OpeningDesign/Lake_Kegonsa_Home/Transfer/20150805 - driveway/20150805 - Kegonsa - Driveway.pdf

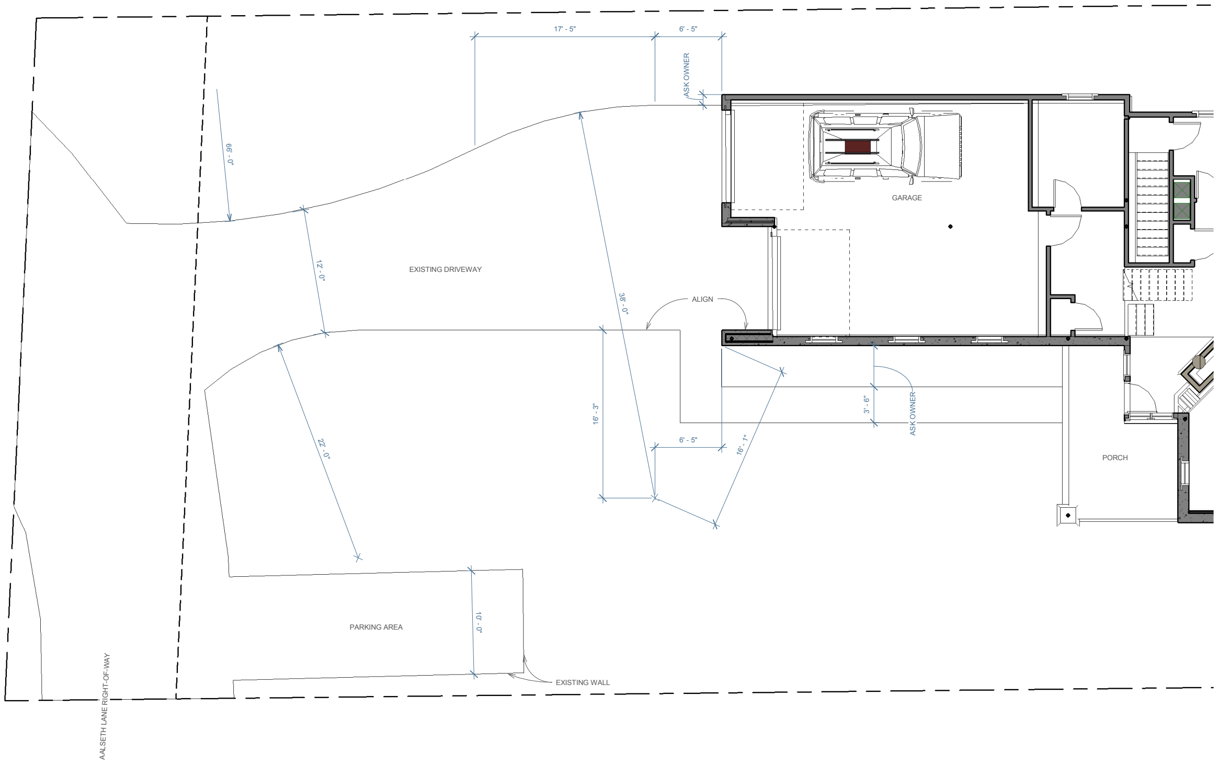
[picture p17: page 1]

EXISTING DRIVEWAY

# AALSETH LANE RIGHT-OF-WAY

GARAGE

PORCH

PARKING AREA

ALIGN

ASK OWNER

66' - 0"

22' - 0"

12' - 0"

10' - 0"

EXISTING WALL

16' - 3"

6' - 5"

3' - 6"

ASK OWNER

6' - 5"

38' - 0"

16' - 1"

17' - 5"
