OpeningDesign/Lake_Kegonsa_Home/Transfer/20150128 - lateral stability/20150128 - lateral stability.pdf

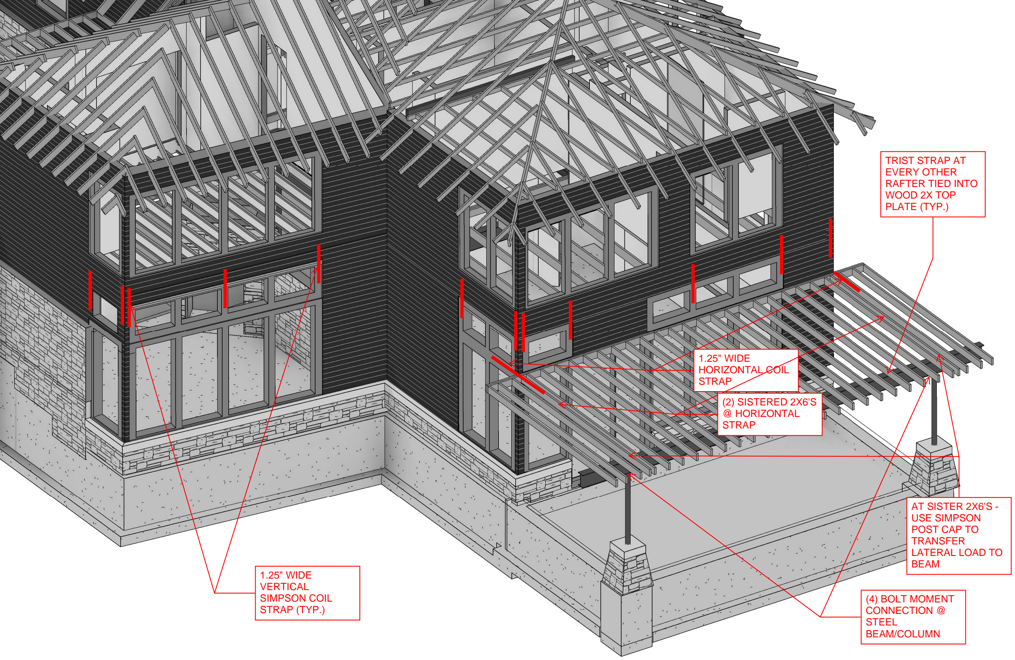
[picture p18: page 1]
