OpeningDesign/Lake_Kegonsa_Home/Transfer/20150119 - Framing - 1st Floor/20150119 - Framing - 1st Floor.pdf

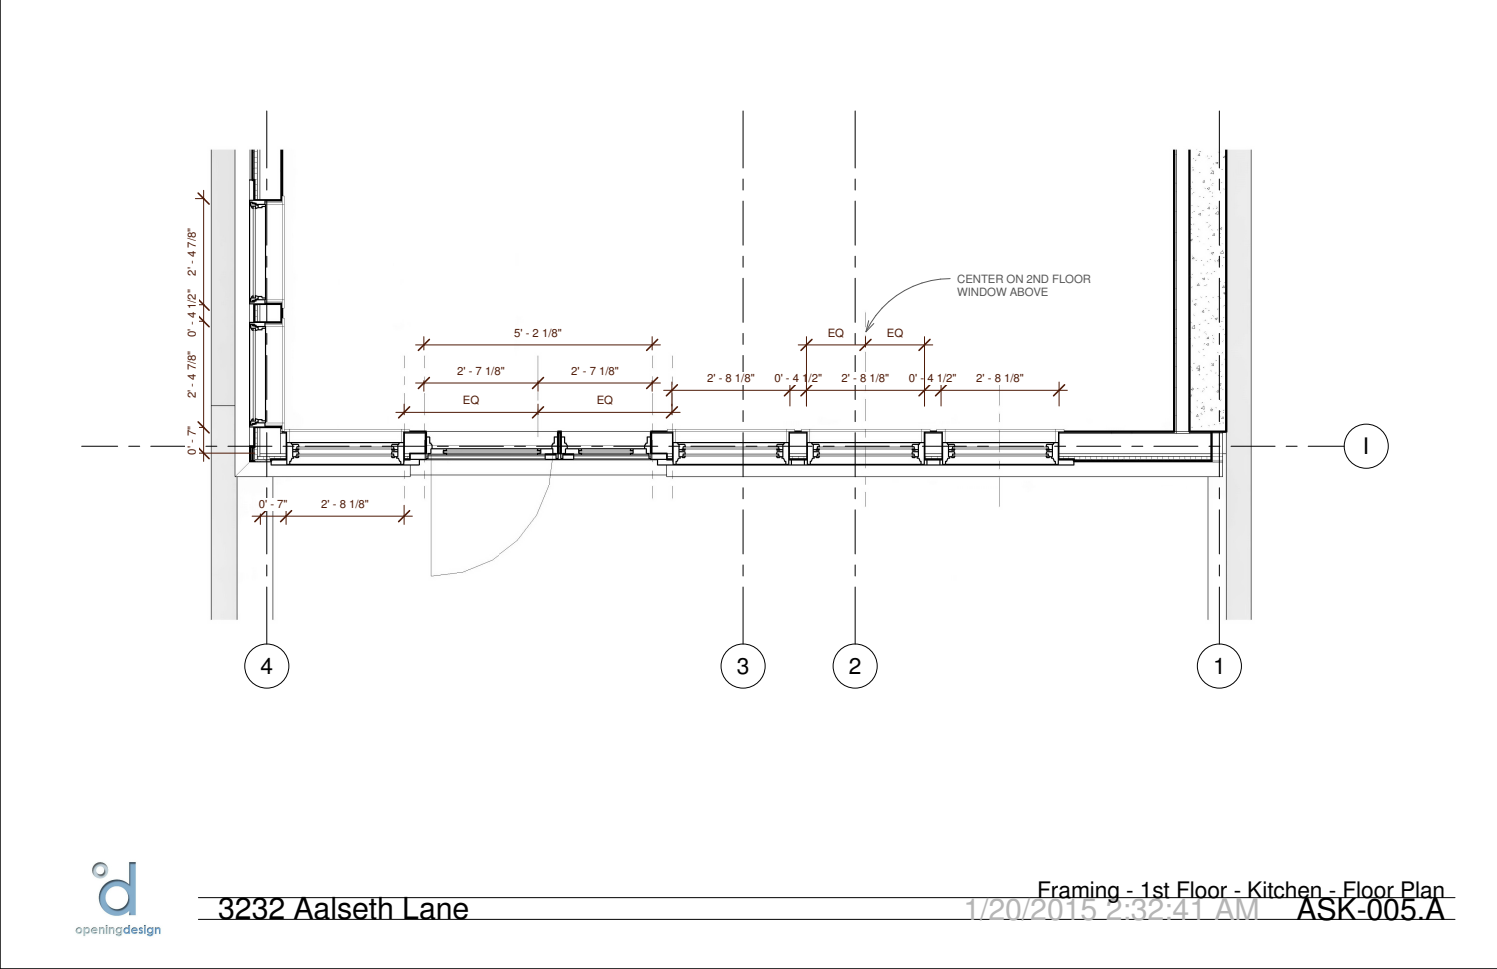
[picture p19: page 1]
ASK-005.A Framing - 1st Floor - Kitchen - Floor Plan 3232 Aalseth Lane

2' - 4 7/8" 0' - 4 1/2" 2' - 4 7/8" 0' - 7" 2' - 8 1/8" 0' - 4 1/2" 2' - 8 1/8" 0' - 4 1/2" 2' - 8 1/8" EQ EQ CENTER ON 2ND FLOOR WINDOW ABOVE EQ EQ

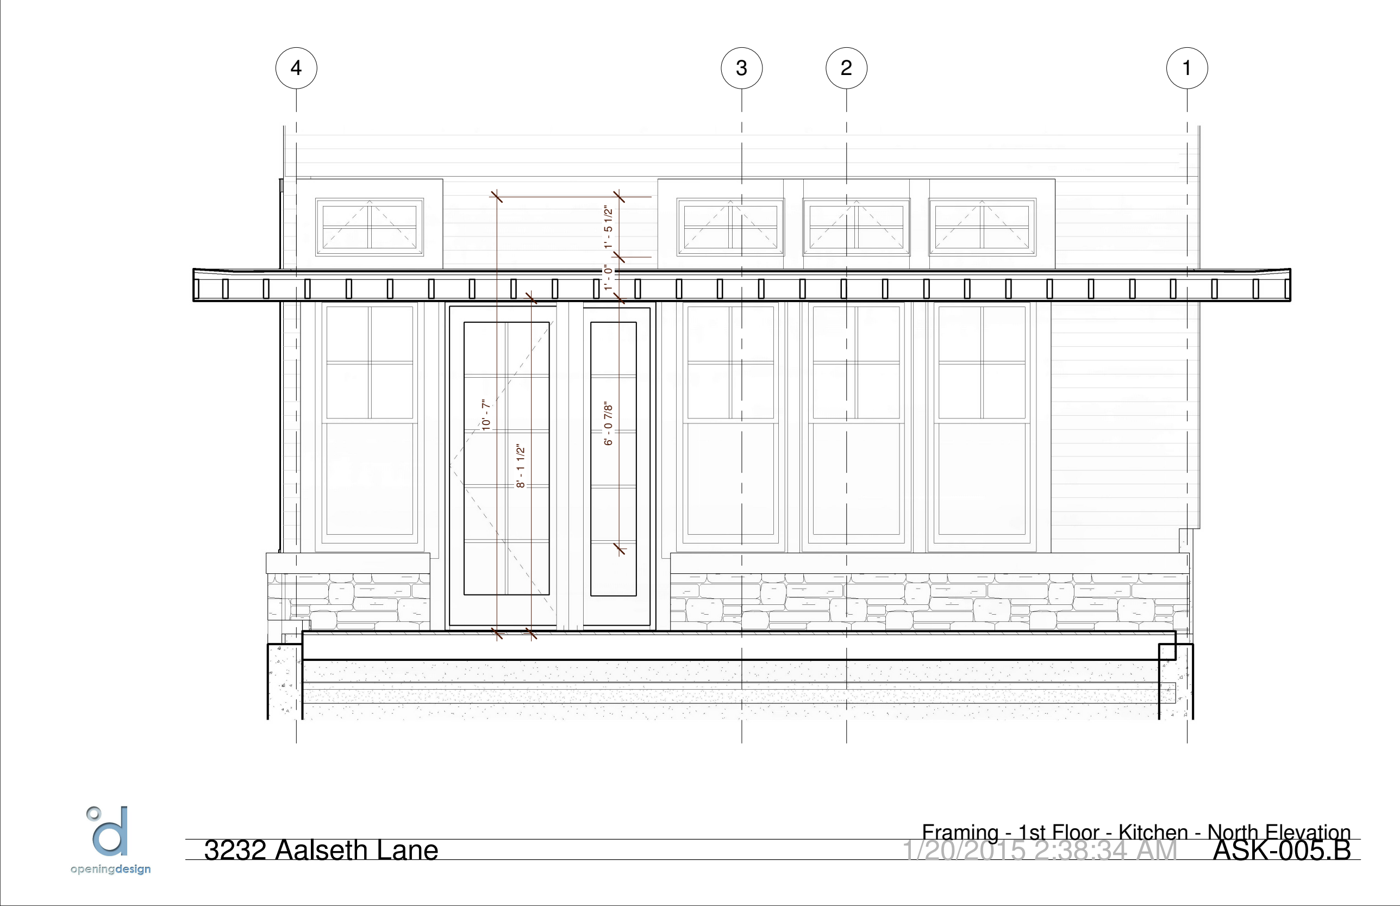
[picture p20: figure]

1/20/2015 2:38:34 AM ASK-005.B Framing - 1st Floor - Kitchen - North Elevation 3232 Aalseth Lane

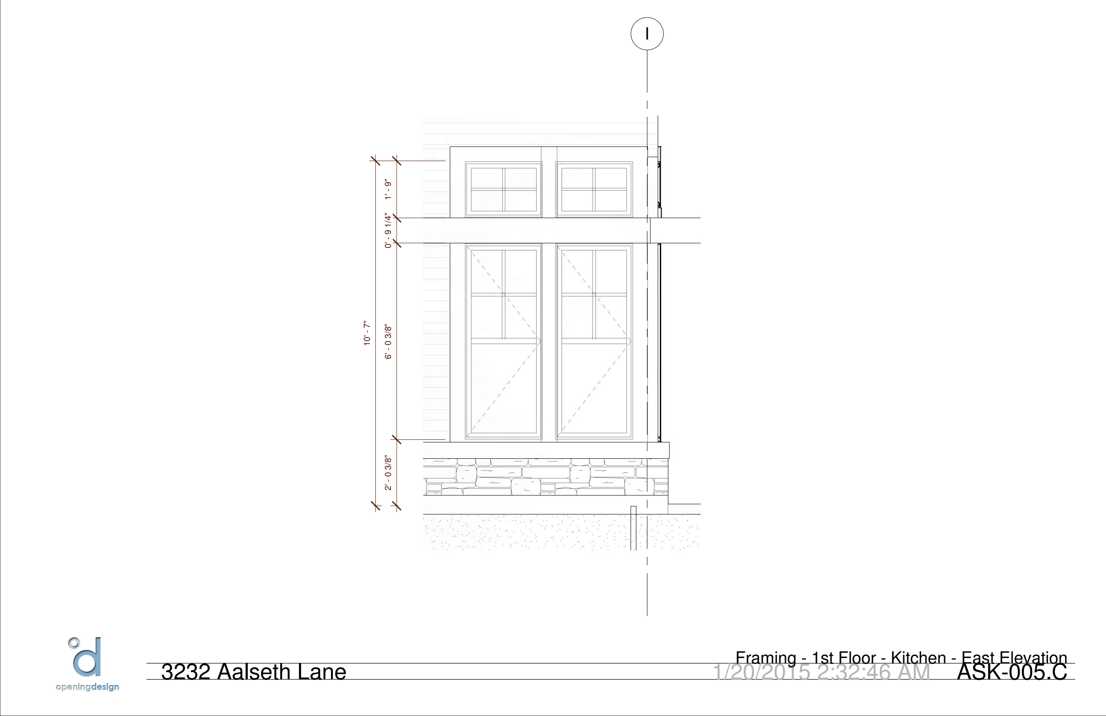
[picture p21: figure]

1' - 9" 0' - 9 1/4" 6' - 0 3/8" 2' - 0 3/8"

1/20/2015 2:32:46 AM ASK-005.C Framing - 1st Floor - Kitchen - East Elevation 3232 Aalseth Lane

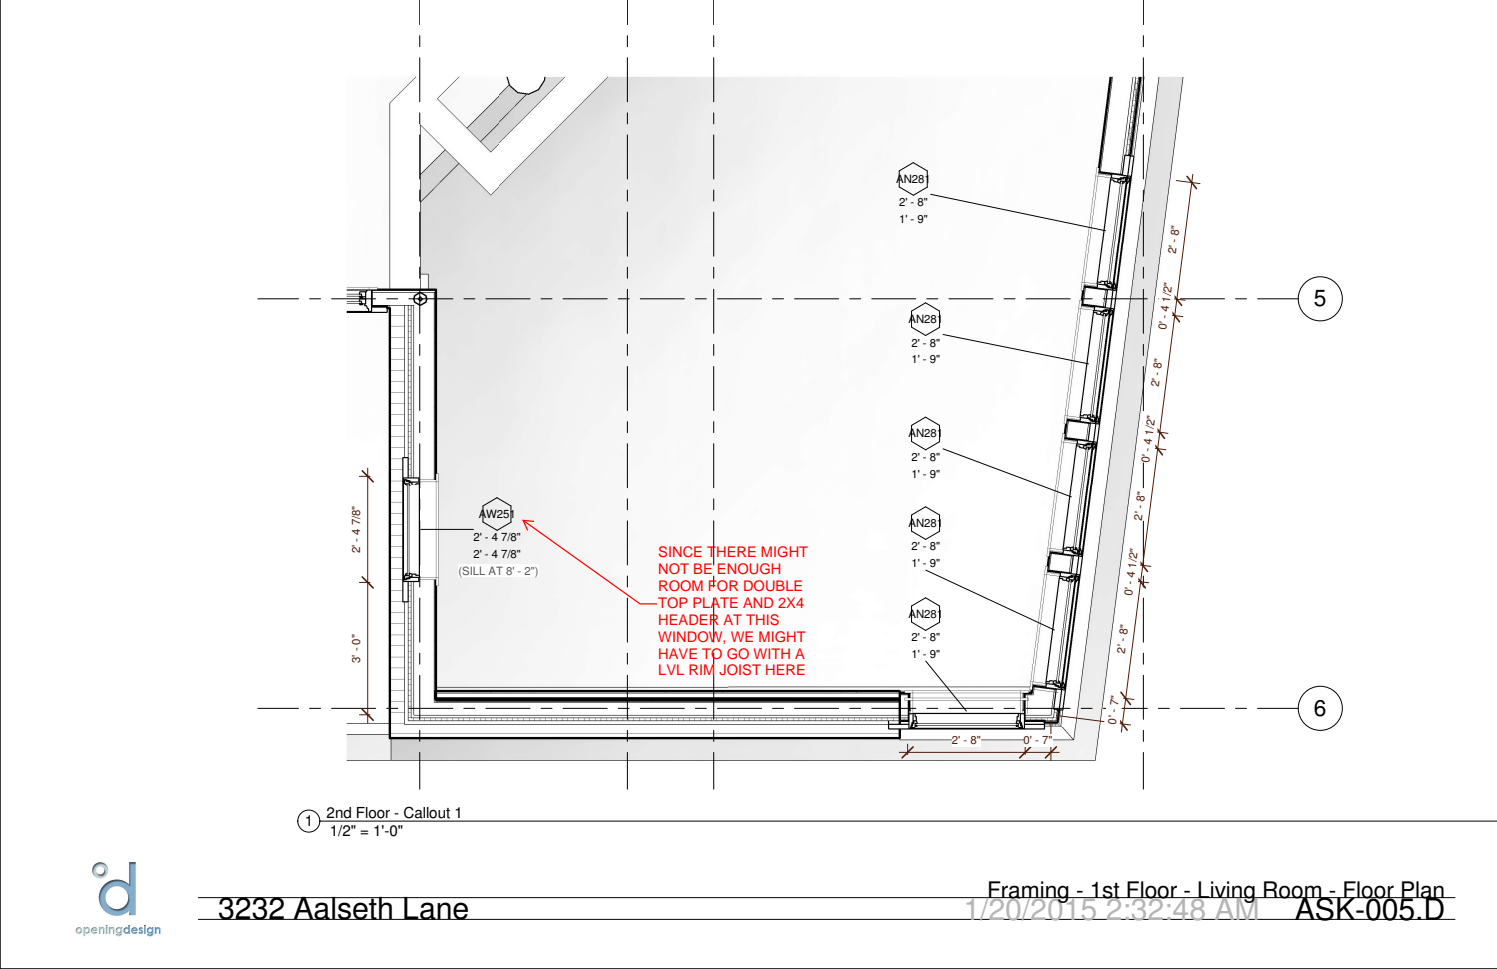
[picture p22: page 4]
(SILL AT 8' - 2"); ASK-005.D Framing - 1st Floor - Living Room - Floor Plan 3232 Aalseth Lane; 1/2" = 1'-0" 1 2nd Floor - Callout 1

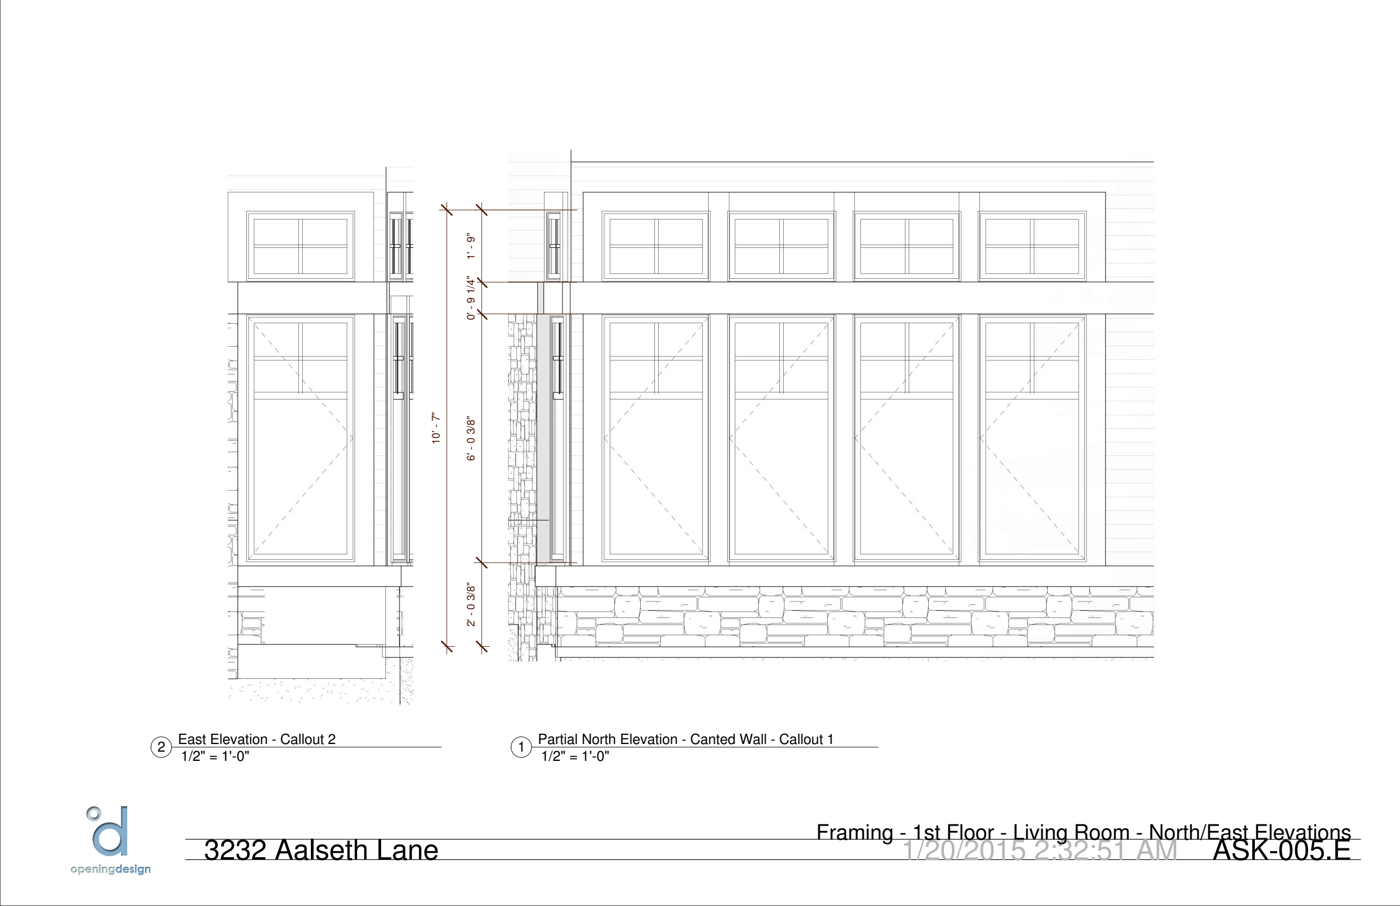
[picture p23: figure]

2' - 0 3/8" 6' - 0 3/8" 0' - 9 1/4" 1' - 9"

1/20/2015 2:32:51 AM ASK-005.E Framing - 1st Floor - Living Room - North/East Elevations 3232 Aalseth Lane

1/2" = 1'-0" 1 Partial North Elevation - Canted Wall - Callout 1 1/2" = 1'-0" 2 East Elevation - Callout 2
