OpeningDesign/Lake_Kegonsa_Home/Transfer/20150122 - 1st Floor Plan/20150122 - 1st Floor Plan.pdf

D | H
B | J

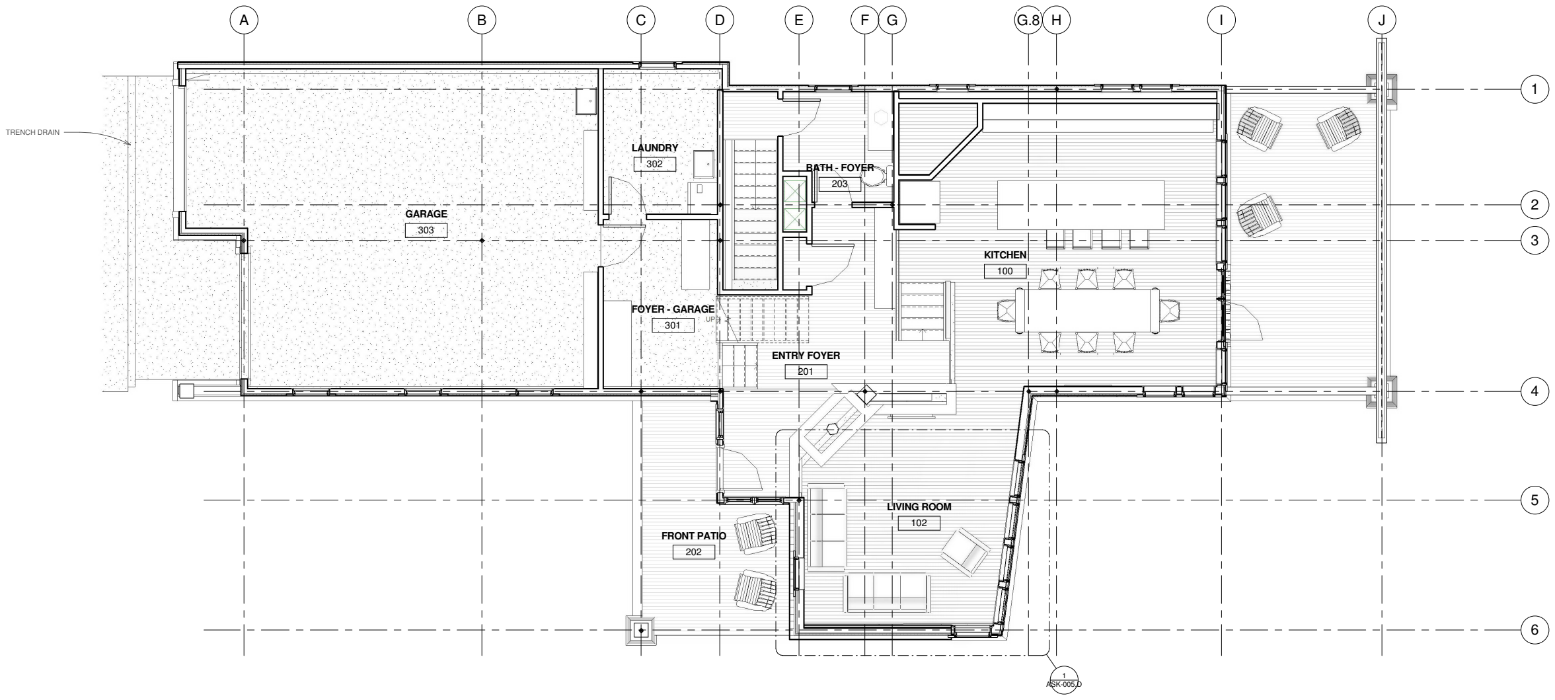
[picture p24: page 1]

2

4

A | F | G

3

5

E

1

6

C | I

TRENCH DRAIN

KITCHEN

100

LIVING ROOM

102

ENTRY FOYER

201

FRONT PATIO

202

BATH - FOYER

203

FOYER - GARAGE

301

LAUNDRY

302

GARAGE

303

G.8

ASK-005.D

1
