OpeningDesign/Lake_Kegonsa_Home/Transfer/20150125 - Entry/ASK-007b - Entry.pdf

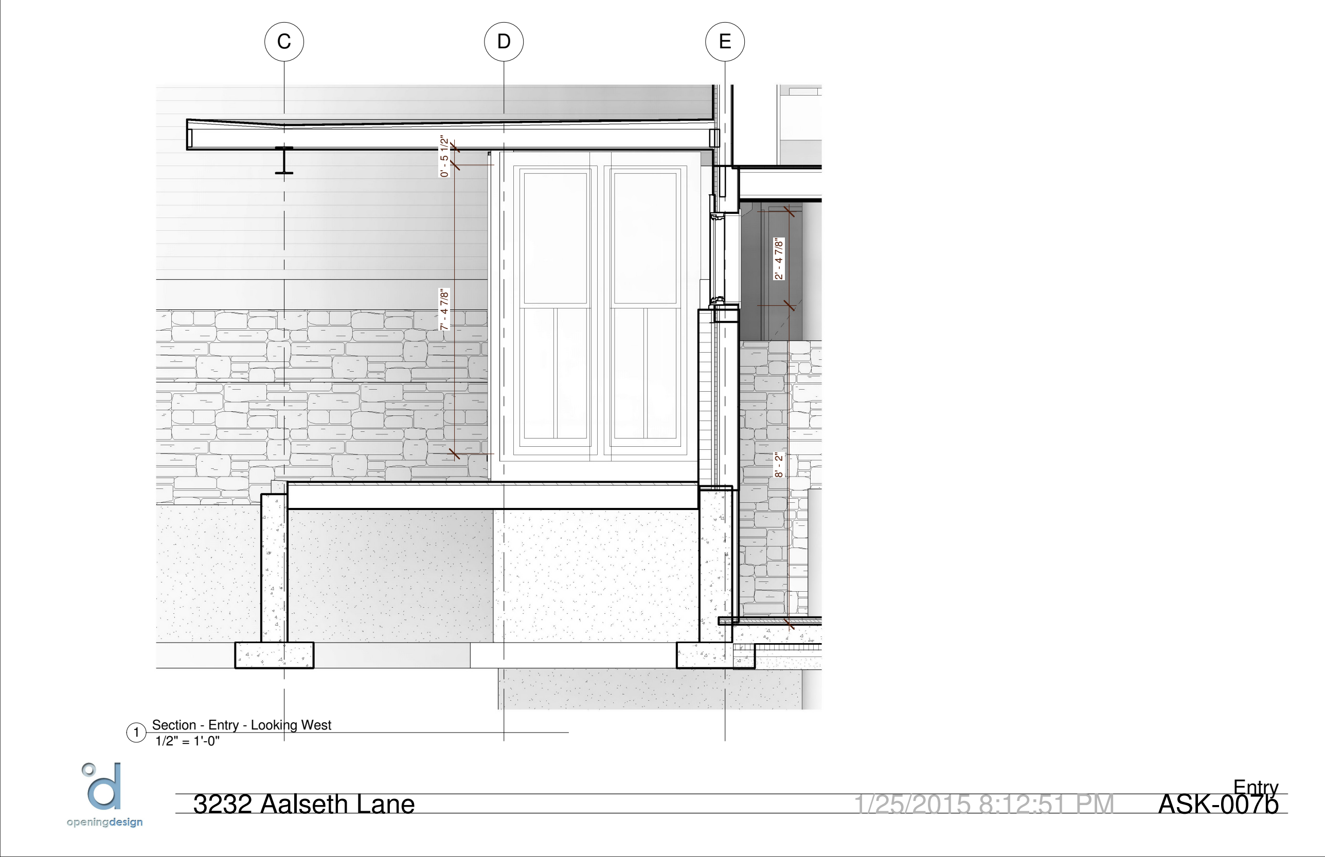
[picture p25: page 1]

C | D | E

0' - 5 1/2" 7' - 4 7/8"

8' - 2" 2' - 4 7/8"

1/25/2015 8:12:51 PM ASK-007b Entry 3232 Aalseth Lane

1/2" = 1'-0" 1 Section - Entry - Looking West
