OpeningDesign/Lake_Kegonsa_Home/Transfer/20150106 - basement and roof structure/20150106_ Structural - Basement.pdf

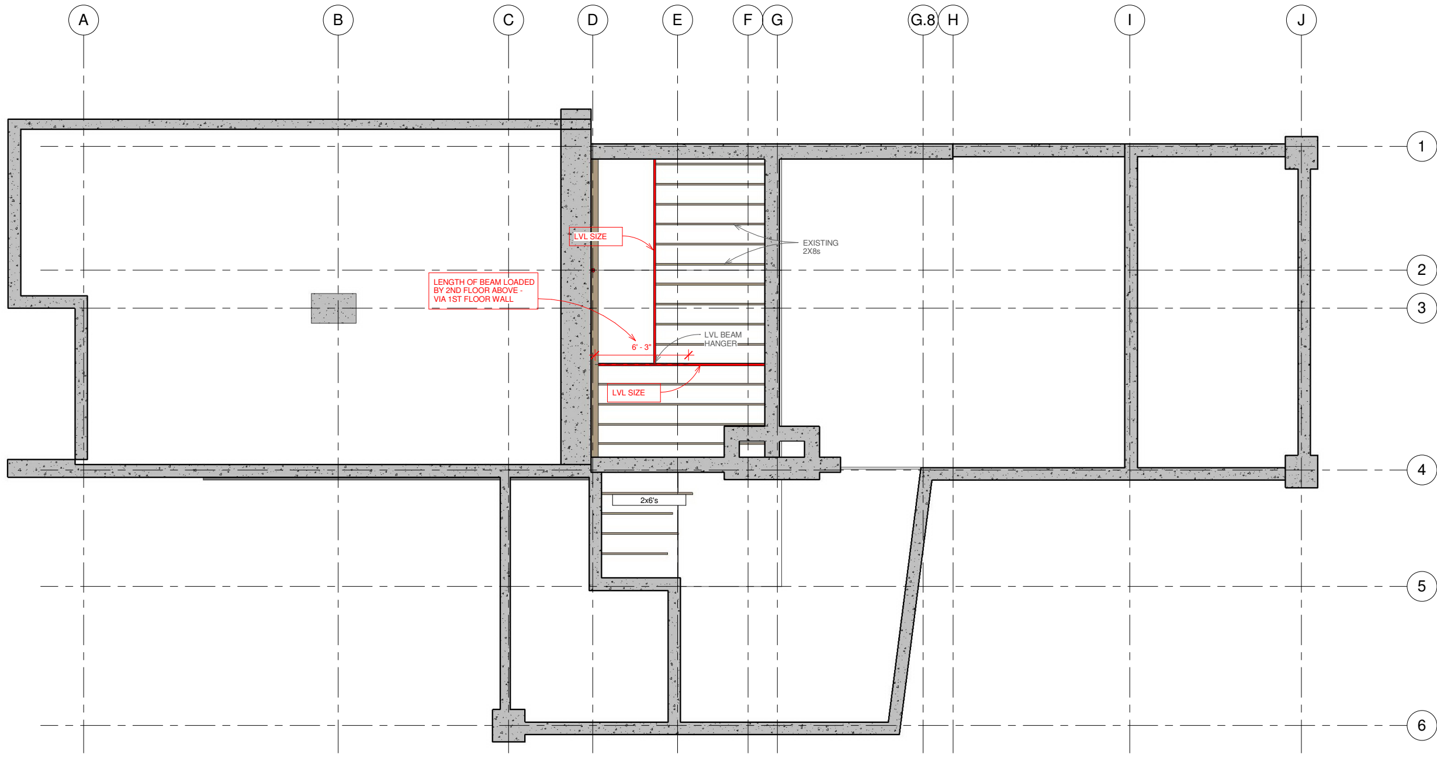
[picture p26: page 1]

D | H

2

B | J

4

A | F | G

3

5

E

1

6

C | I

LVL SIZE

LVL SIZE

6' - 3"

LENGTH OF BEAM LOADED
BY 2ND FLOOR ABOVE -
VIA 1ST FLOOR WALL

LVL BEAM
HANGER

EXISTING
2X8s

2x6's

G.8
