OpeningDesign/Lake_Kegonsa_Home/Transfer/20150106 - basement and roof structure/20150106_ Structural - roof plan.pdf

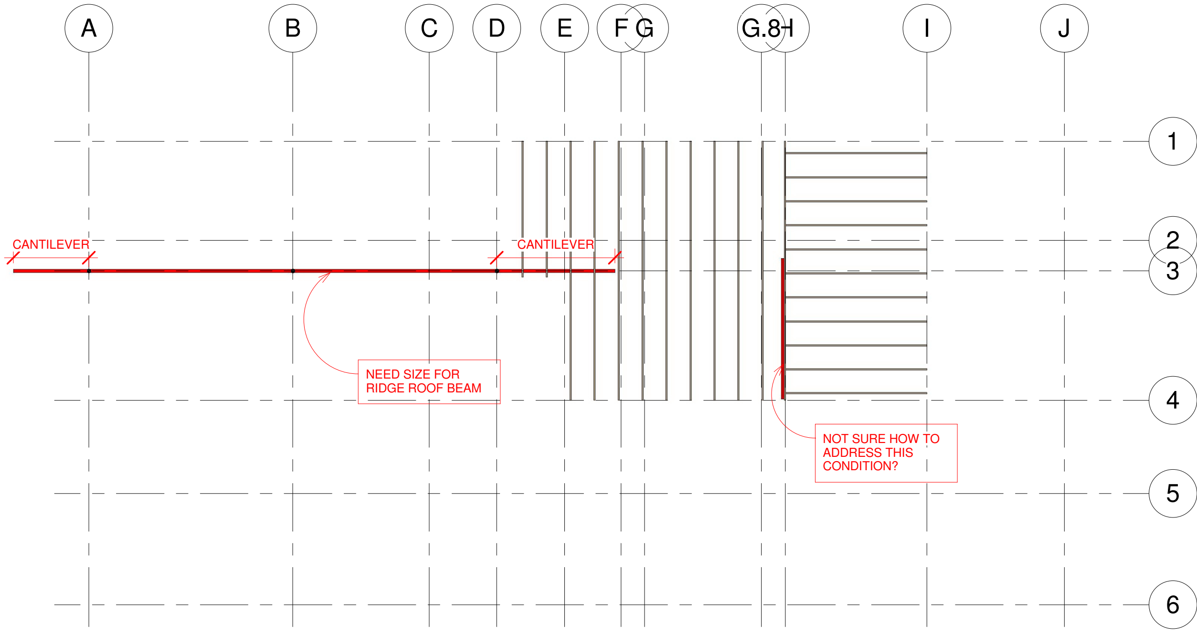
[picture p27: page 1]

D | H

2

B | J

4

A | F G

3

5

E

1

6

C | G.8 | I

NOT SURE HOW TO
ADDRESS THIS
CONDITION?

NEED SIZE FOR
RIDGE ROOF BEAM
CANTILEVER | CANTILEVER
