OpeningDesign/Lake_Kegonsa_Home/Transfer/Endres Mfg_20141222/Question 3.pdf

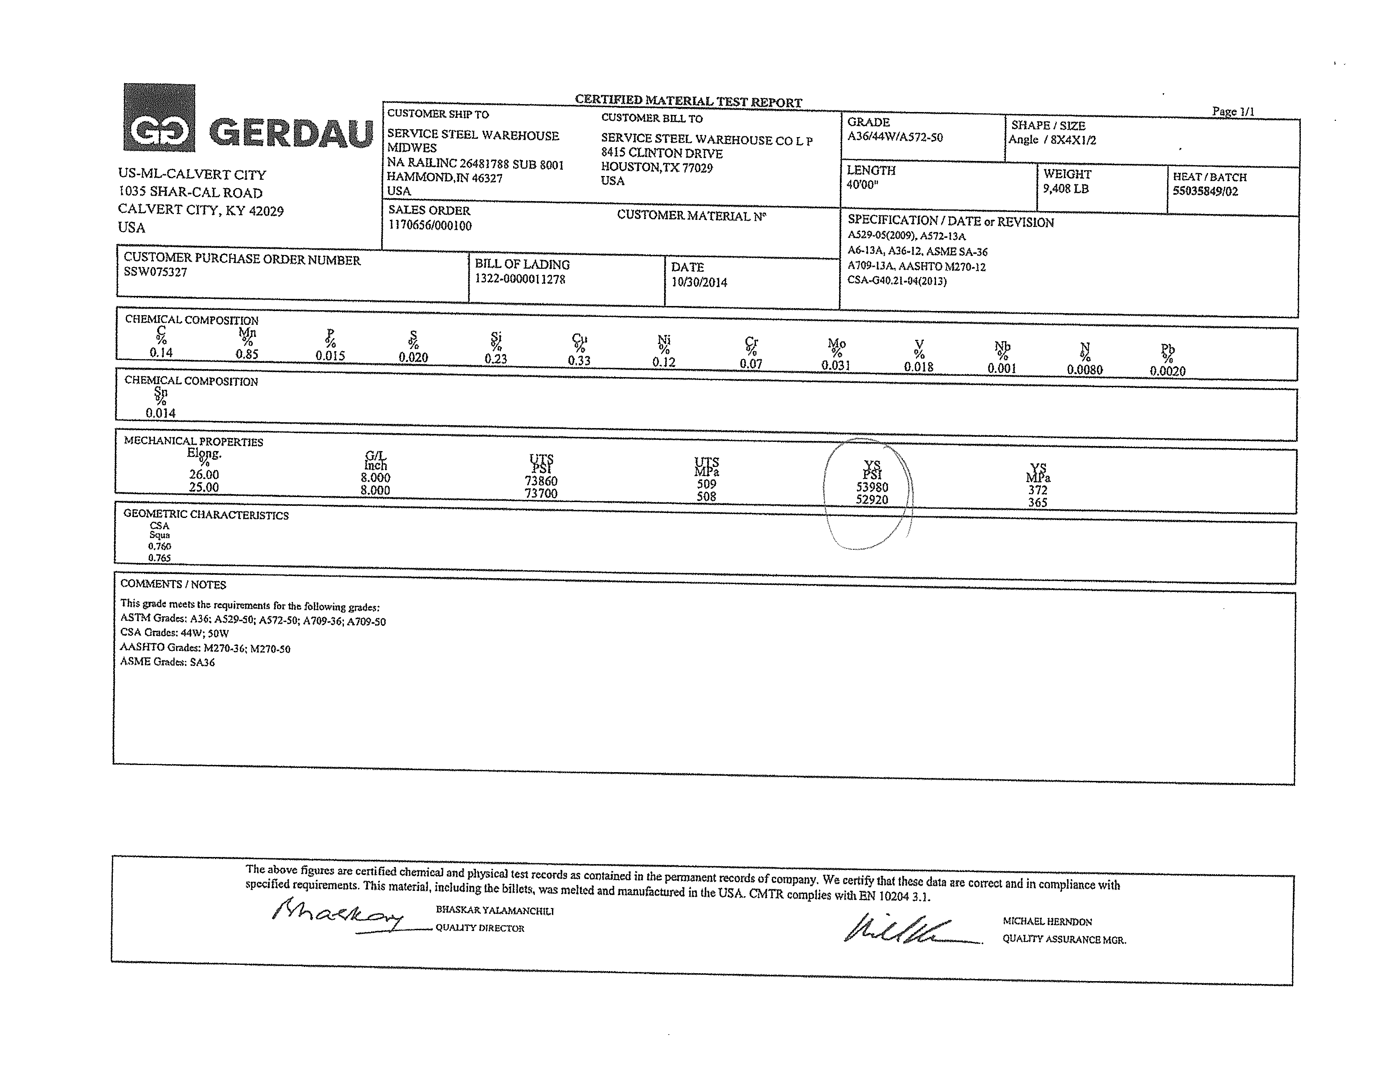
[picture p28: page 1]
