OpeningDesign/Lake_Kegonsa_Home/Transfer/Endres Mfg_20141222/Question 4.pdf

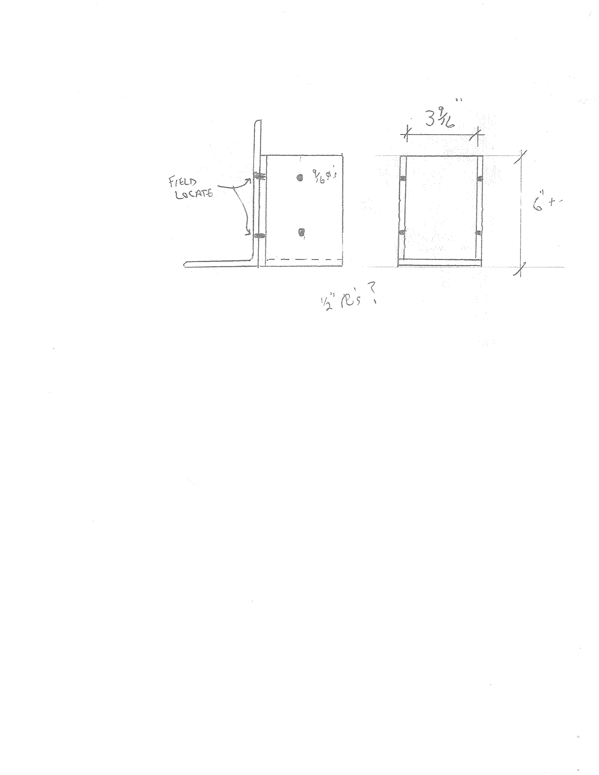
[picture p29: page 1]
