OpeningDesign/Lake_Kegonsa_Home/As-built/Photos and Videos/2014-10-24 10.37.41.jpg

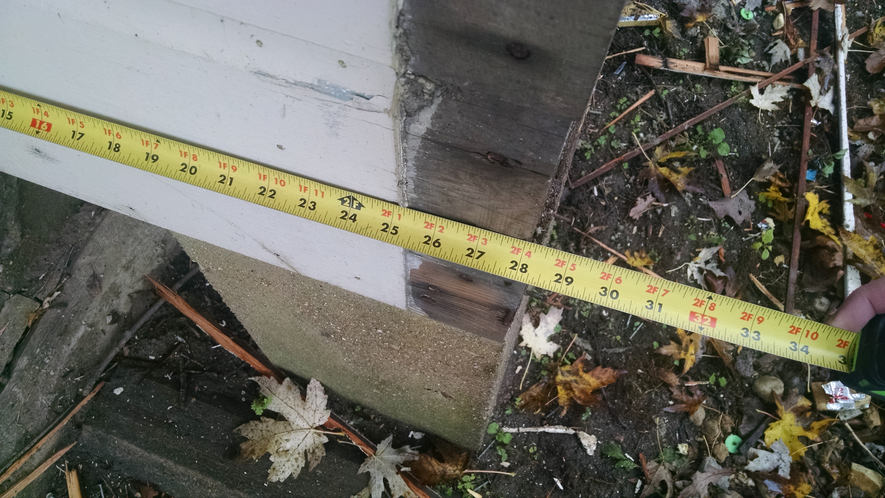
As-built/Photos and Videos/2014-10-24 10.37.41.jpg
