OpeningDesign/Lake_Kegonsa_Home/As-built/Photos and Videos/2014-10-24 10.46.05.jpg

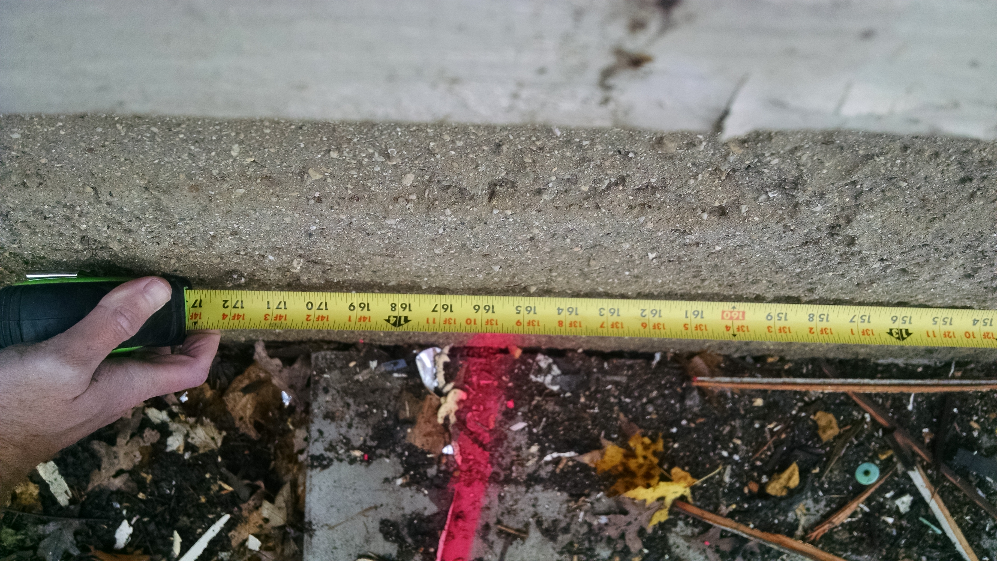
As-built/Photos and Videos/2014-10-24 10.46.05.jpg
