OpeningDesign/Lake_Kegonsa_Home/As-built/Photos and Videos/2014-11-19 15.27.34.jpg

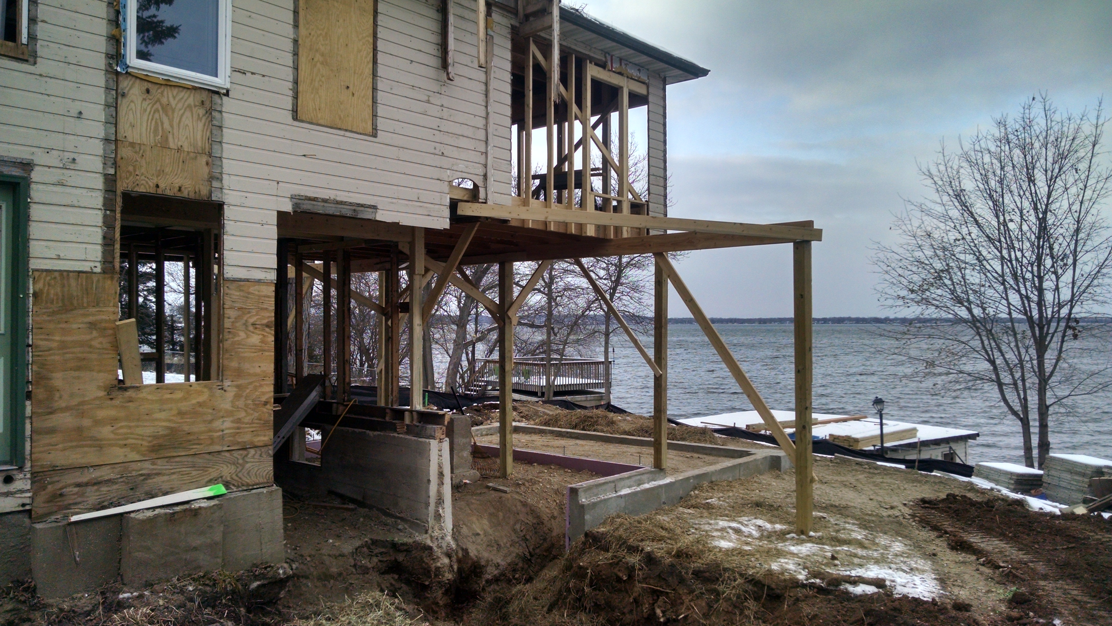
As-built/Photos and Videos/2014-11-19 15.27.34.jpg
