OpeningDesign/Lake_Kegonsa_Home/As-built/plat.jpg

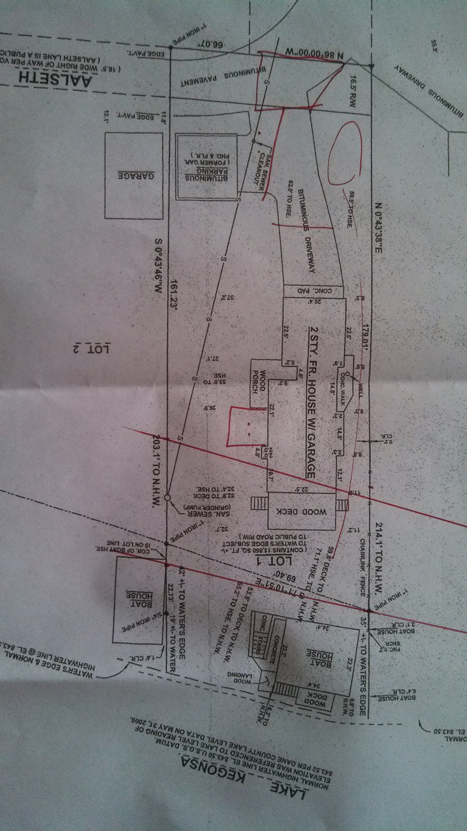
As-built/plat.jpg
