OpeningDesign/Lake_Kegonsa_Home/As-built/site photos/2014-07-19 14.10.41.jpg

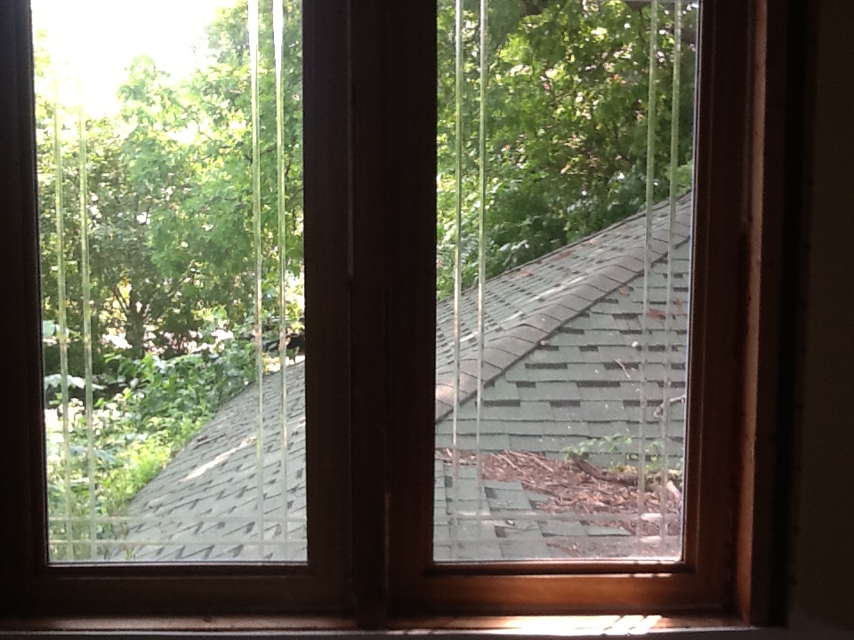
As-built/site photos/2014-07-19 14.10.41.jpg
