OpeningDesign/Lake_Kegonsa_Home/As-built/site photos/2014-07-19 14.11.17.jpg

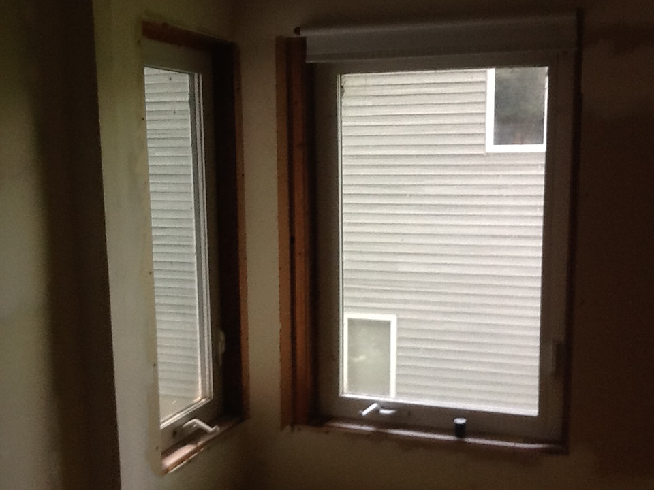
As-built/site photos/2014-07-19 14.11.17.jpg
