OpeningDesign/Lake_Kegonsa_Home/Info/casement - grilles.jpg

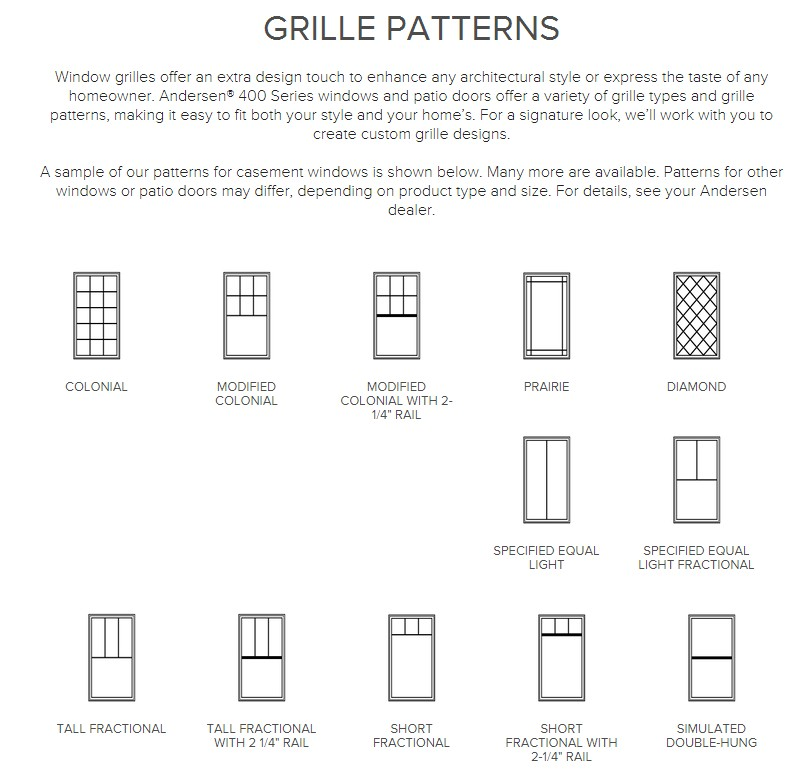
Info/casement - grilles.jpg
