OpeningDesign/Lake_Kegonsa_Home/Info/double hung - grilles.jpg

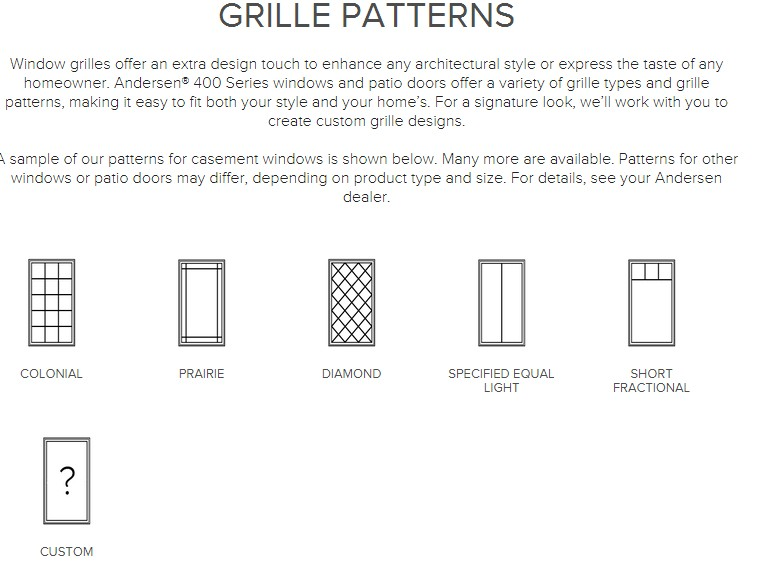
Info/double hung - grilles.jpg
