OpeningDesign/Lake_Kegonsa_Home/Model/Drain-Trench-Zurn-Z886/Product_Image-Zurn-Z886.jpg

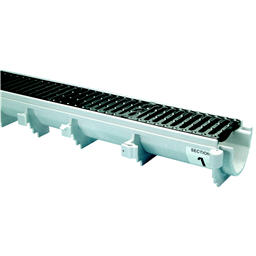
Model/Drain-Trench-Zurn-Z886/Product_Image-Zurn-Z886.jpg
