OpeningDesign/Lake_Kegonsa_Home/Model/turning radius.png

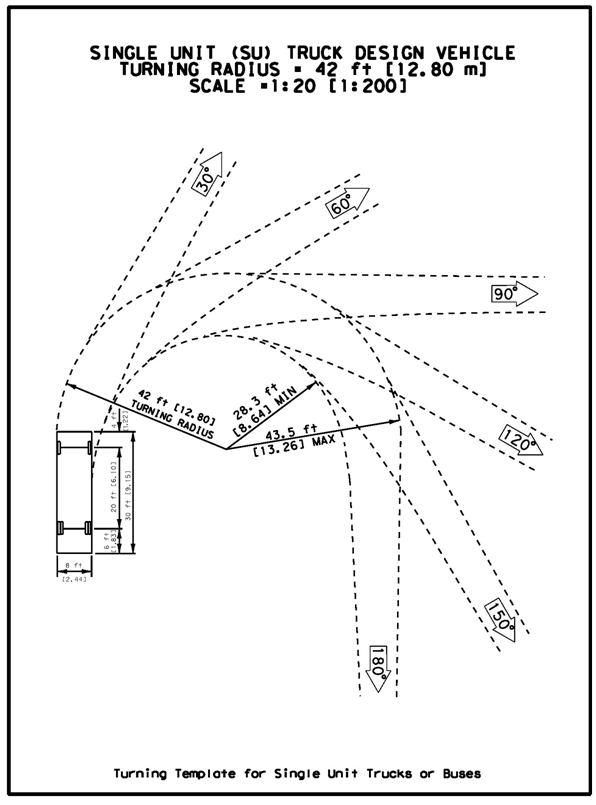
Model/turning radius.png
