OpeningDesign/Lake_Kegonsa_Home/Out/20140901 - Progress set/Lake_Kegonsa_Home Page 011.png

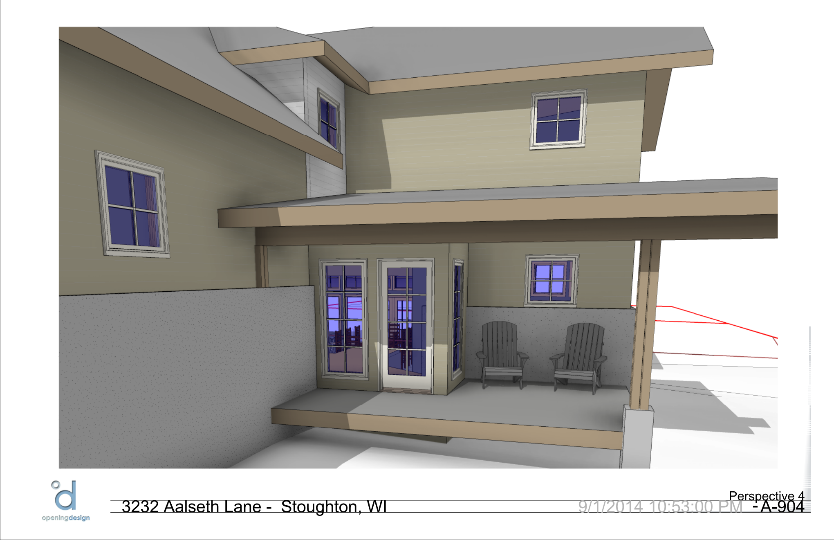
Out/20140901 - Progress set/Lake_Kegonsa_Home Page 011.png
