OpeningDesign/Lake_Kegonsa_Home/Out/20140913 - for review/Lake_Kegonsa_Home Page 002.png

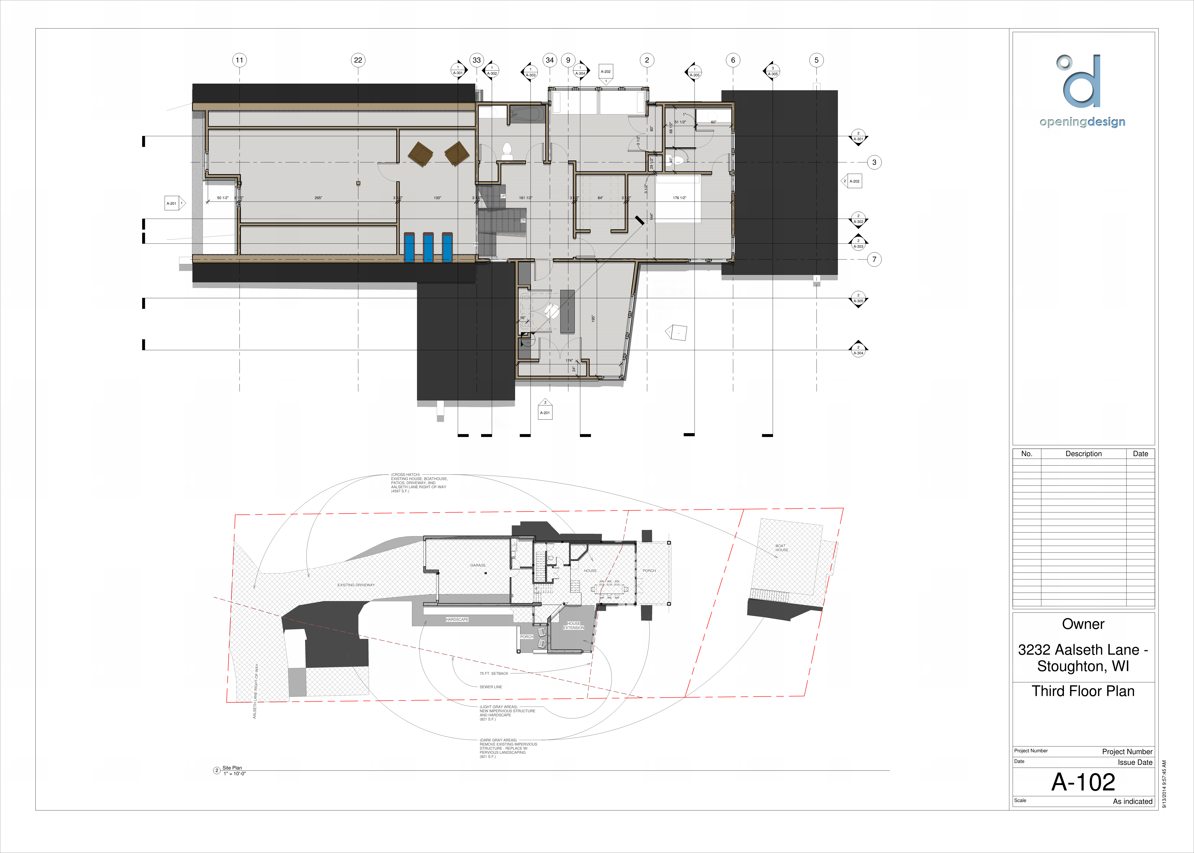
Out/20140913 - for review/Lake_Kegonsa_Home Page 002.png
