OpeningDesign/Lake_Kegonsa_Home/Out/20140929 - Plans for Plumber/ScreenHunter_159 Sep. 29 16.08.jpg

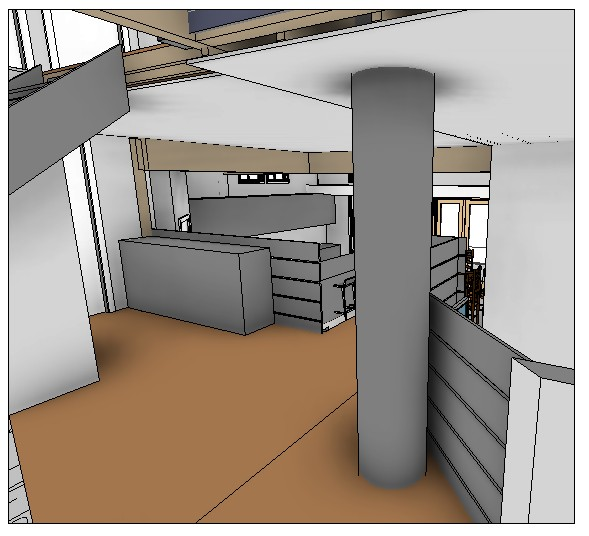
Out/20140929 - Plans for Plumber/ScreenHunter_159 Sep. 29 16.08.jpg
