OpeningDesign/Lake_Kegonsa_Home/Out/20140929 - Plans for Plumber/ScreenHunter_160 Sep. 29 16.10.jpg

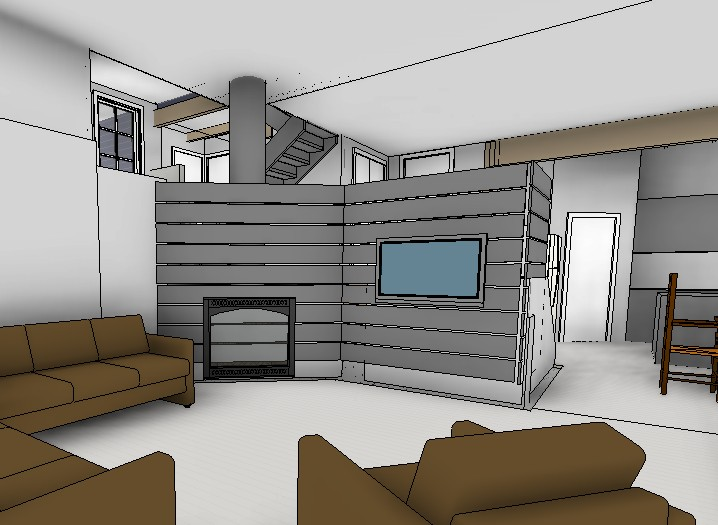
Out/20140929 - Plans for Plumber/ScreenHunter_160 Sep. 29 16.10.jpg
