OpeningDesign/Lake_Kegonsa_Home/Out/20141021 - structural screencapture/ScreenHunter_133 Oct. 21 11.41.jpg

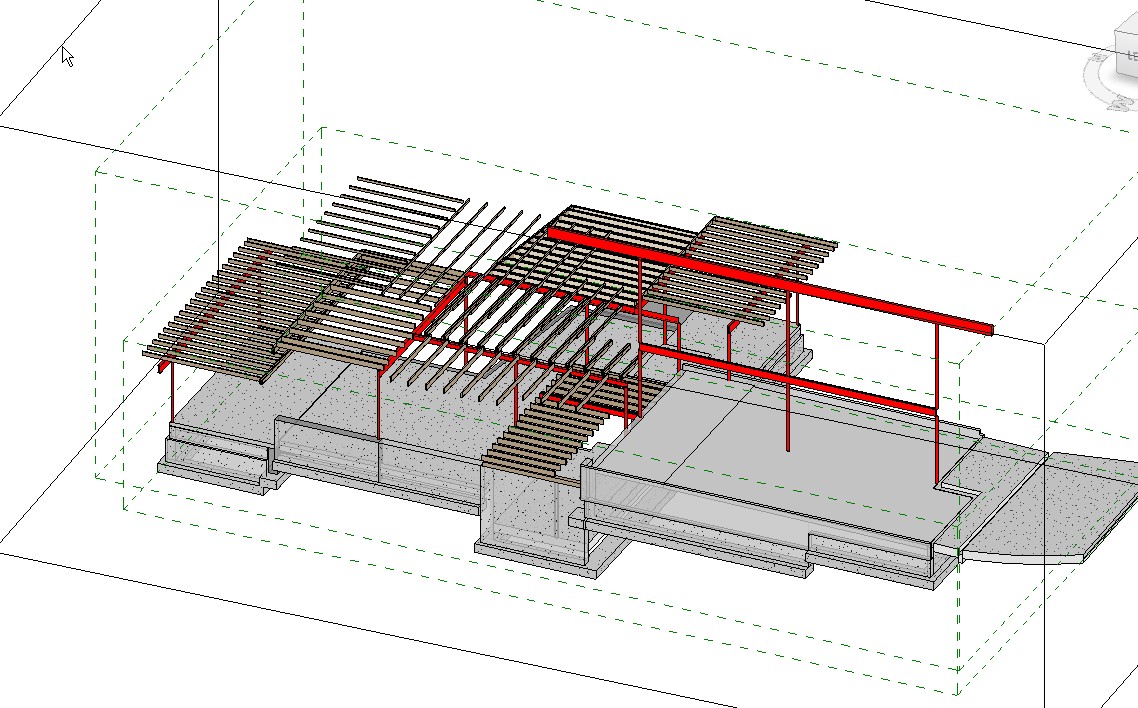
Out/20141021 - structural screencapture/ScreenHunter_133 Oct. 21 11.41.jpg
