OpeningDesign/Lake_Kegonsa_Home/Out/20141117- foundation sketches/02.jpg

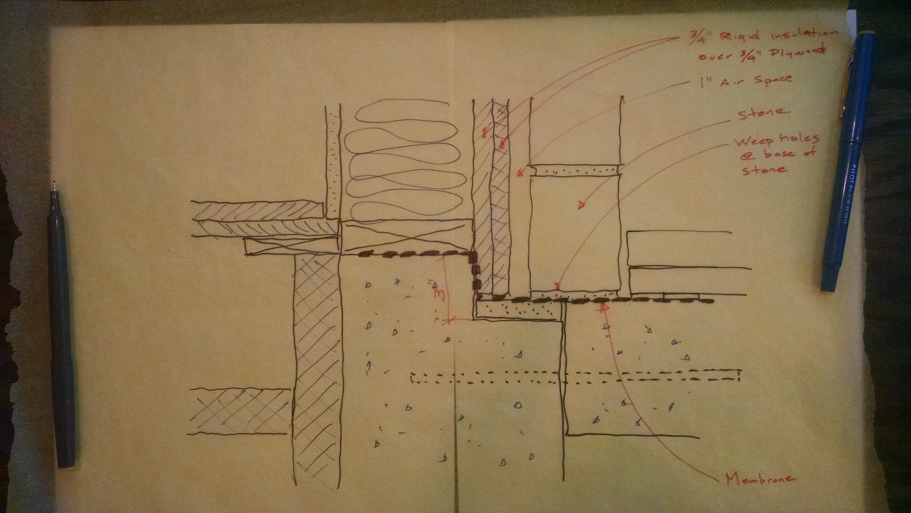
Out/20141117- foundation sketches/02.jpg
