OpeningDesign/Lake_Kegonsa_Home/Structural/Question 4.png

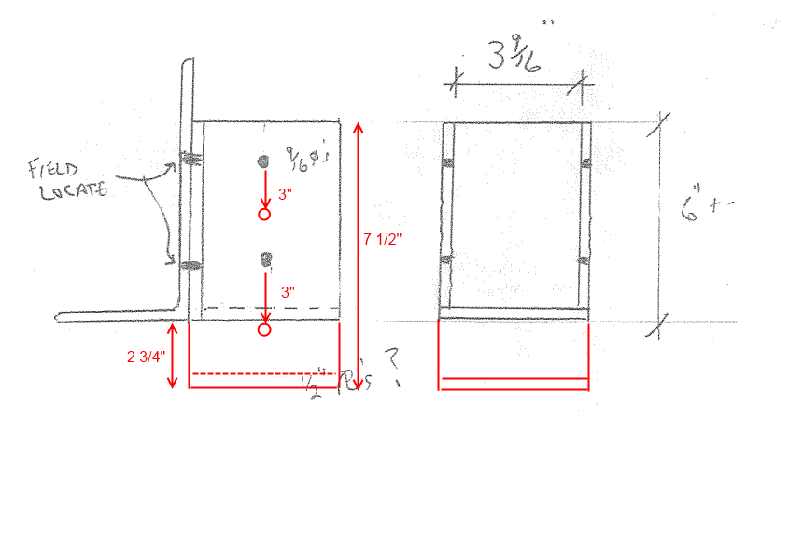
Structural/Question 4.png
