OpeningDesign/Lake_Kegonsa_Home/Transfer/Dream Kitchens_20141110_Built-in Drywall Shelves.jpg

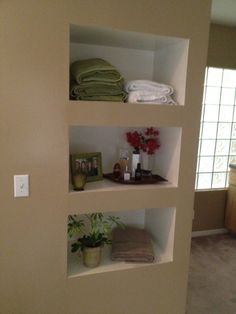
Transfer/Dream Kitchens_20141110_Built-in Drywall Shelves.jpg
