OpeningDesign/Lake_Kegonsa_Home/Transfer/Endres Mfg_20141222/Field Measurements 2.pdf

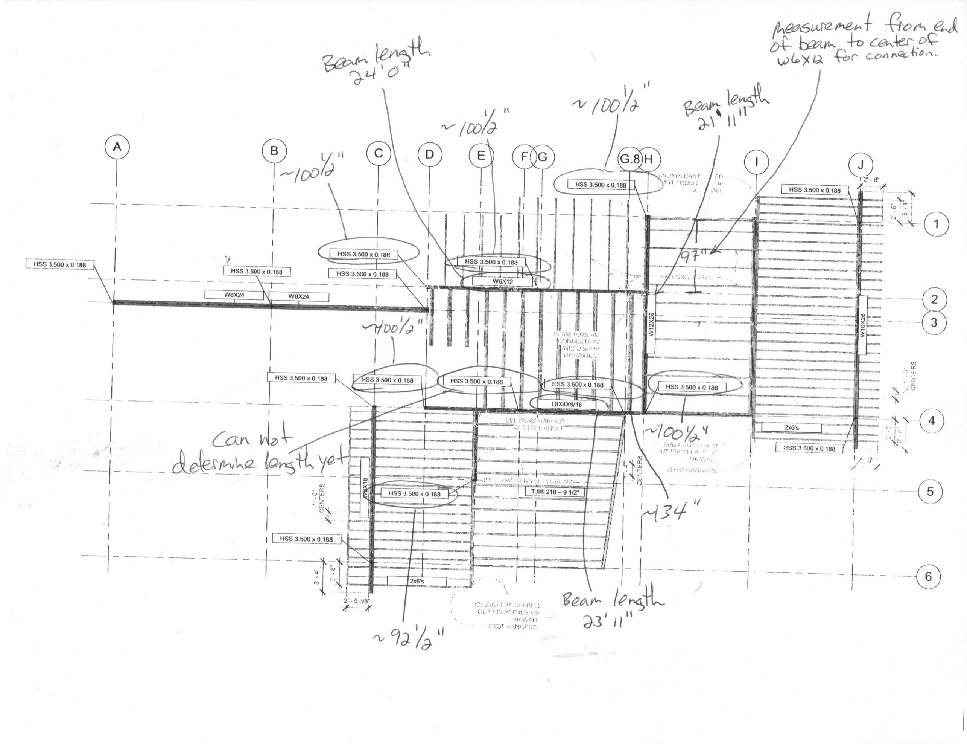
[picture p133: page 1]
