OpeningDesign/Lake_Kegonsa_Home/Transfer/20150531 - den framing/20150531 - 2nd Floor.pdf

A | B | C | D | E | F | G | H | I

G.8

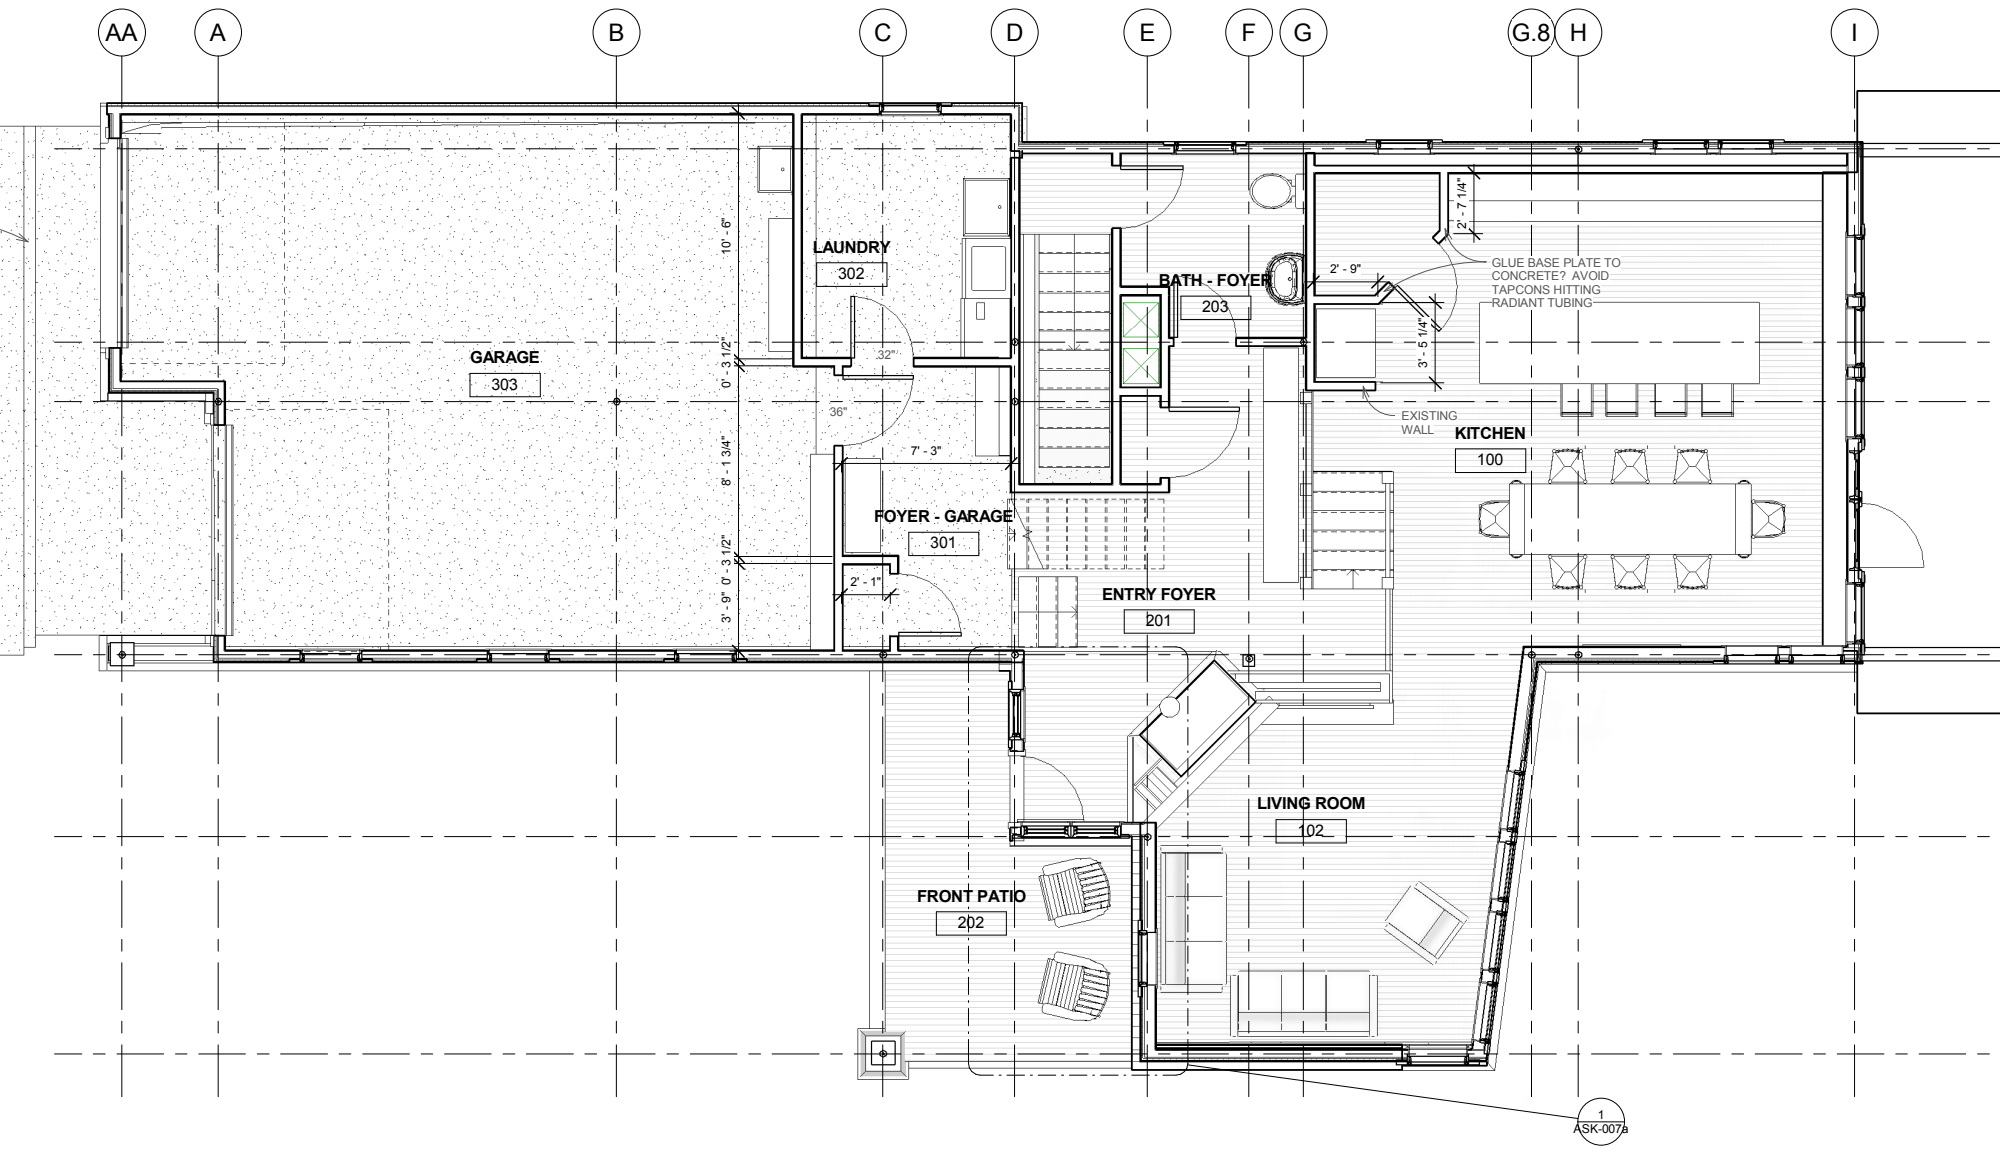
[picture p134: page 1]
KITCHEN; LIVING ROOM; ENTRY FOYER; FRONT PATIO; BATH - FOYER; FOYER - GARAGE; LAUNDRY; GARAGE; ASK-007a; EXISTING; WALL; GLUE; BASE PLATE TO; CONCRETE? AVOID; TAPCONS HITTING; RADIANT TUBING
