OpeningDesign/Lake_Kegonsa_Home/Transfer/20150531 - den framing/20150531 - Kegonsa - 2nd & 3rd Floor.pdf

A | B | C | D | E | F | G | H | I

G.8

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

A | B | C | D | E | F | G | H | I

405

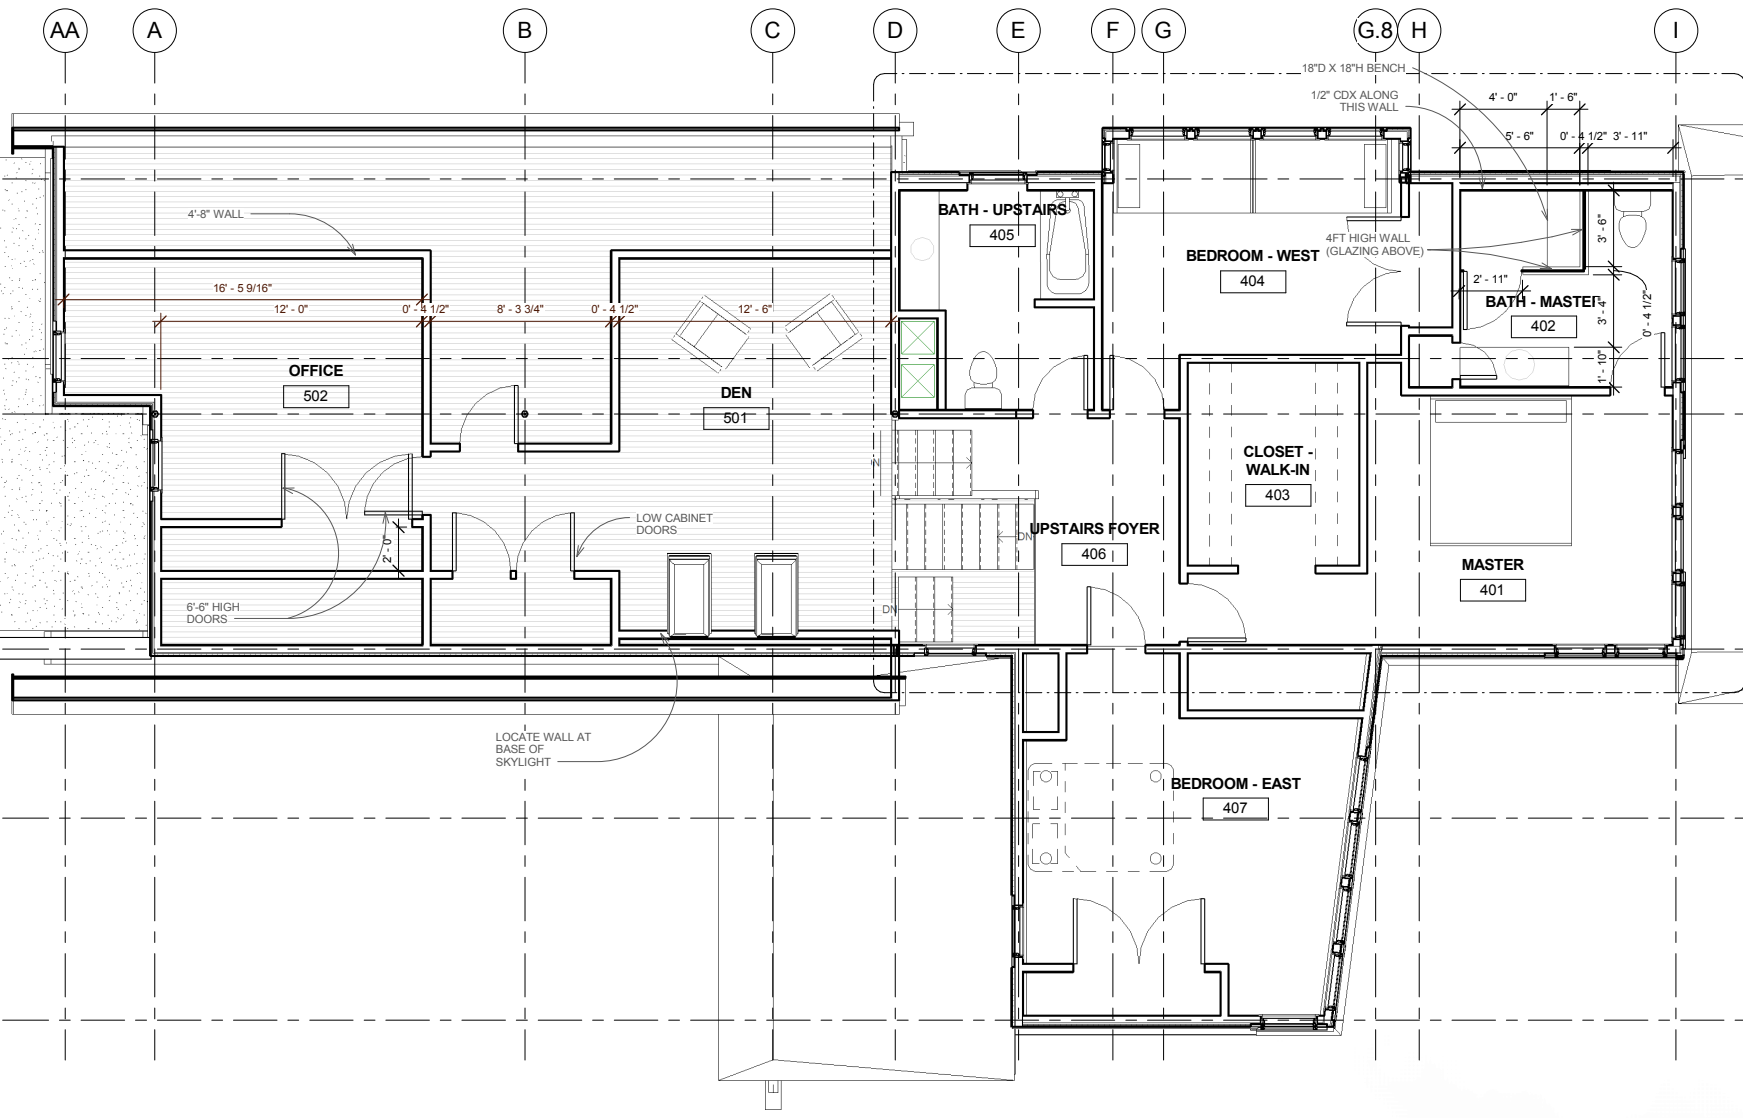
[picture p135: page 2]
BATH - MASTER; BEDROOM - EAST; BEDROOM - WEST; BATH - UPSTAIRS; UPSTAIRS FOYER; 406 MASTER; CLOSET -; WALK-IN; OFFICE; 502 DEN; 1/2" CDX ALONG; THIS WALL; 4FT HIGH WALL (GLAZING ABOVE); LOW CABINET DOORS; 6'-6" HIGH DOORS; 4'-8" WALL; 18"D X 18"H BENCH

LOCATE WALL AT
BASE OF
SKYLIGHT
