OpeningDesign/Lake_Kegonsa_Home/Transfer/20150115-ASK-003-Exterior West Wall - Window Locations/20150116-ASK-003-Exterior West Wall - Window Locations.pdf

F | G | G.8 | H | I

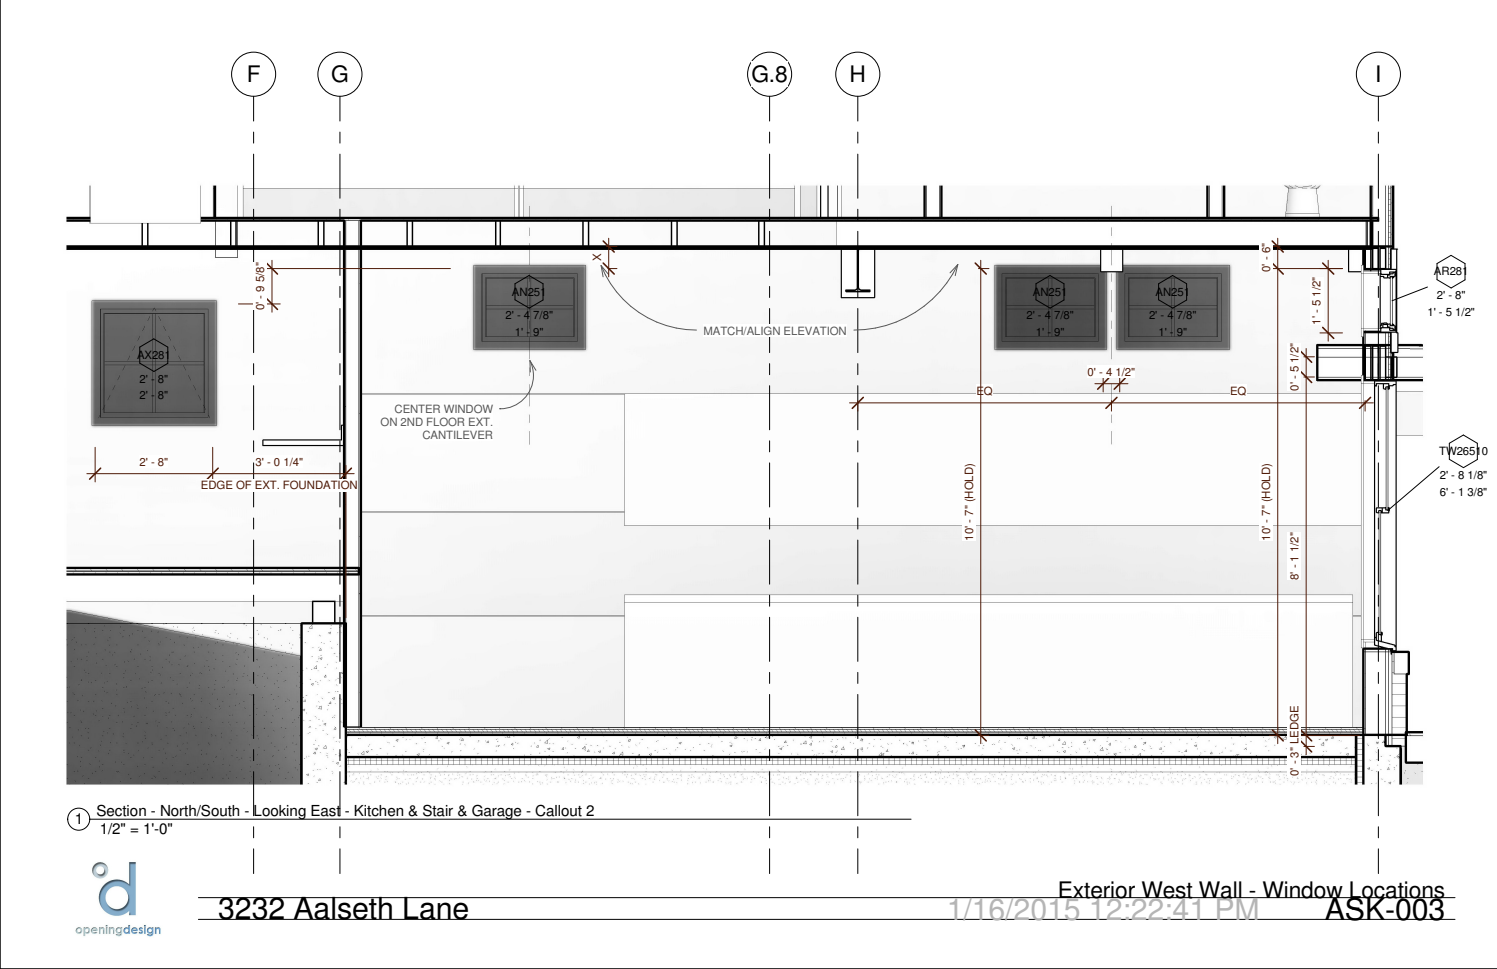
[picture p137: page 1]
0' - 3" LEDGE 8' - 1 1/2" 0' - 5 1/2"; CANTILEVER; 10' - 7" (HOLD); ASK-003 - Exterior West Wall - Window Locations 3232 Aalseth Lane

MATCH/ALIGN ELEVATION

CENTER WINDOW
ON 2ND FLOOR EXT.

EDGE OF EXT. FOUNDATION

1/2" = 1'-0" 1 Section - North/South - Looking East - Kitchen & Stair & Garage - Callout 2
