OpeningDesign/Lake_Kegonsa_Home/Out/20141118 - kegonsa foundation plans/20141118- kegonsa foundation plan.pdf

### 2042 Barber Dr. | Stoughton, WI 53589 | 773-425-6456

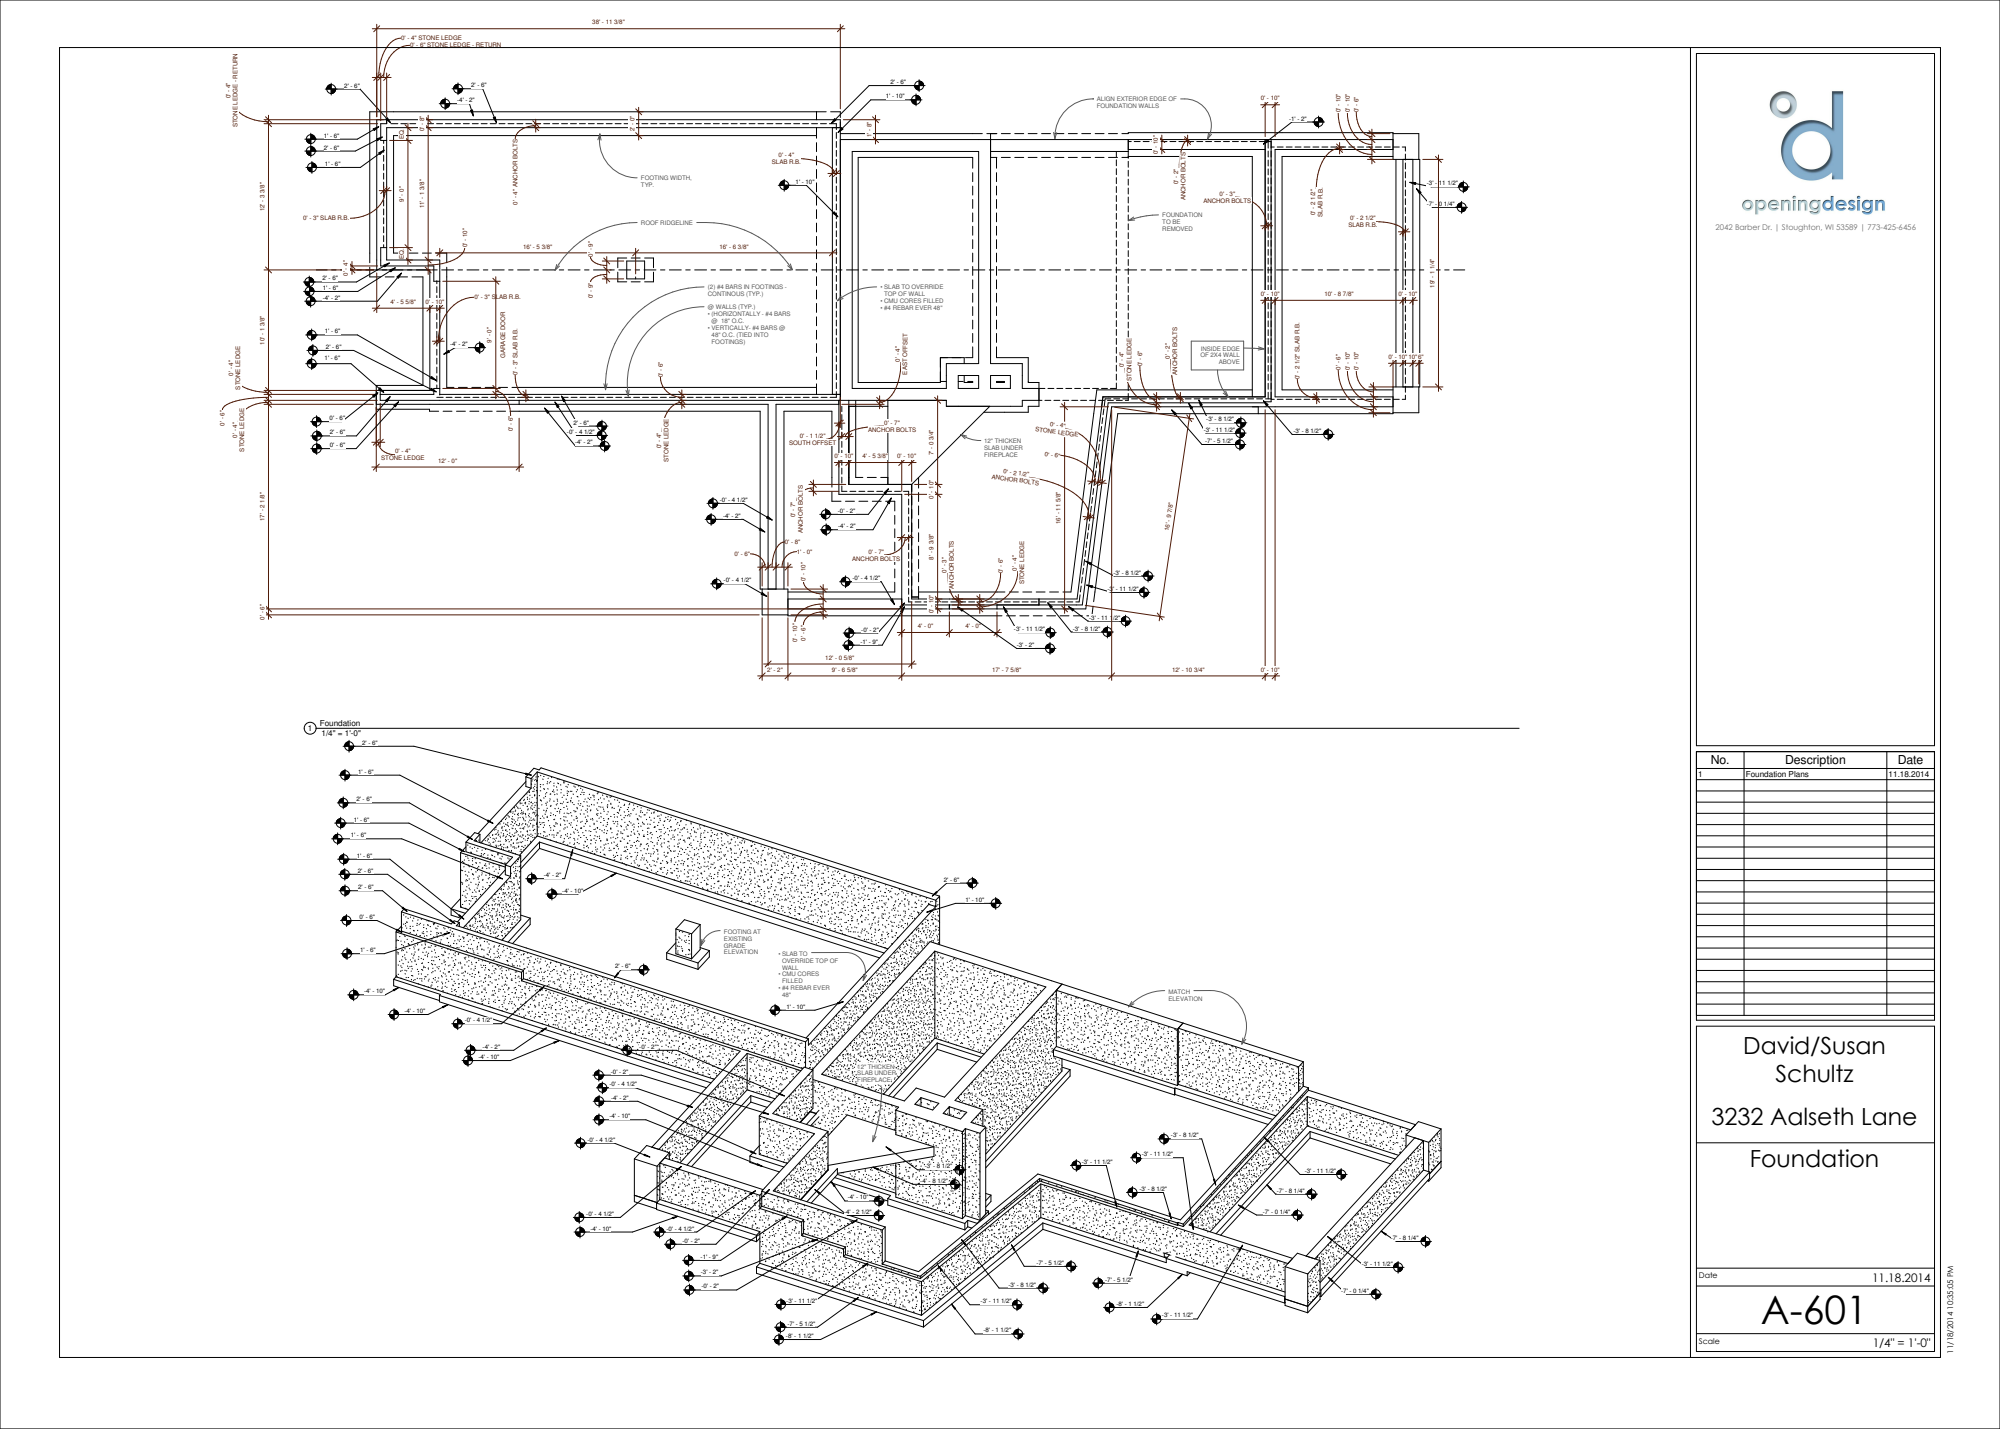
[picture p138: page 1]
@ WALLS (TYP.) • (HORIZONTALLY - #4 BARS @ 18" O.C. • VERTICALLY- #4 BARS @ 48" O.C. (TIED INTO FOOTINGS); SOUTH OFFSET; STONE LEDGE; FOUNDATION TO BE REMOVED; ROOF RIDGELINE; FOOTING WIDTH, TYP.; 0' - 3" SLAB R.B.; ANCHOR BOLTS; INSIDE EDGE OF 2X4 WALL ABOVE; SLAB R.B.; 12" THICKEN SLAB UNDER; FIREPLACE; MATCH ELEVATION; FOOTING AT EXISTING GRADE ELEVATION; 12" THICKEN SLAB UNDER FIREPLACE; Scale; Date; Foundation; David/Susan Schultz; 3232 Aalseth Lane; 1/4" = 1'-0" 1 Foundation; Description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

0' - 4" STONE LEDGE
0' - 6" STONE LEDGE - RETURN

STONE LEDGE - RETURN

ALIGN EXTERIOR EDGE OF
FOUNDATION WALLS

(2) #4 BARS IN FOOTINGS -
CONTINOUS (TYP.)

• SLAB TO OVERRIDE
TOP OF WALL
• CMU CORES FILLED
• #4 REBAR EVER 48"

• SLAB TO
OVERRIDE TOP OF
WALL
• CMU CORES
FILLED
• #4 REBAR EVER
