OpeningDesign/Lake_Kegonsa_Home/Out/20141105 - foundation plans/20141105 - Kegonsa - Foundation Plan.pdf

### 2042 Barber Dr. | Stoughton, WI 53589 | 773-425-6456

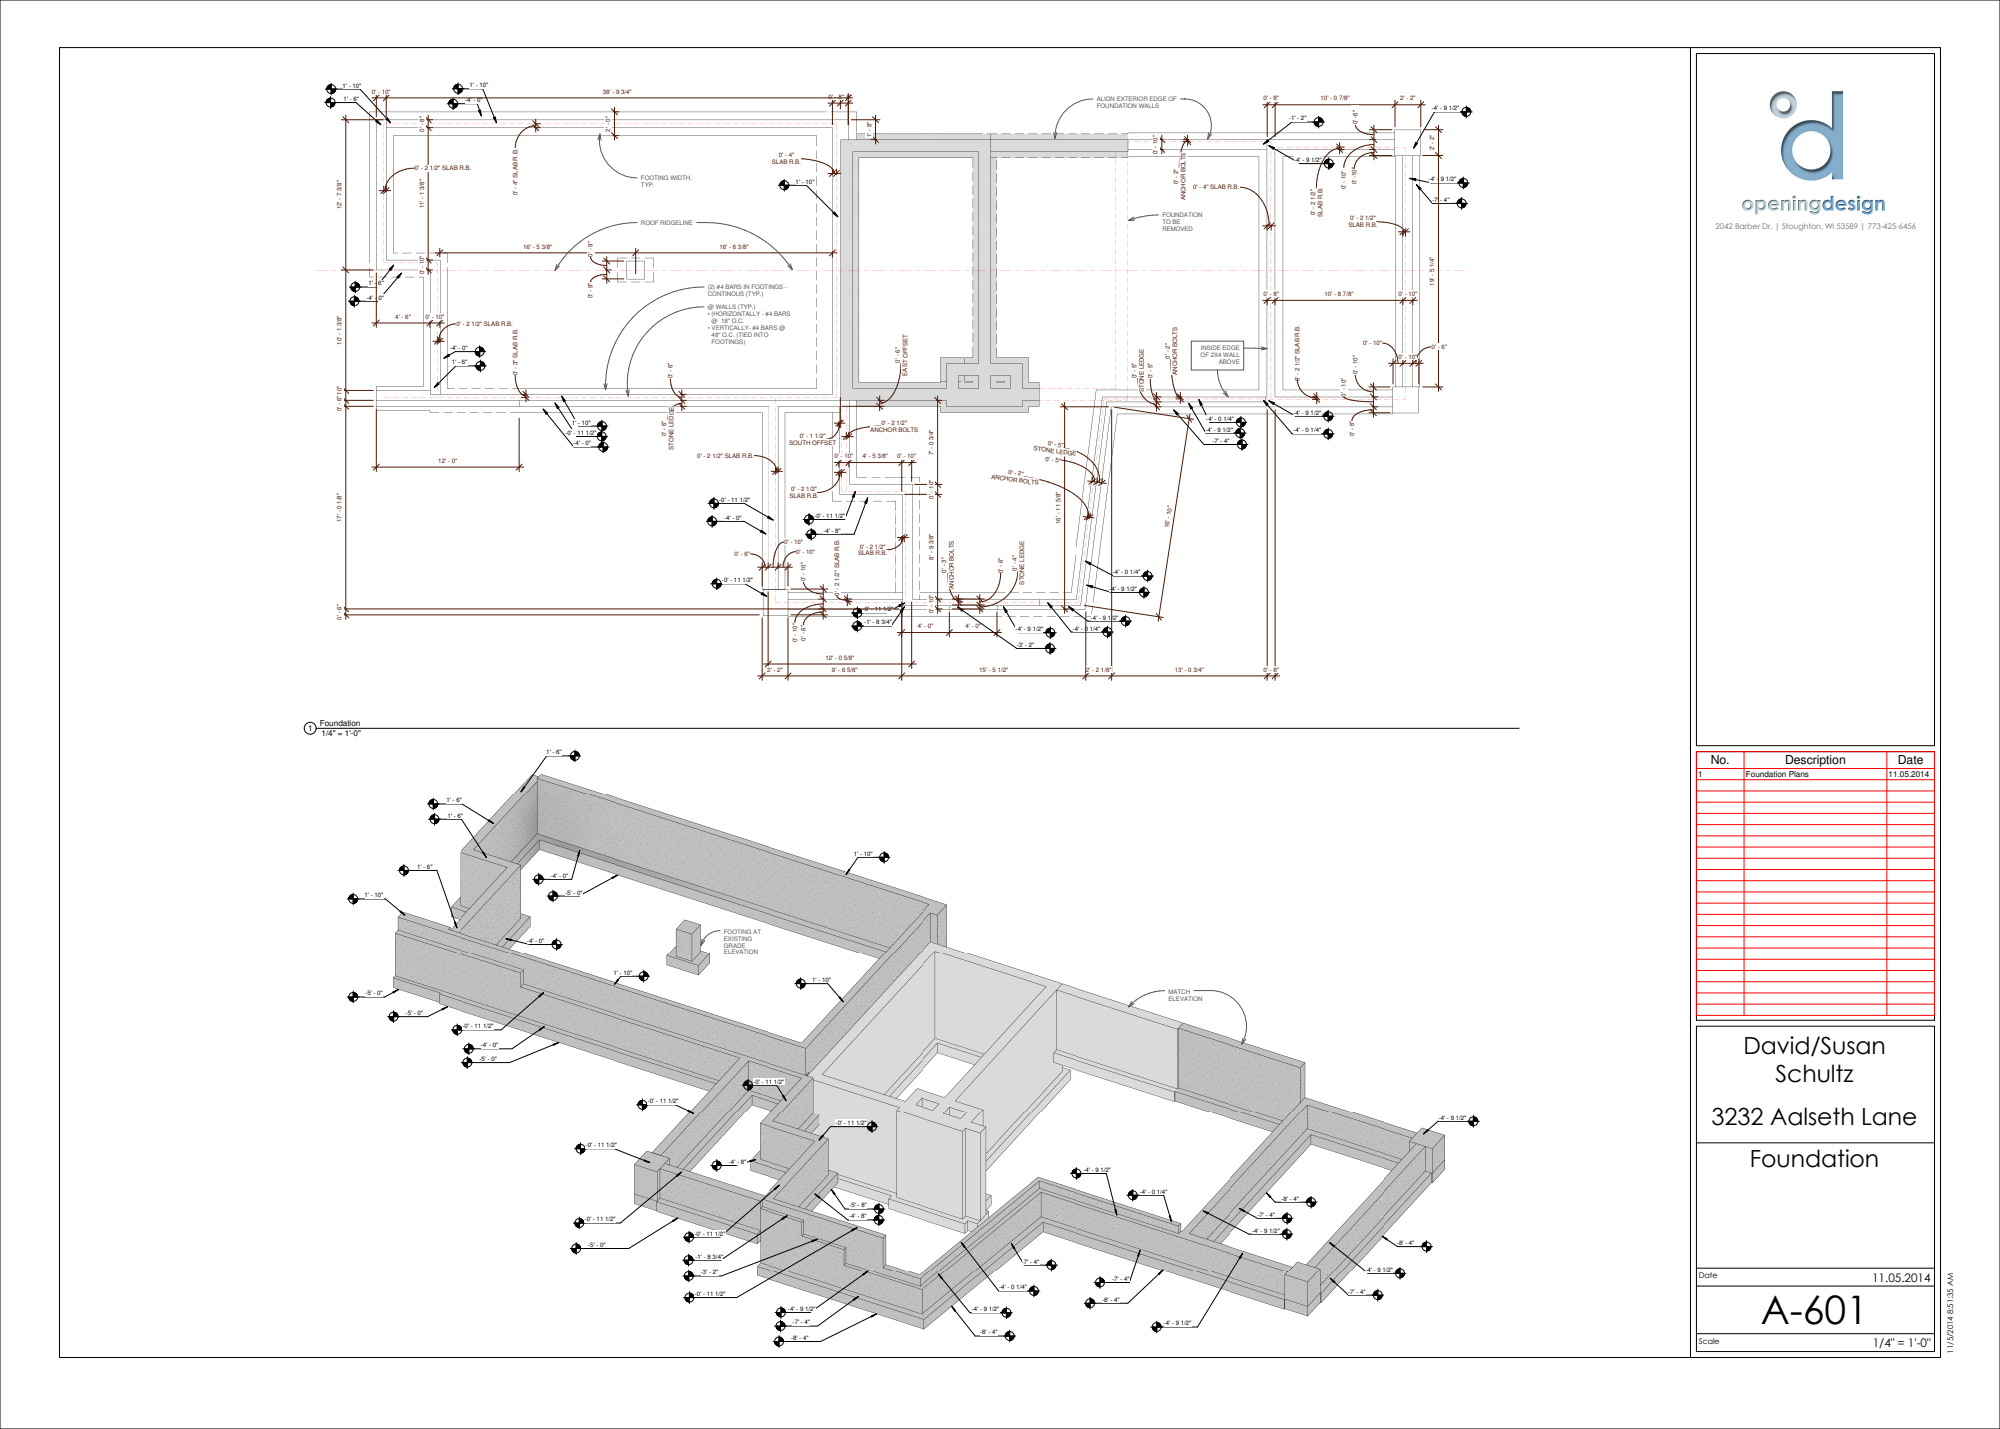
[picture p139: page 1]
@ WALLS (TYP.) • (HORIZONTALLY - #4 BARS @ 18" O.C. • VERTICALLY- #4 BARS @ 48" O.C. (TIED INTO FOOTINGS); SOUTH OFFSET; STONE LEDGE; FOUNDATION TO BE REMOVED; ROOF RIDGELINE; FOOTING WIDTH, TYP.; 0' - 2 1/2" SLAB R.B.; SLAB R.B.; ANCHOR BOLTS; ANCHOR BOLTS 0' - 2"; 0' - 4" SLAB R.B.; INSIDE EDGE OF 2X4 WALL ABOVE; MATCH ELEVATION; FOOTING AT EXISTING GRADE ELEVATION; Scale; Date; Foundation; David/Susan Schultz; 3232 Aalseth Lane; 1/4" = 1'-0" 1 Foundation

ALIGN EXTERIOR EDGE OF
FOUNDATION WALLS

(2) #4 BARS IN FOOTINGS -
CONTINOUS (TYP.)

No. | Description | Date

1 | Foundation Plans | 11.05.2014
