OpeningDesign/Lake_Kegonsa_Home/Out/20141031 - foundation plan/20141031 - Kegonsa - Foundation Plan.pdf

### 2042 Barber Dr. | Stoughton, WI 53589 | 773-425-6456

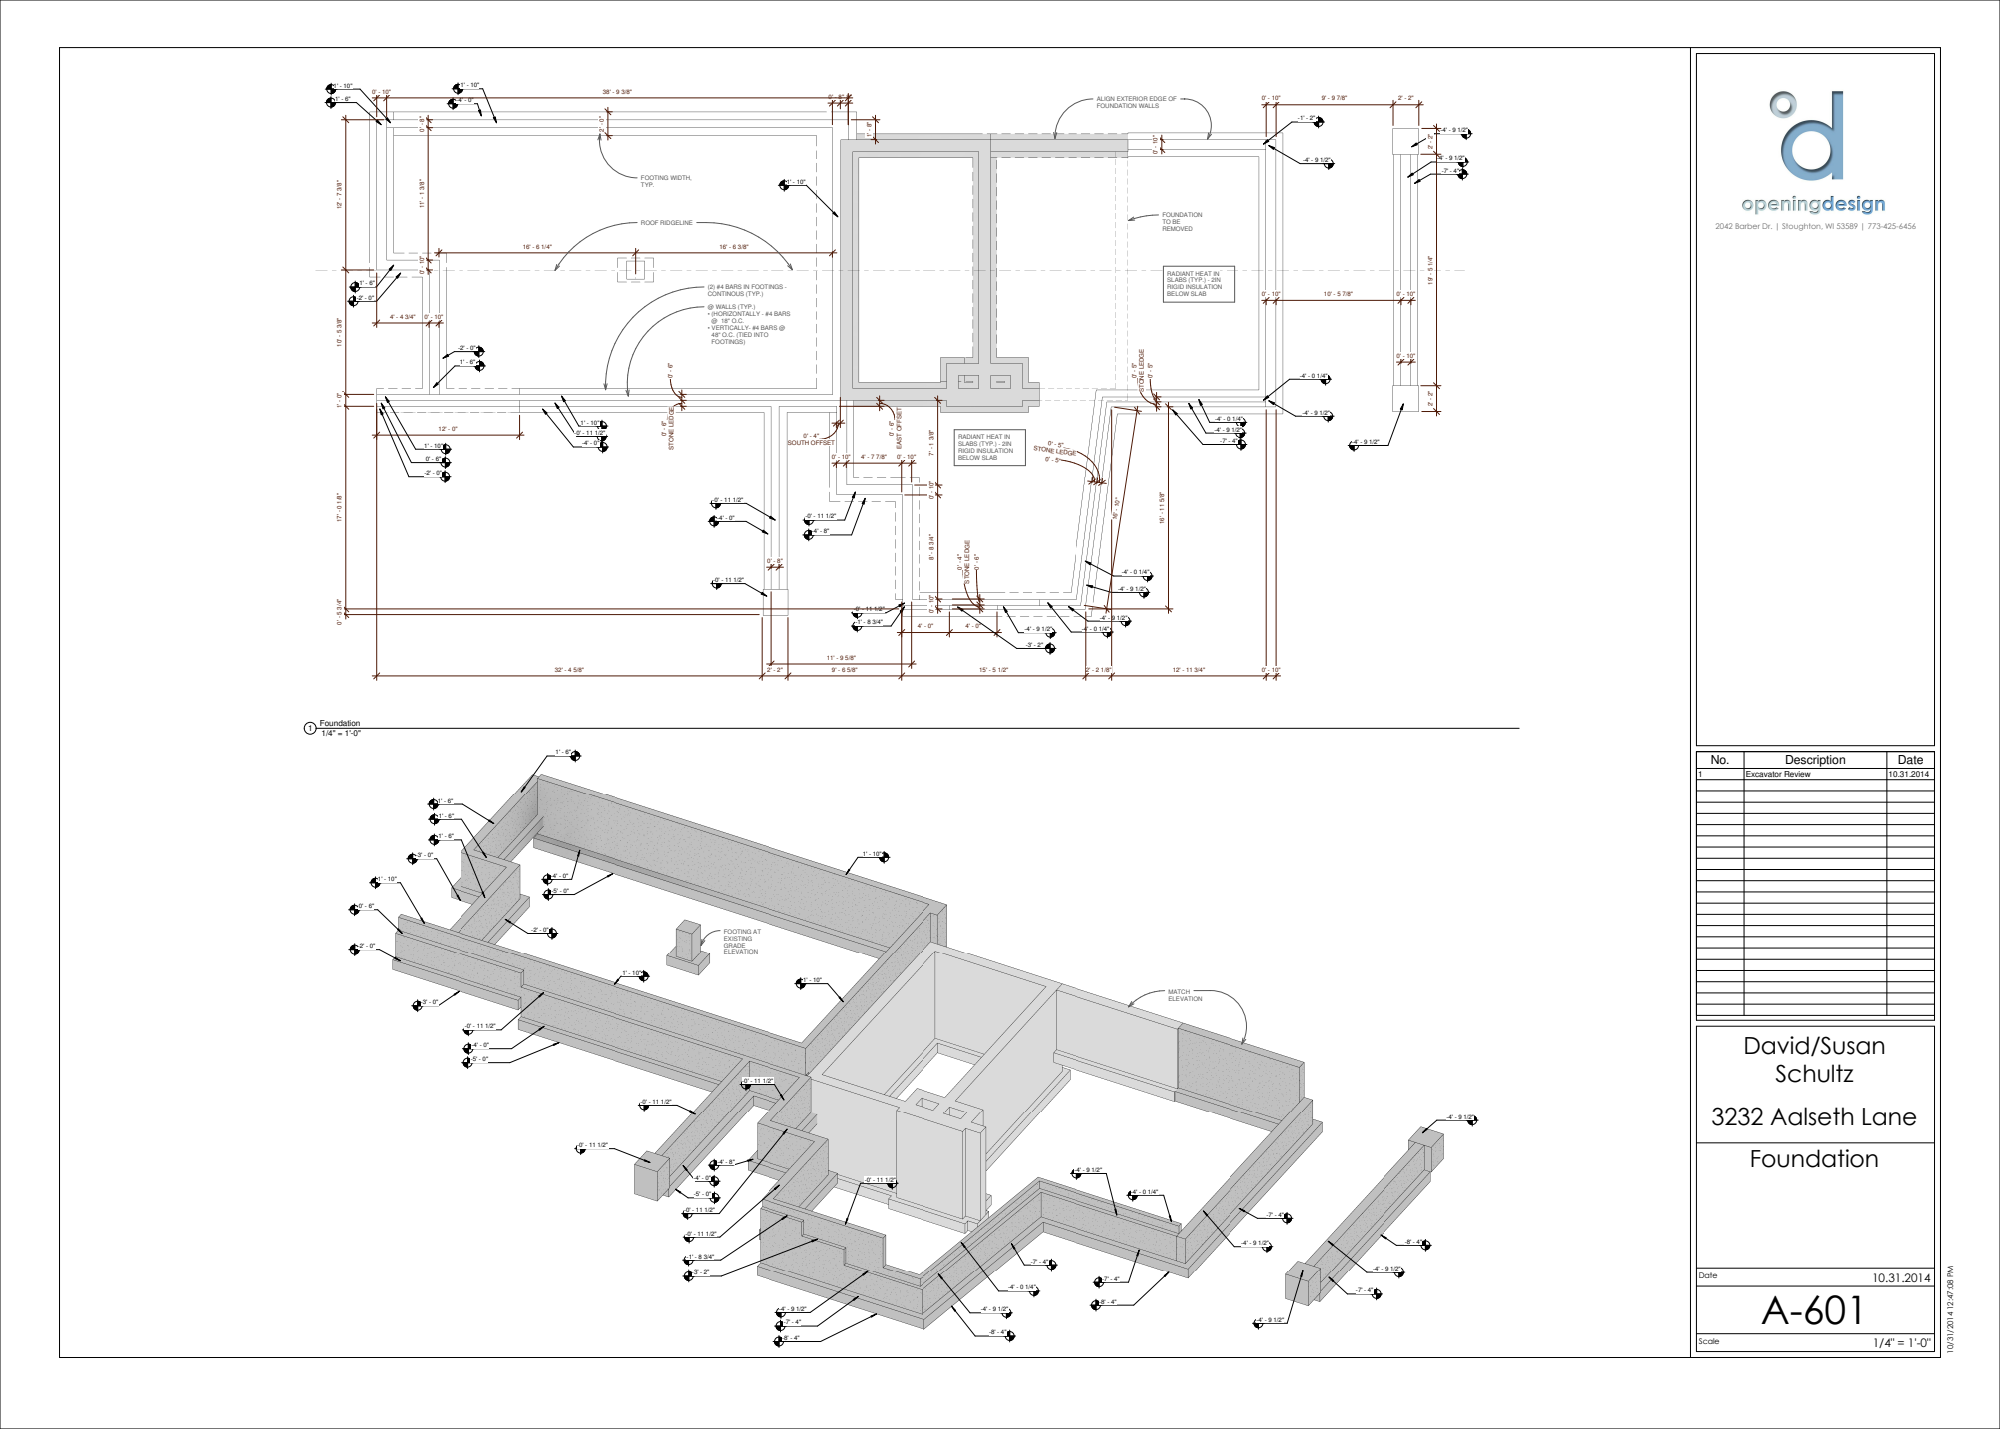
[picture p140: page 1]
@ WALLS (TYP.) • (HORIZONTALLY - #4 BARS @ 18" O.C. • VERTICALLY- #4 BARS @ 48" O.C. (TIED INTO FOOTINGS); SOUTH OFFSET; STONE LEDGE; FOUNDATION TO BE REMOVED; ROOF RIDGELINE; FOOTING WIDTH, TYP.; MATCH ELEVATION; FOOTING AT EXISTING GRADE ELEVATION; Scale; Date; Foundation; David/Susan Schultz; 3232 Aalseth Lane; 1/4" = 1'-0" 1 Foundation

ALIGN EXTERIOR EDGE OF
FOUNDATION WALLS

RADIANT HEAT IN
SLABS (TYP.) - 2IN
RIGID INSULATION
BELOW SLAB

(2) #4 BARS IN FOOTINGS -
CONTINOUS (TYP.)

No. | Description | Date

1 | Excavator Review | 10.31.2014
