OpeningDesign/Lake_Kegonsa_Home/Transfer/3232 Aalseth_Structure_20141211_°d.pdf

D H

2

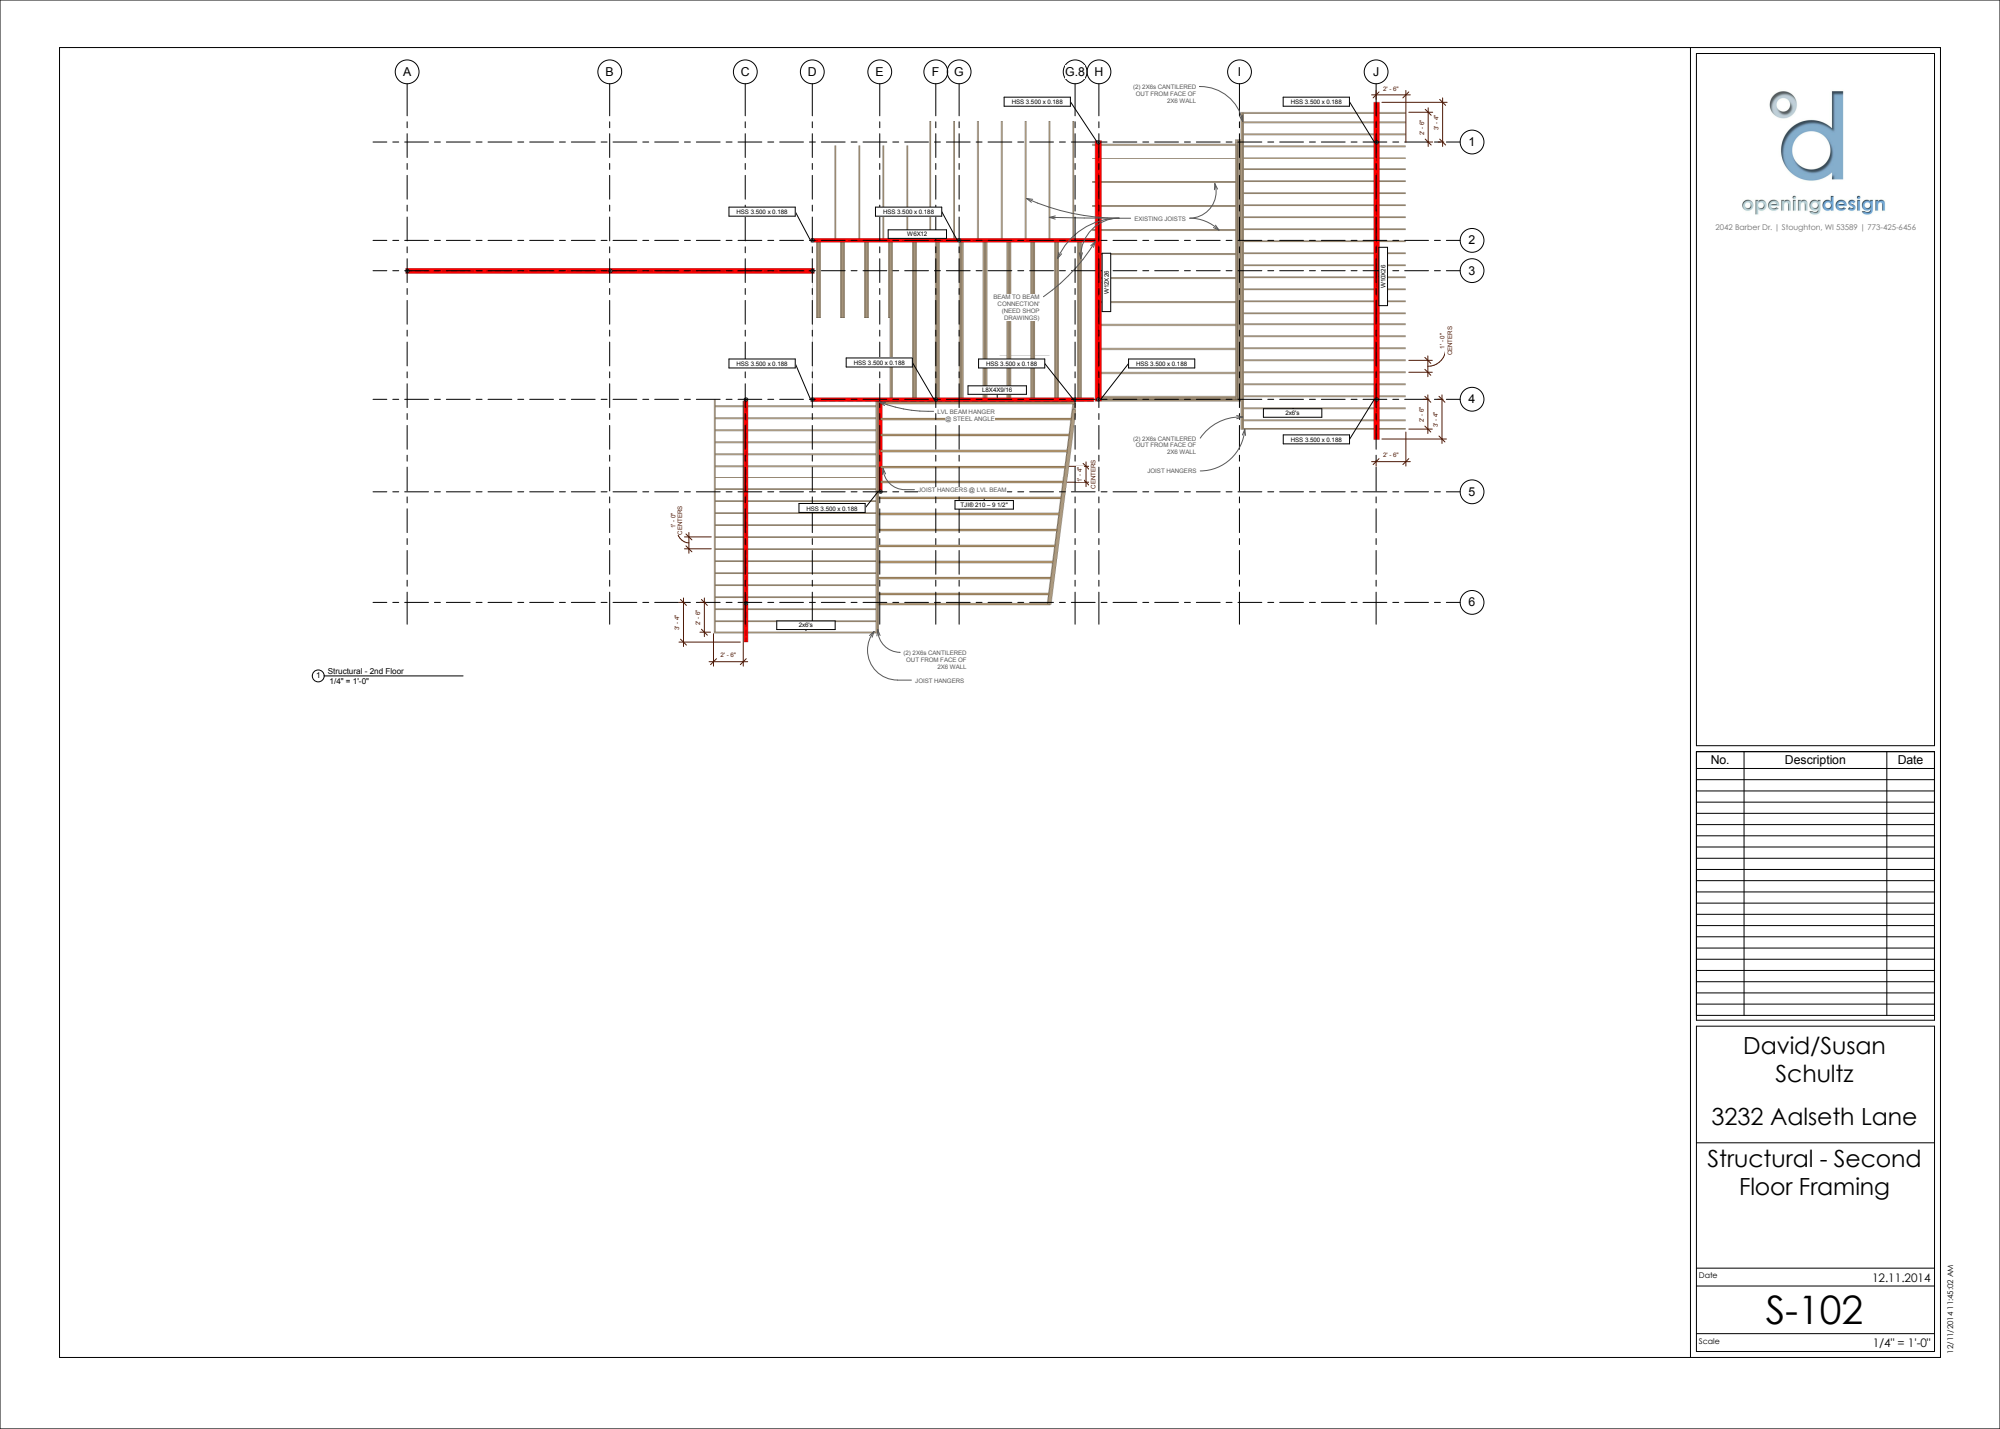
[picture p145: page 1]
HSS 3.500 x 0.188; TJI® 210 – 9 1/2"; 2X6 WALL; JOIST HANGERS; EXISTING JOISTS; Scale; Date; Structural - Second Floor Framing; David/Susan Schultz; 3232 Aalseth Lane; Description; Structural - 2nd Floor

(2) 2X6s CANTILERED
OUT FROM FACE OF

2042 Barber Dr. | Stoughton, WI 53589 | 773-425-6456

BEAM TO BEAM
CONNECTION'
(NEED SHOP
DRAWINGS)

LVL BEAM HANGER
@ STEEL ANGLE

JOIST HANGERS @ LVL BEAM
