OpeningDesign/Lake_Kegonsa_Home/Transfer/20170724 - from Paulson - Erosin Control/14-137 EC PLAN 6-20-17.pdf

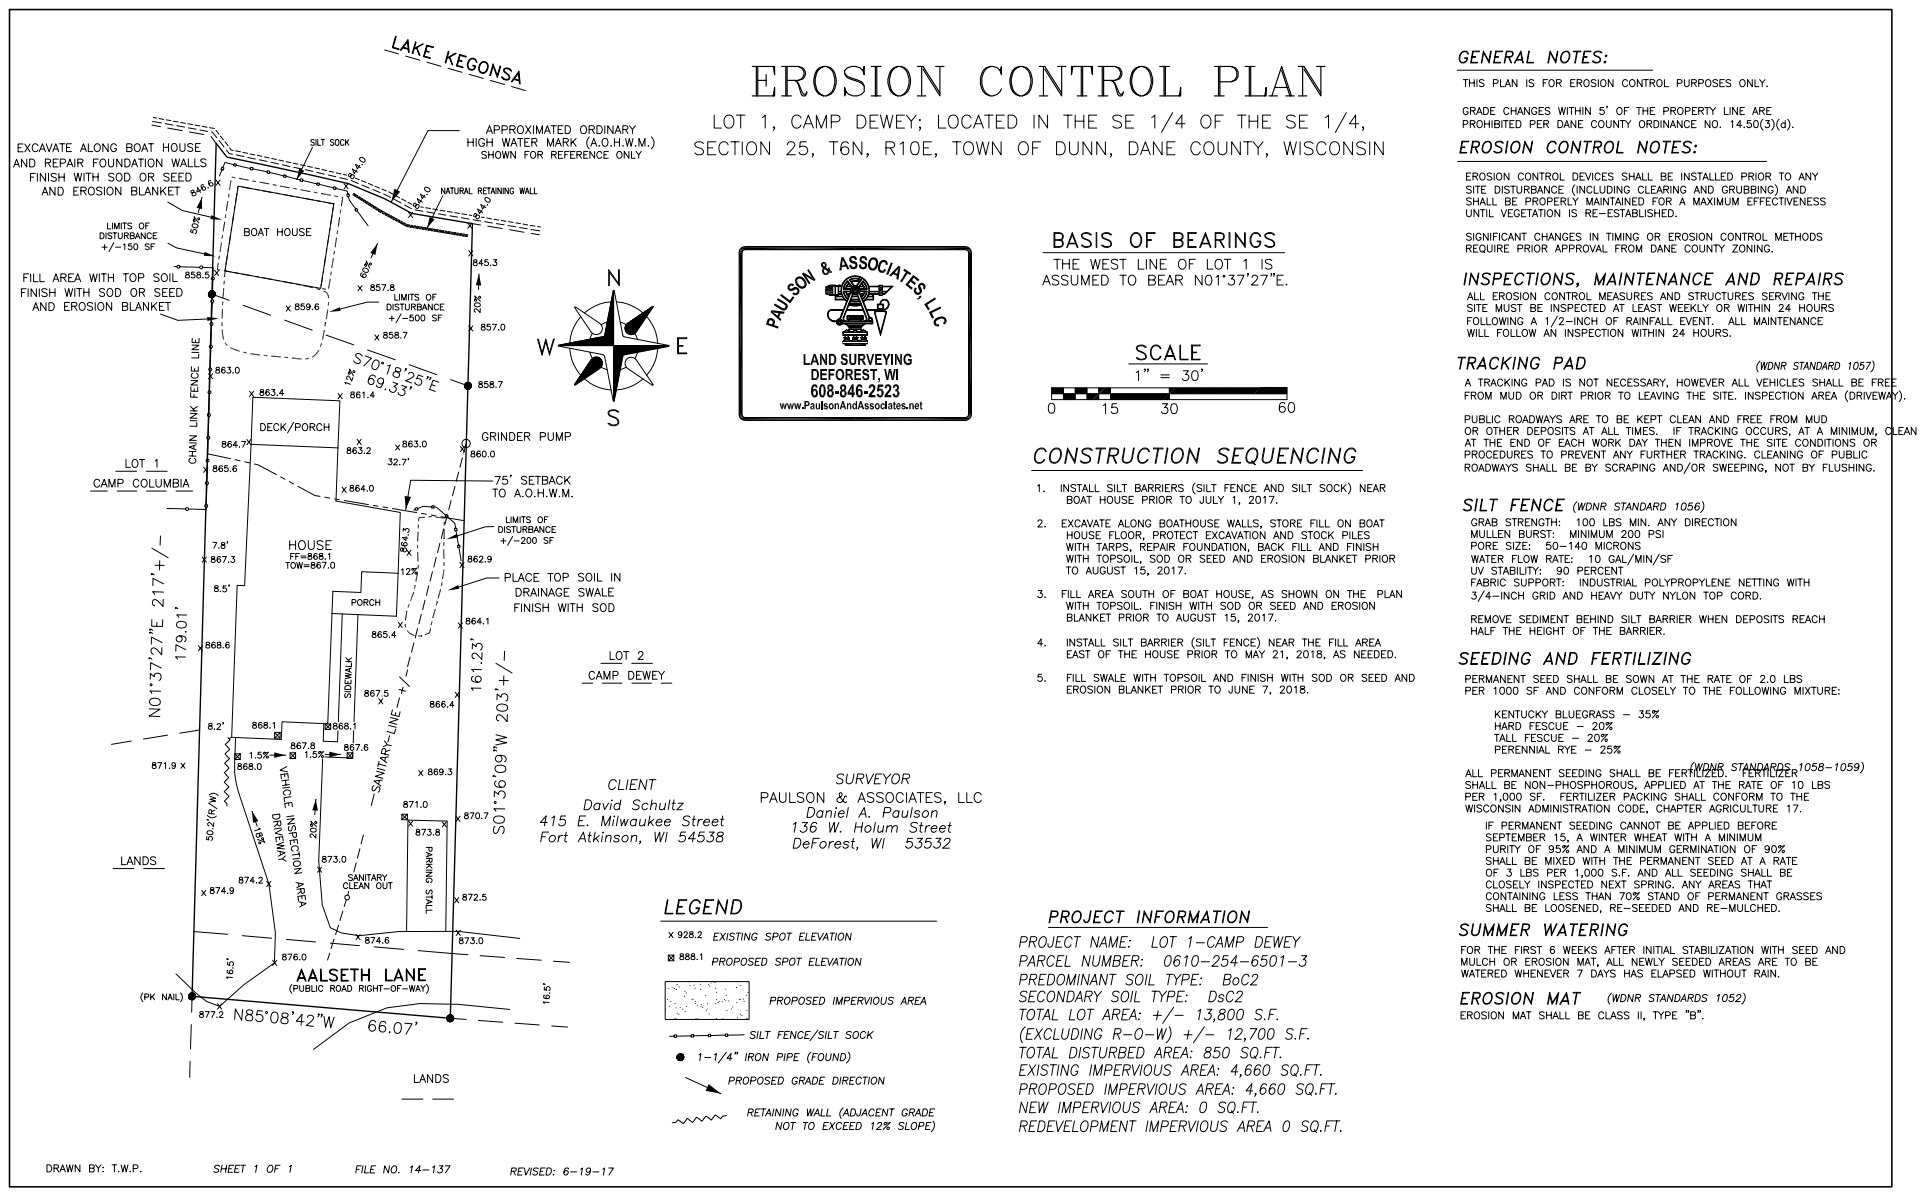
[picture p146: page 1]
