OpeningDesign/Lake_Kegonsa_Home/Transfer/20150730 - fireplace to decorator/20150730 - Lake_Kegonsa - fireplace.pdf

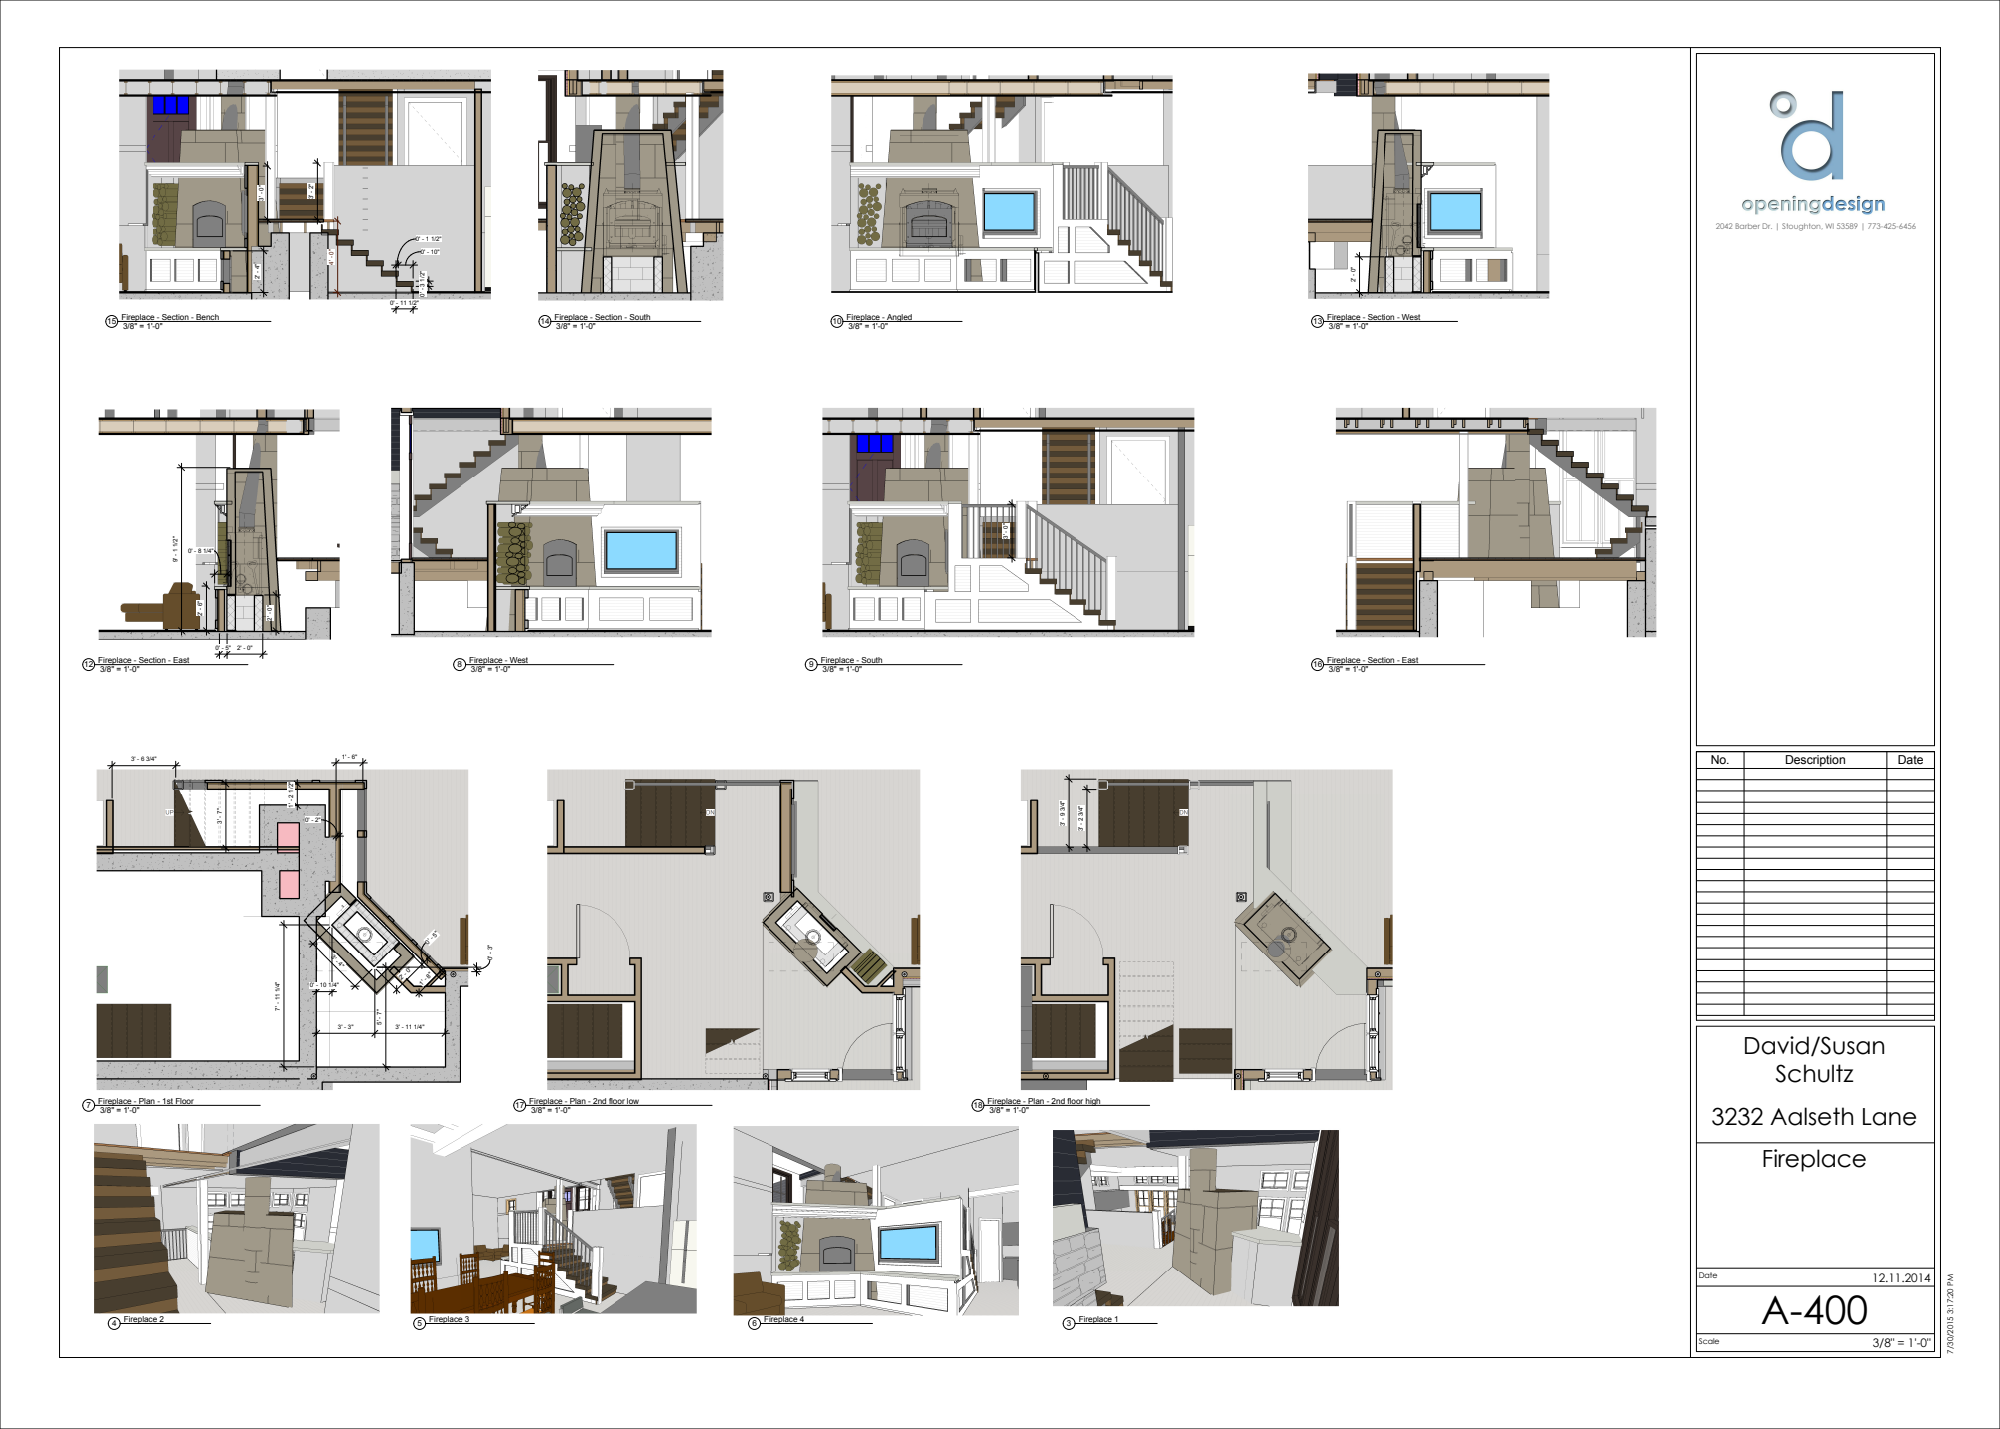
[picture p147: page 1]
Scale; Date; Fireplace; David/Susan Schultz; 3232 Aalseth Lane; Description; 3 Fireplace 1 4 Fireplace 2; 5 Fireplace 3; 6 Fireplace 4; 3/8" = 1'-0" 8 Fireplace - West; 3/8" = 1'-0" 9 Fireplace - South; 3/8" = 1'-0" 10 Fireplace - Angled; 3/8" = 1'-0" 17 Fireplace - Plan - 2nd floor low; 3/8" = 1'-0" 18 Fireplace - Plan - 2nd floor high

2042 Barber Dr. | Stoughton, WI 53589 | 773-425-6456

3/8" = 1'-0" 13 Fireplace - Section - West 3/8" = 1'-0" 14 Fireplace - Section - South 3/8" = 1'-0" 15 Fireplace - Section - Bench

3/8" = 1'-0" 12 Fireplace - Section - East

3/8" = 1'-0" 16 Fireplace - Section - East

3/8" = 1'-0" 7 Fireplace - Plan - 1st Floor
