OpeningDesign/Lake_Kegonsa_Home/Transfer/20150309 - structural offset/20150309 - structural offset at garage.pdf

D H

B J

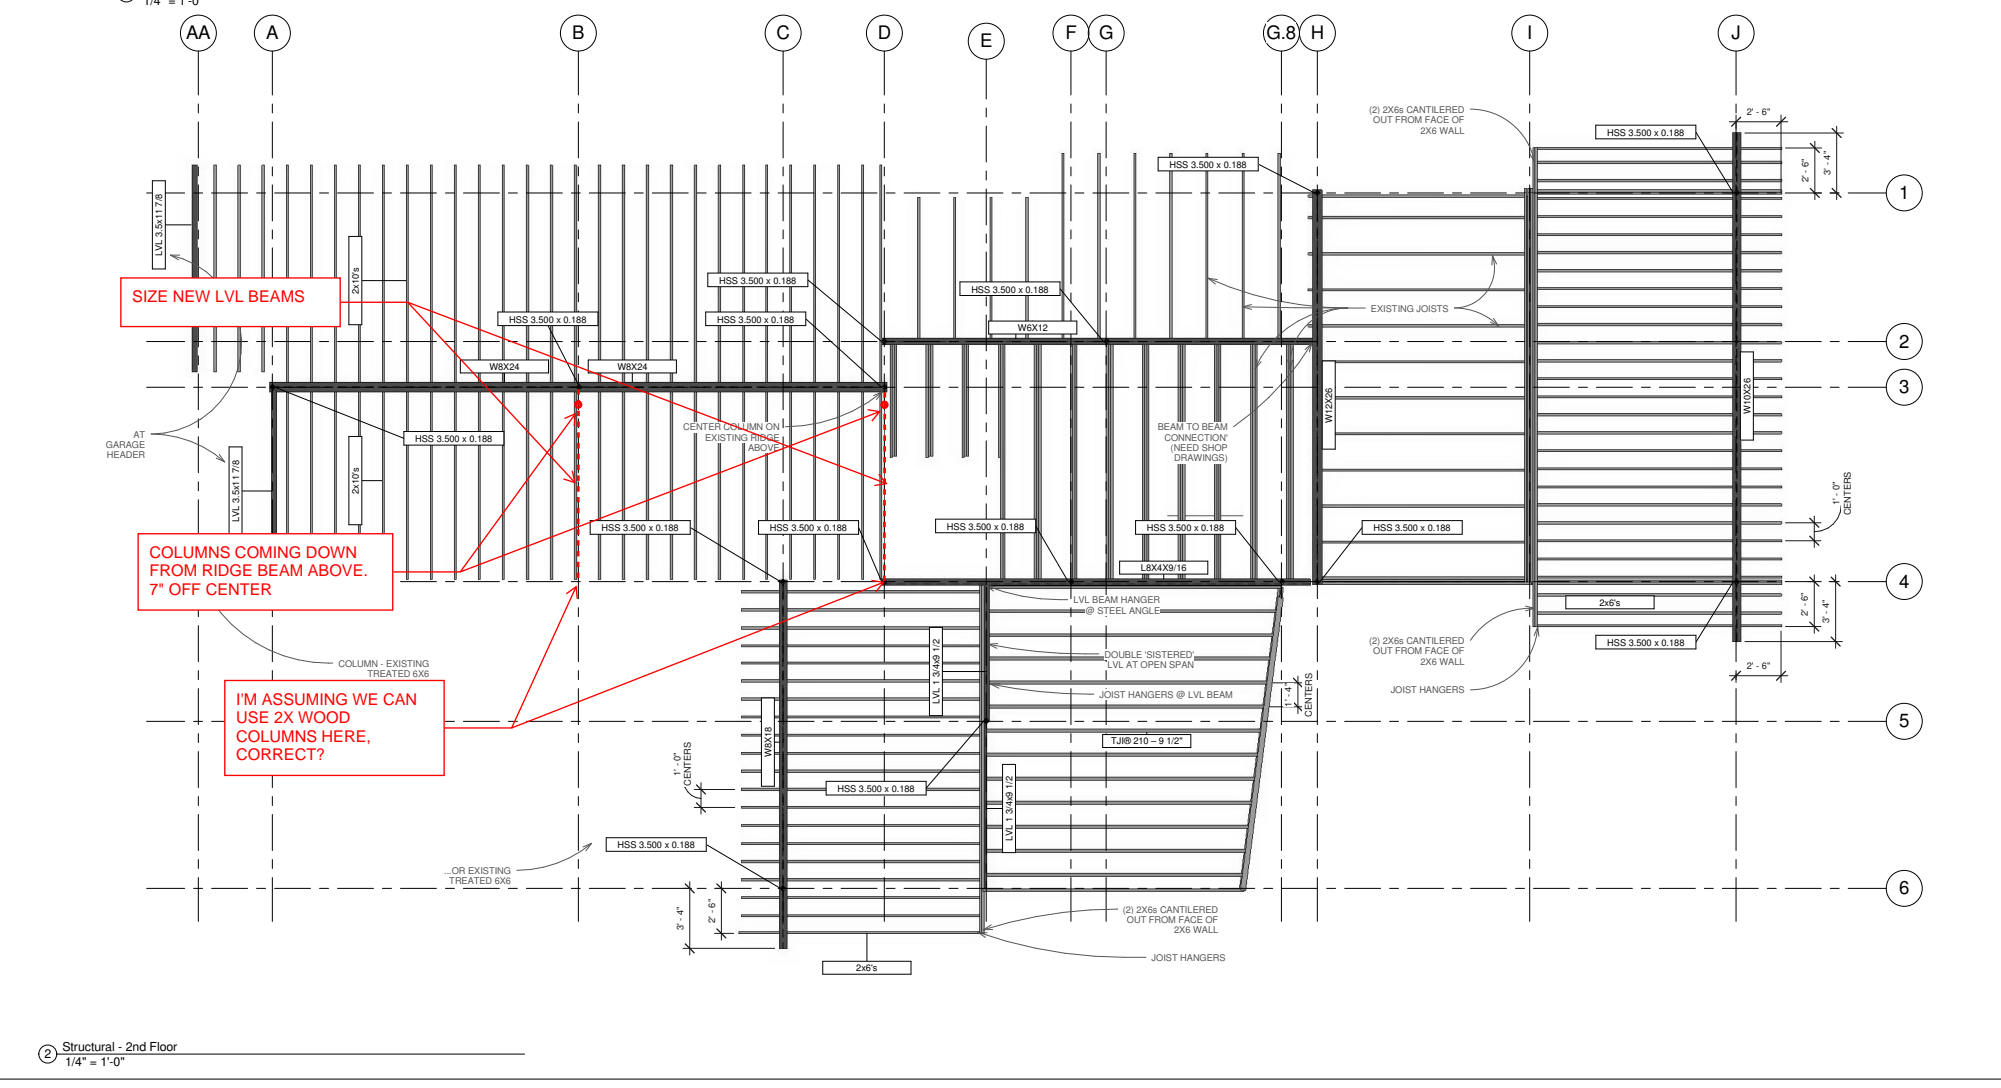
[picture p148: page 1]
HSS 3.500 x 0.188; 2' - 6" 2' - 6" CENTERS 1' - 0" 2x6's; TJI® 210 – 9 1/2"; 2X6 WALL; JOIST HANGERS; EXISTING JOISTS; "(2) 2X6s CANTILERED; ABOVE; COLUMN - EXISTING TREATED 6X6; ...OR EXISTING TREATED 6X6; AT GARAGE HEADER; 1/4" = 1'-0" 1 Structural - Basement; 1/4" = 1'-0" 2 Structural - 2nd Floor

(2) 2X6s CANTILERED
OUT FROM FACE OF

CENTER COLUMN ON
EXISTING RIDGE

BEAM TO BEAM
CONNECTION'
(NEED SHOP
DRAWINGS)

LVL BEAM HANGER
@ STEEL ANGLE

DOUBLE 'SISTERED'
LVL AT OPEN SPAN

JOIST HANGERS @ LVL BEAM
