OpeningDesign/Lake_Kegonsa_Home/Transfer/20150129 - Full Set/Lake_Kegonsa_Home_3 - Sheet_ A-101 - First Floor.pdf

D | H

2

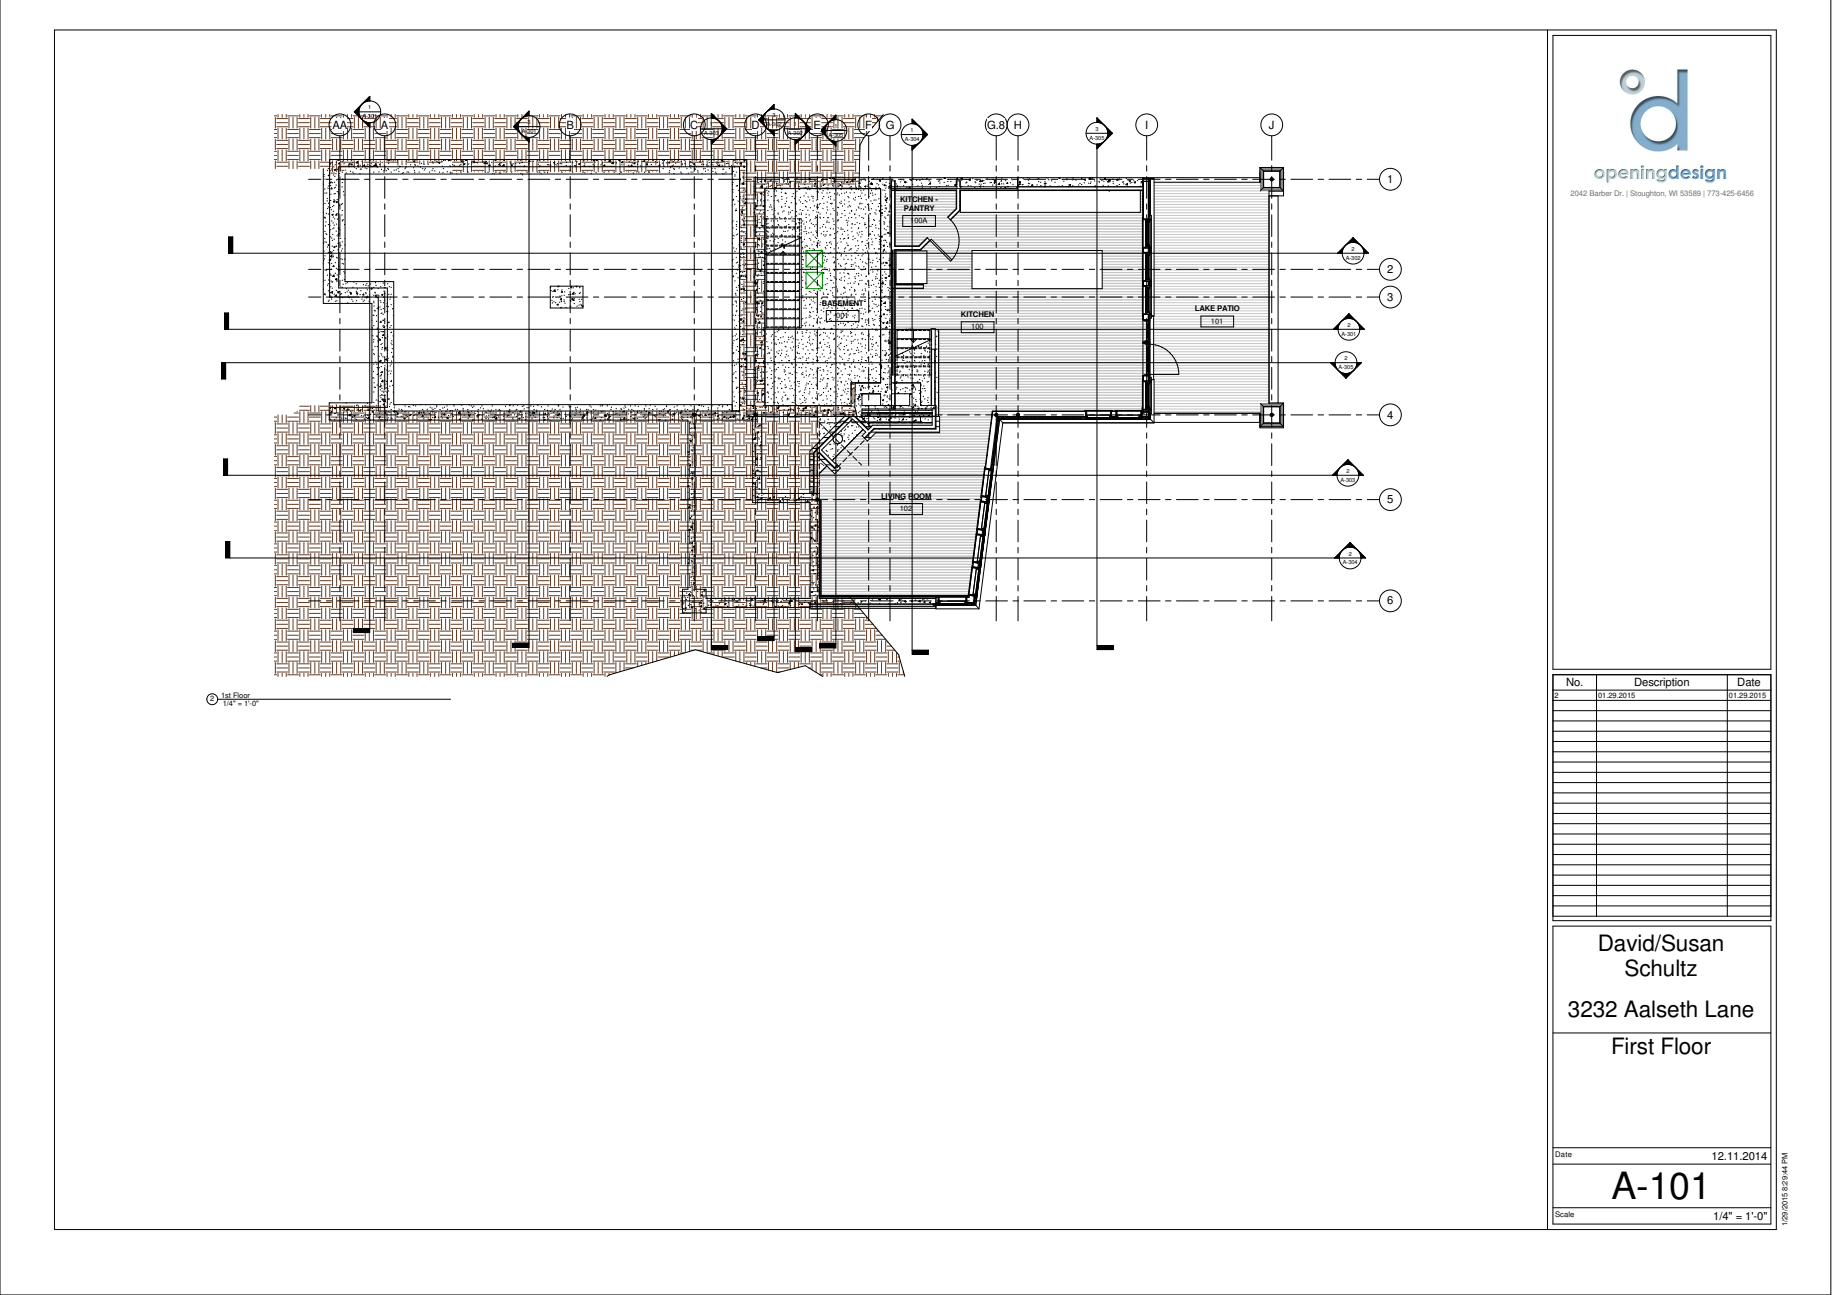
[picture p149: page 1]
KITCHEN; LAKE PATIO; LIVING ROOM; BASEMENT; KITCHEN -; PANTRY; Scale; Date; First Floor; David/Susan Schultz; 3232 Aalseth Lane; 1/4" = 1'-0" 2 1st Floor; Description

2042 Barber Dr. | Stoughton, WI 53589 | 773-425-6456
