OpeningDesign/Lake_Kegonsa_Home/Transfer/20150129 - Full Set/Lake_Kegonsa_Home_3 - Sheet_ A-102 - Second & Third Floor Plan.pdf

D | H

2

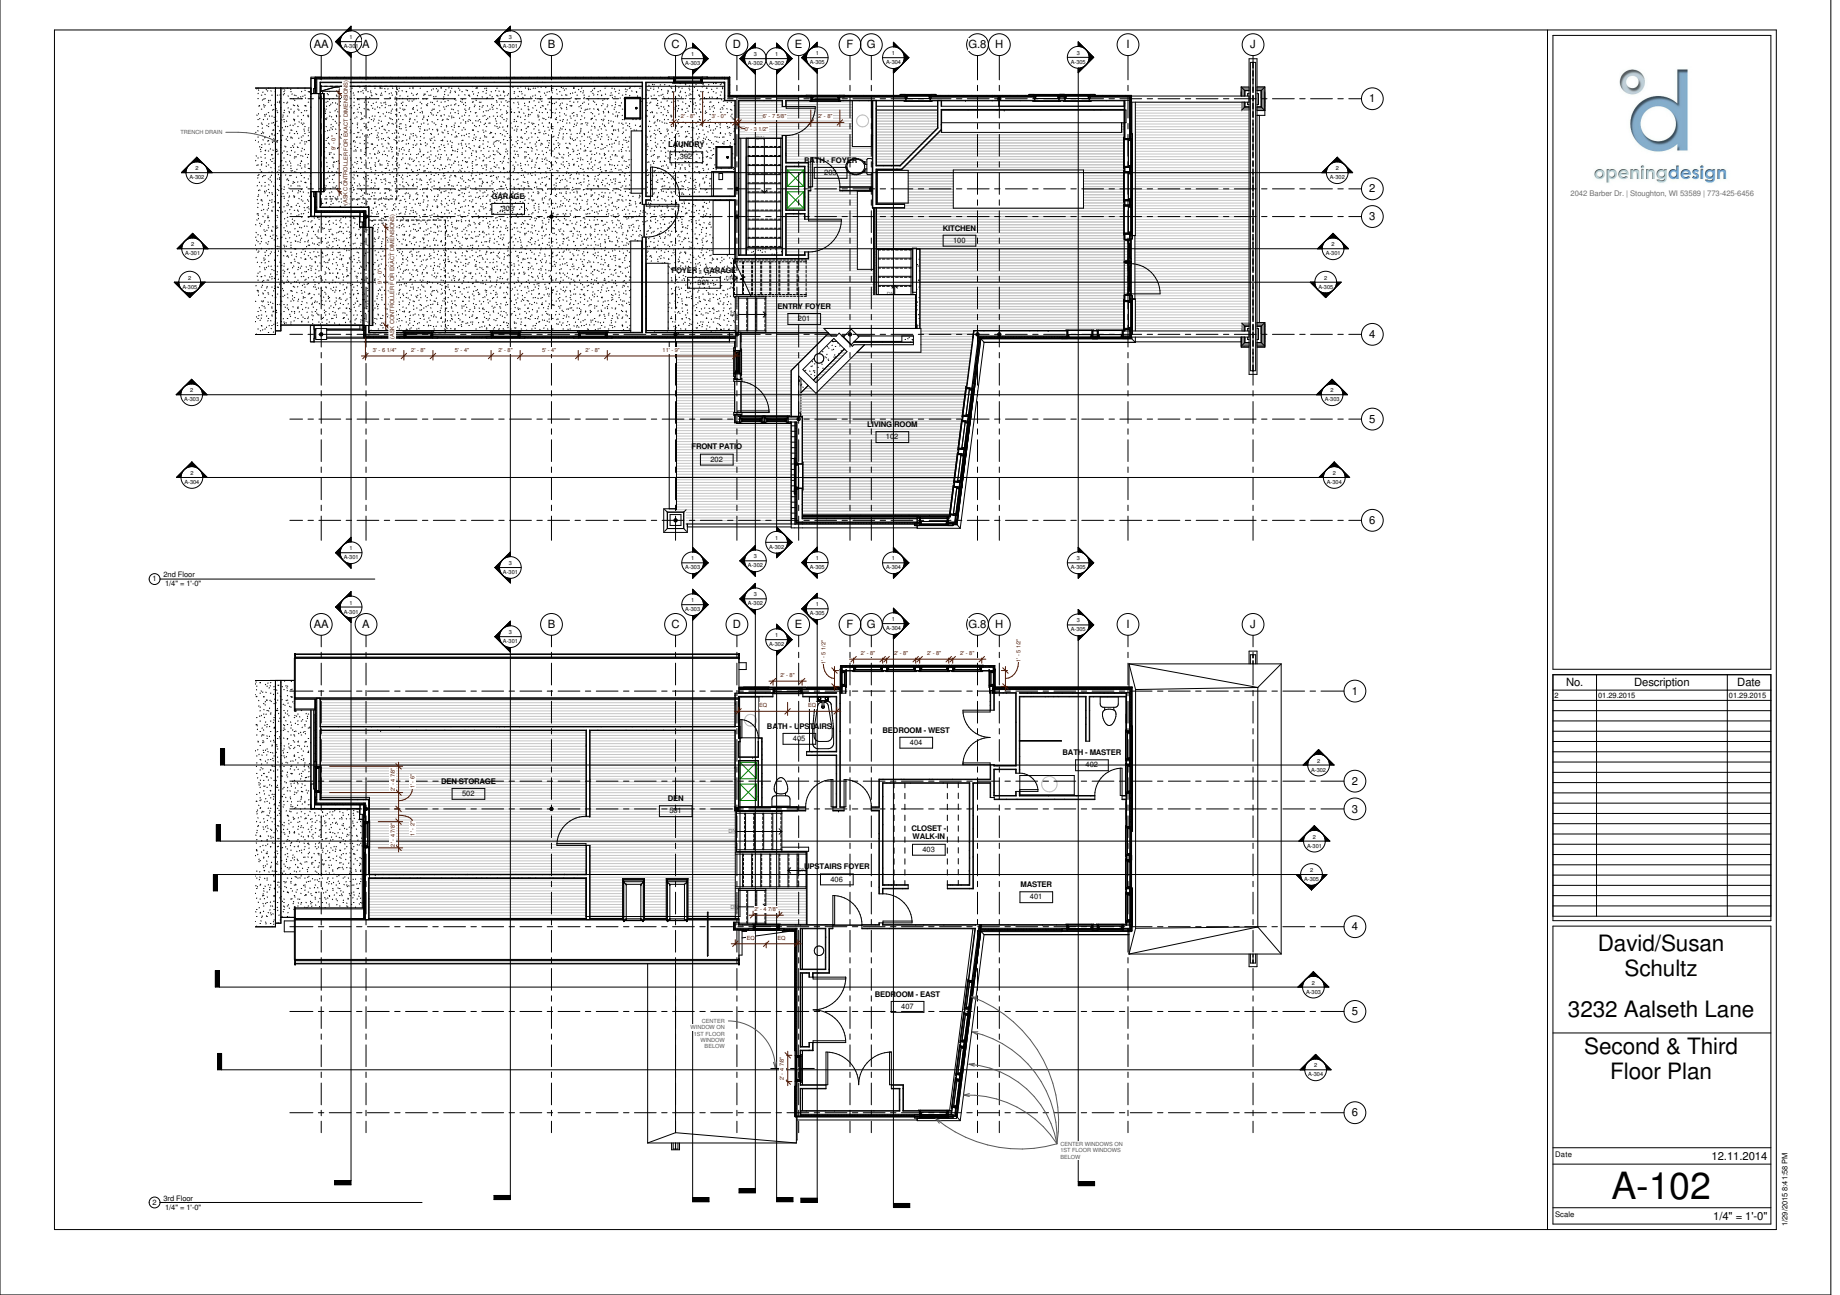
[picture p150: page 1]
BATH - MASTER; BEDROOM - EAST; BEDROOM - WEST; BATH - UPSTAIRS; UPSTAIRS FOYER; MASTER; CLOSET -; WALK-IN; DEN STORAGE; CENTER WINDOW ON 1ST FLOOR WINDOW BELOW; TRENCH DRAIN; KITCHEN; LIVING ROOM; ENTRY FOYER; FRONT PATIO; BATH - FOYER; FOYER - GARAGE; LAUNDRY; GARAGE; DIM; SIO; Scale; Date; Second & Third Floor Plan; David/Susan Schultz; 3232 Aalseth Lane; 1/4" = 1'-0" 2 3rd Floor; Description; 1/4" = 1'-0" 1 2nd Floor

2042 Barber Dr. | Stoughton, WI 53589 | 773-425-6456

502 | DEN

CENTER WINDOWS ON
1ST FLOOR WINDOWS
BELOW
