OpeningDesign/Lake_Kegonsa_Home/Transfer/20150129 - Full Set/Lake_Kegonsa_Home_3 - Sheet_ A-103 - Roof Plan.pdf

D | H
B | J

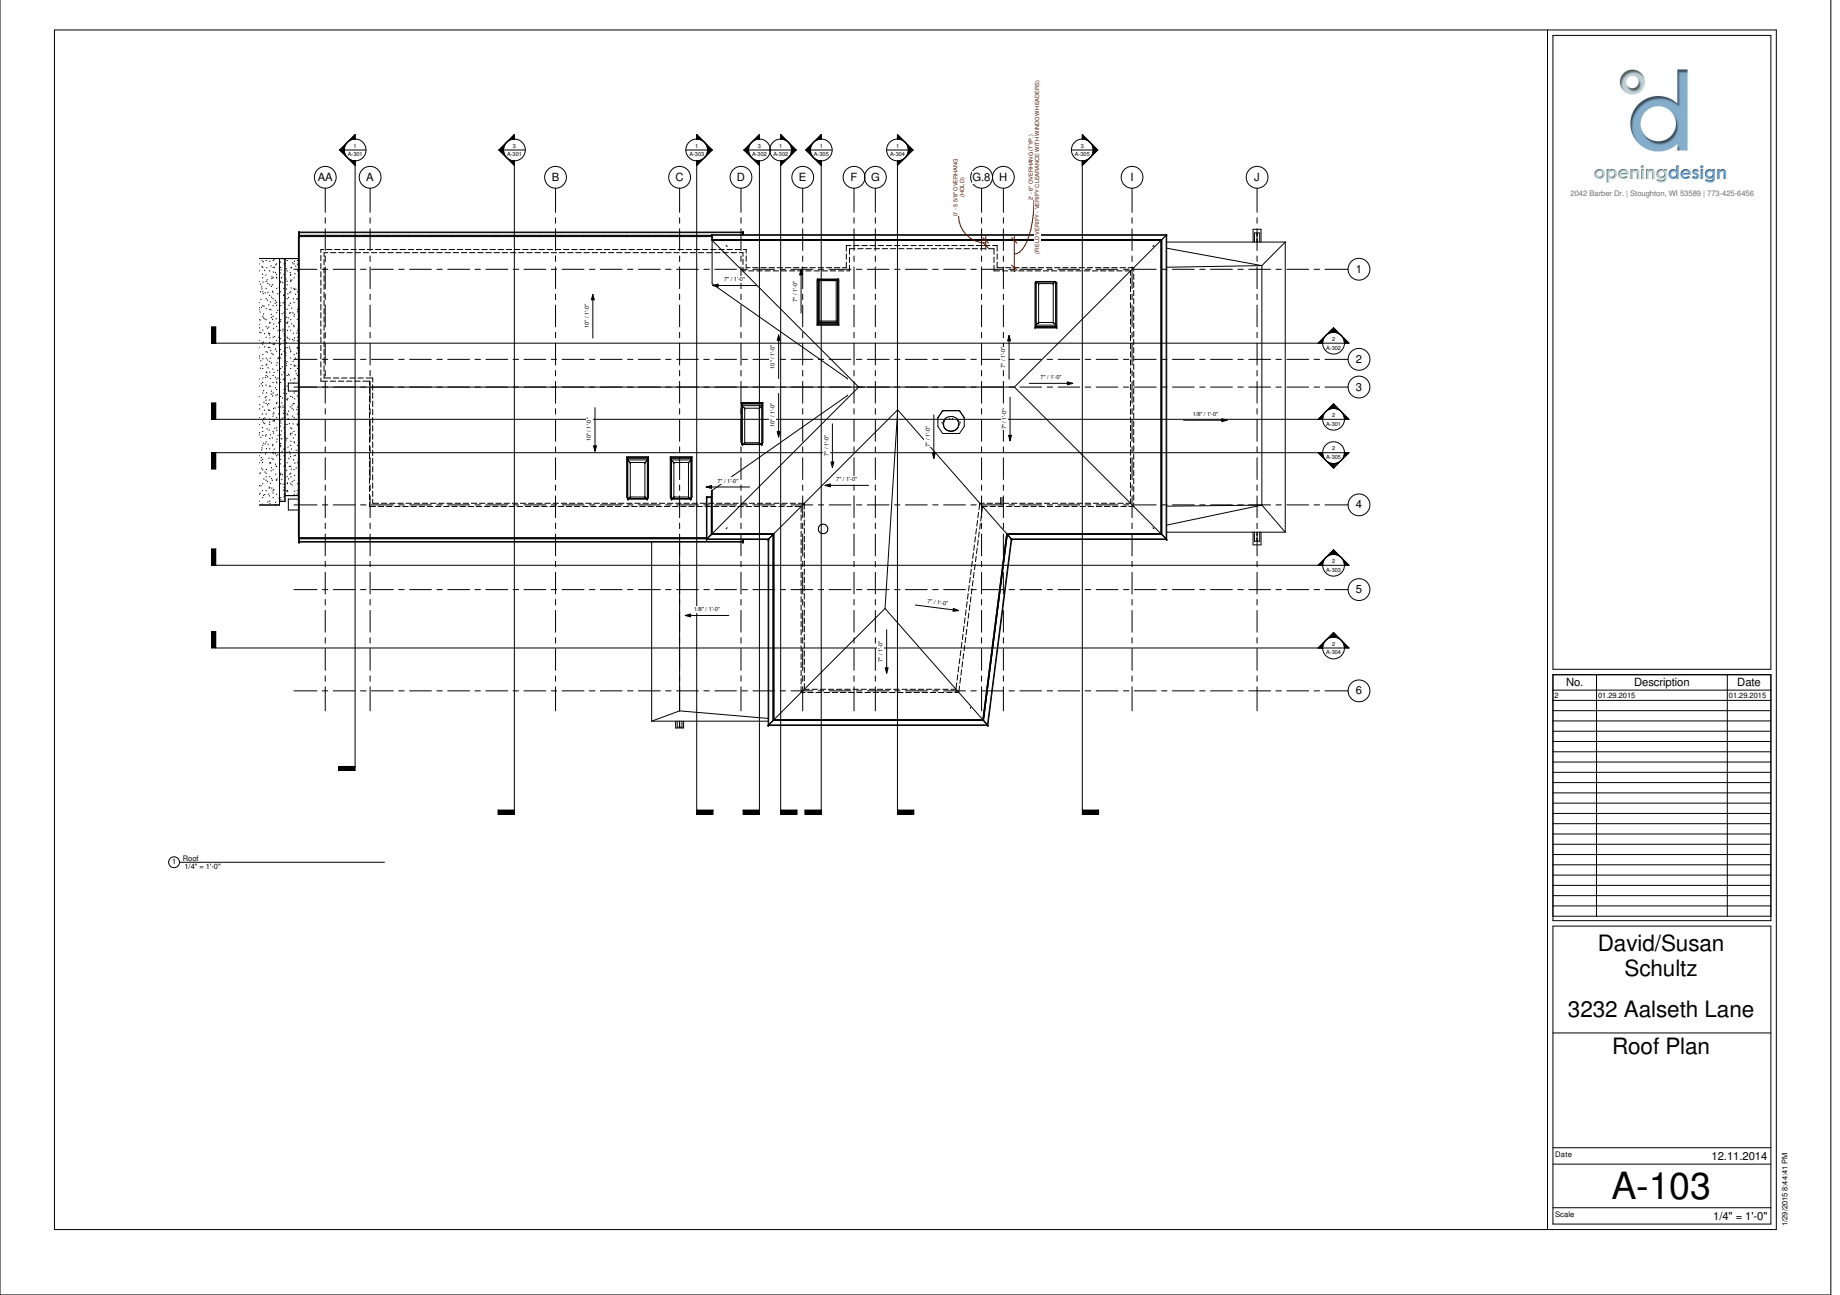
[picture p151: page 1]
2' - 6" OVERHANG (TYP.); (HOLD); 0' - 5 5/8" OVERHANG; Scale; Date; Roof Plan; David/Susan Schultz; 3232 Aalseth Lane; 1 Roof

(FIELD VERIFY - VERIFY CLEARANCE WITH WINDOW HEADERS)

2042 Barber Dr. | Stoughton, WI 53589 | 773-425-6456

No. | Description | Date
