OpeningDesign/Lake_Kegonsa_Home/Transfer/20150129 - Full Set/Lake_Kegonsa_Home_3 - Sheet_ A-201 - Elevations - South & East.pdf

2 | 4
1 | 3 | 5 | 6

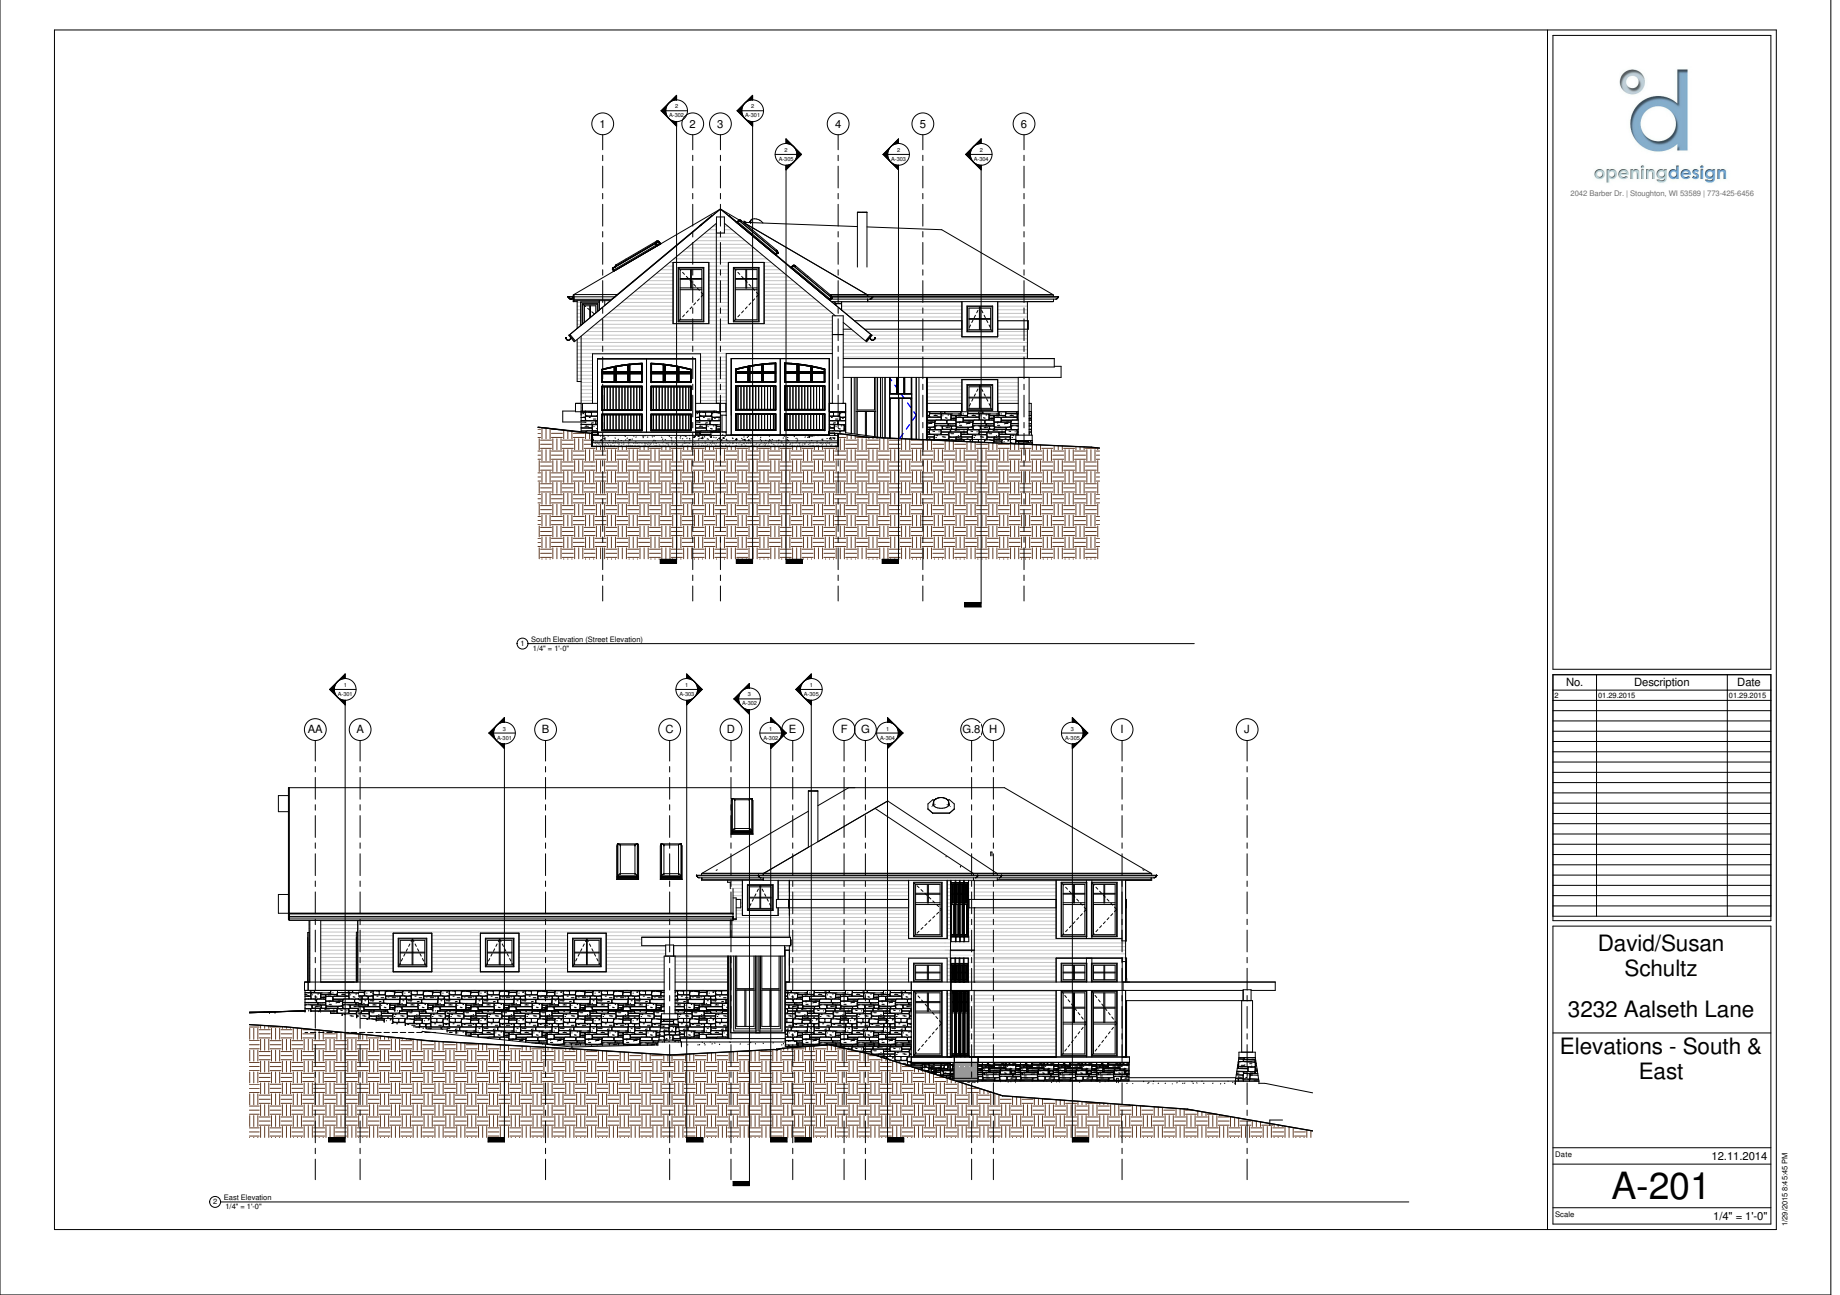
[picture p152: page 1]
Scale; Date; Elevations - South & East; David/Susan Schultz; 3232 Aalseth Lane; 1/4" = 1'-0" 2 East Elevation; Description

2042 Barber Dr. | Stoughton, WI 53589 | 773-425-6456

1/4" = 1'-0" 1 South Elevation (Street Elevation)
