OpeningDesign/Lake_Kegonsa_Home/Transfer/20150129 - Full Set/Lake_Kegonsa_Home_3 - Sheet_ A-202 - Elevations - North & West.pdf

6 | 5 | 3 | 1

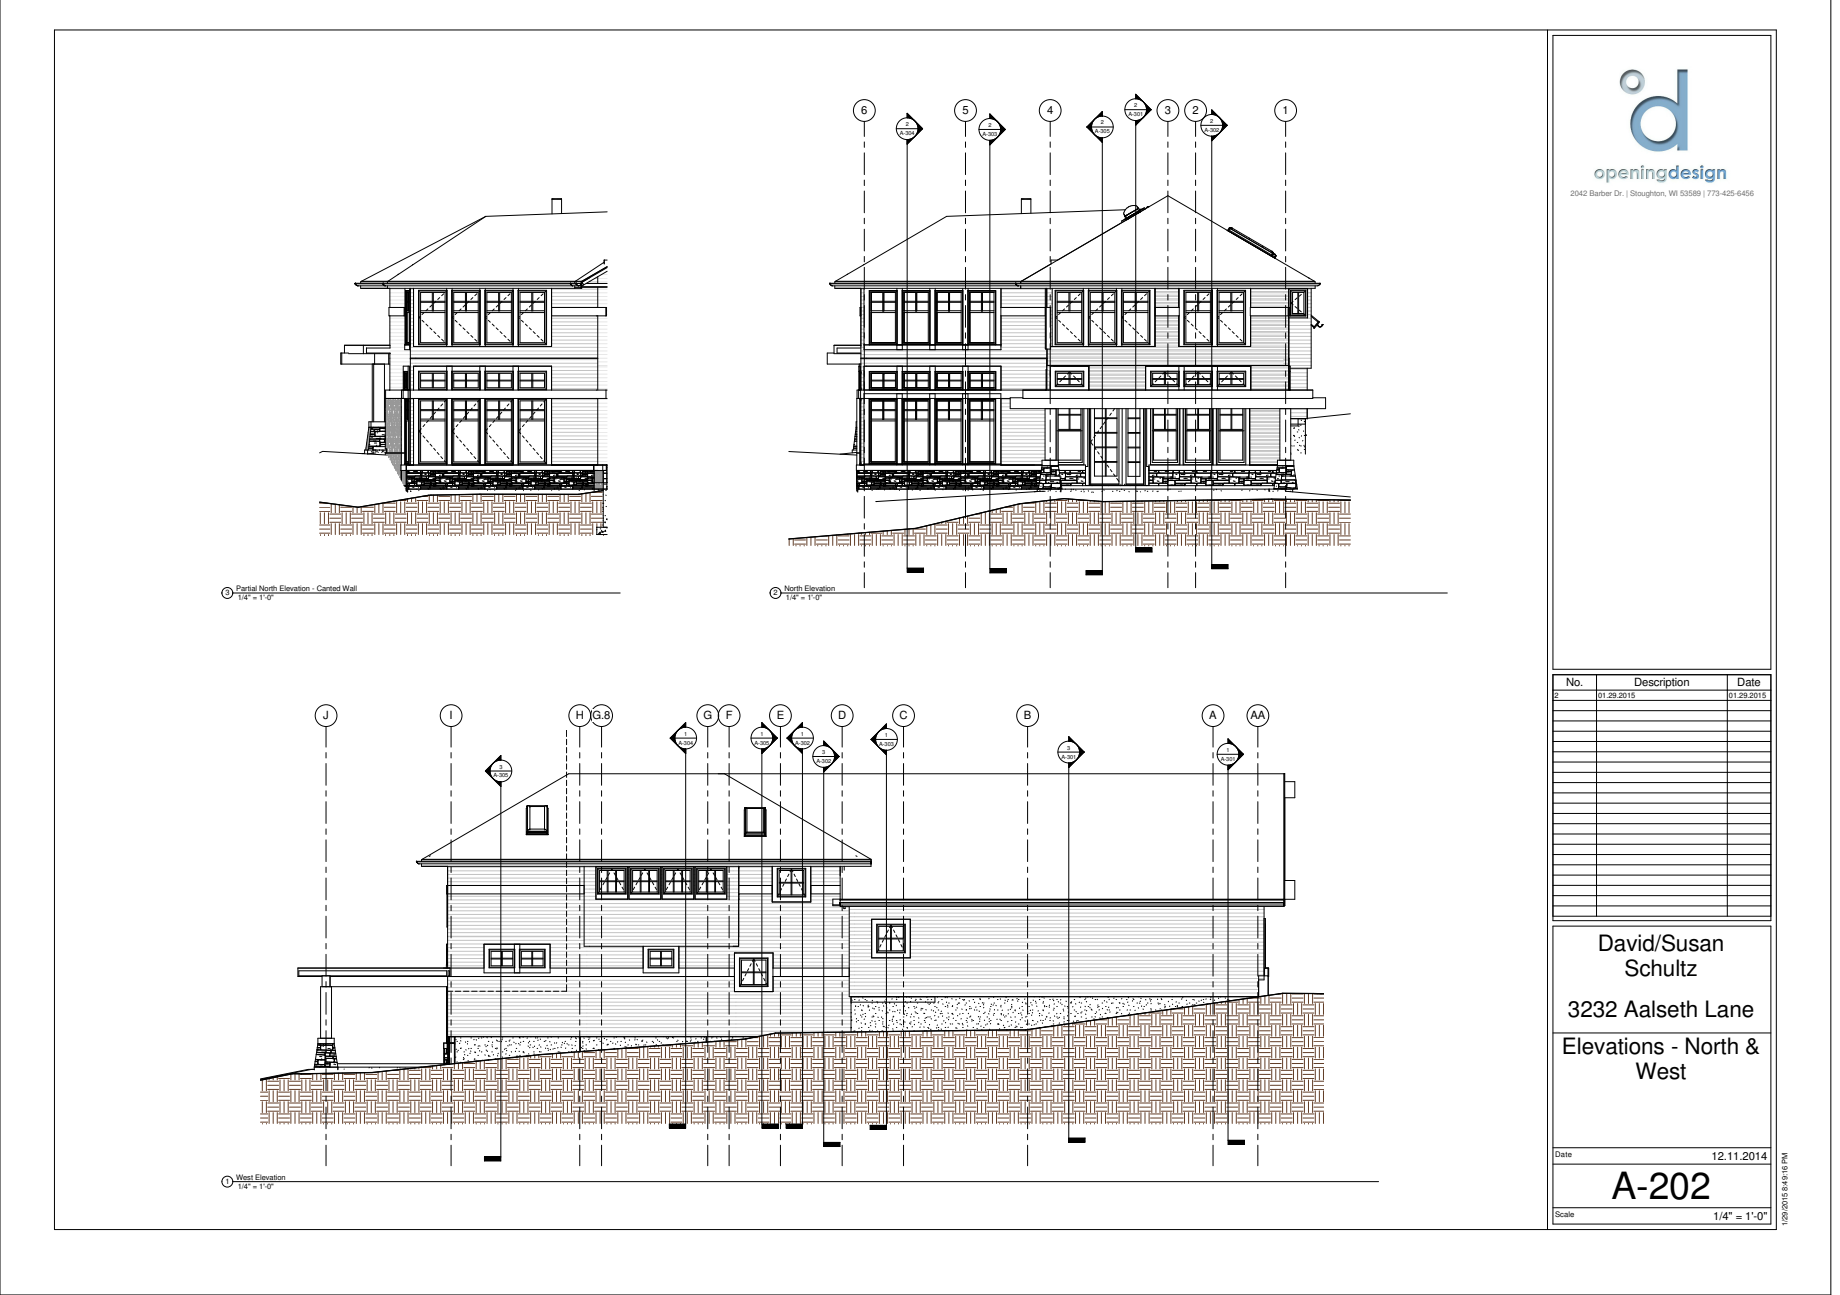
[picture p153: page 1]
Scale; Date; Elevations - North & West; David/Susan Schultz; 3232 Aalseth Lane; 1/4" = 1'-0" 1 West Elevation; 1/4" = 1'-0" 2 North Elevation; Description

2042 Barber Dr. | Stoughton, WI 53589 | 773-425-6456

1/4" = 1'-0" 3 Partial North Elevation - Canted Wall
