OpeningDesign/Lake_Kegonsa_Home/Transfer/20150129 - Full Set/Lake_Kegonsa_Home_3 - Sheet_ S-101 - Structural - Basement & Second Floor Framing.pdf

D H

2

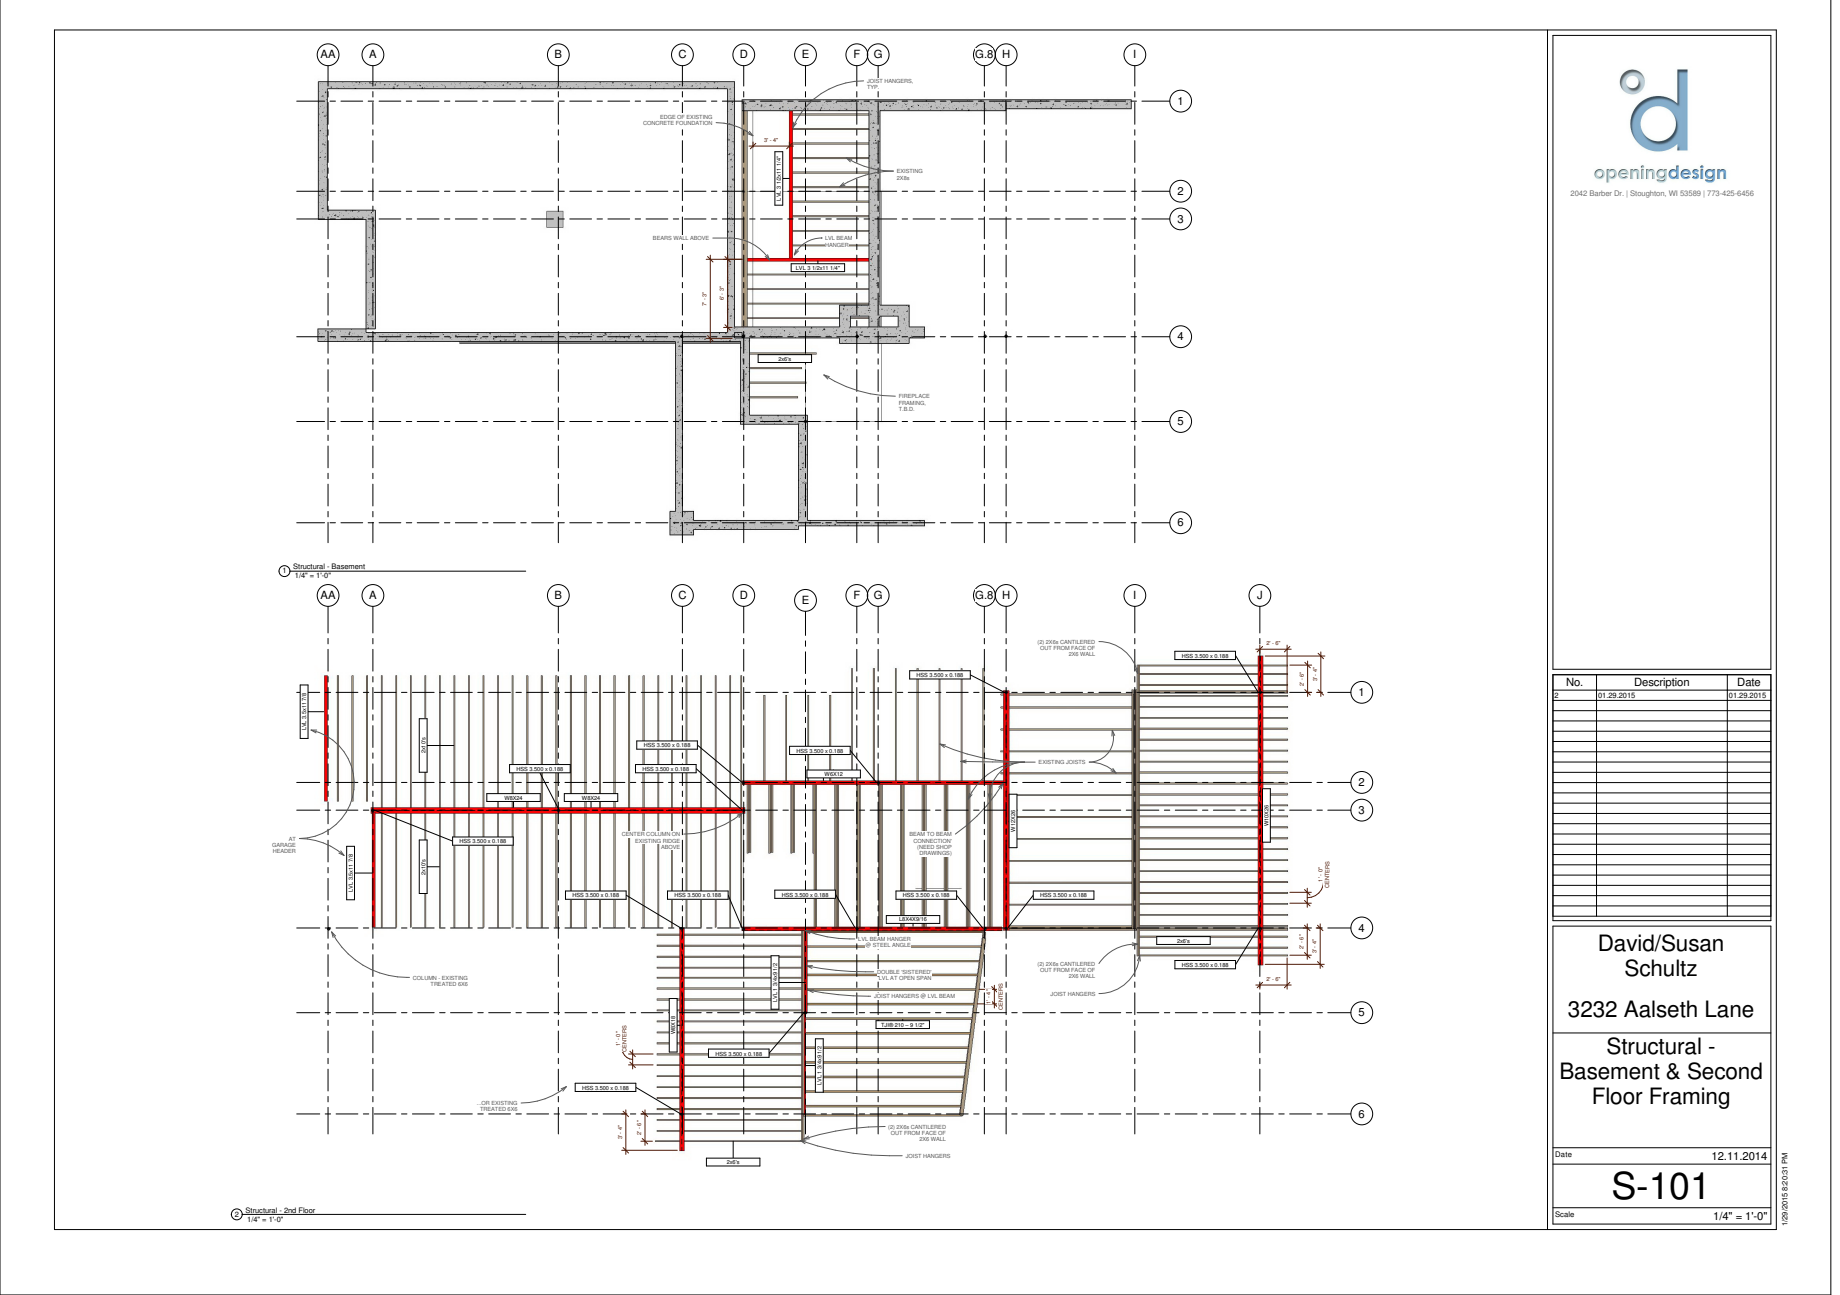
[picture p154: page 1]
LVL BEAM HANGER; EXISTING 2X8s; LVL 3 1/2x11 1/4"; FIREPLACE FRAMING, T.B.D.; JOIST HANGERS, TYP.; HSS 3.500 x 0.188; 2' - 6" 2' - 6" CENTERS 1' - 0" 2x6's; TJI® 210 – 9 1/2"; 2X6 WALL; JOIST HANGERS; EXISTING JOISTS; "(2) 2X6s CANTILERED; ABOVE; COLUMN - EXISTING TREATED 6X6; ...OR EXISTING TREATED 6X6; AT GARAGE HEADER; Scale; Date; Structural - Basement & Second Floor Framing; David/Susan Schultz; 3232 Aalseth Lane; 1/4" = 1'-0" 1 Structural - Basement; 1/4" = 1'-0" 2 Structural - 2nd Floor

EDGE OF EXISTING
CONCRETE FOUNDATION

2042 Barber Dr. | Stoughton, WI 53589 | 773-425-6456

BEARS WALL ABOVE

(2) 2X6s CANTILERED
OUT FROM FACE OF

No. | Description | Date

HSS 3.500 x 0.188

CENTER COLUMN ON
EXISTING RIDGE

BEAM TO BEAM
CONNECTION'
(NEED SHOP
DRAWINGS)

LVL BEAM HANGER
@ STEEL ANGLE

DOUBLE 'SISTERED'
LVL AT OPEN SPAN

JOIST HANGERS @ LVL BEAM
