OpeningDesign/Lake_Kegonsa_Home/Transfer/20150129 - Full Set/Lake_Kegonsa_Home_3 - Sheet_ S-102 - Structural - Roof.pdf

D | H

2

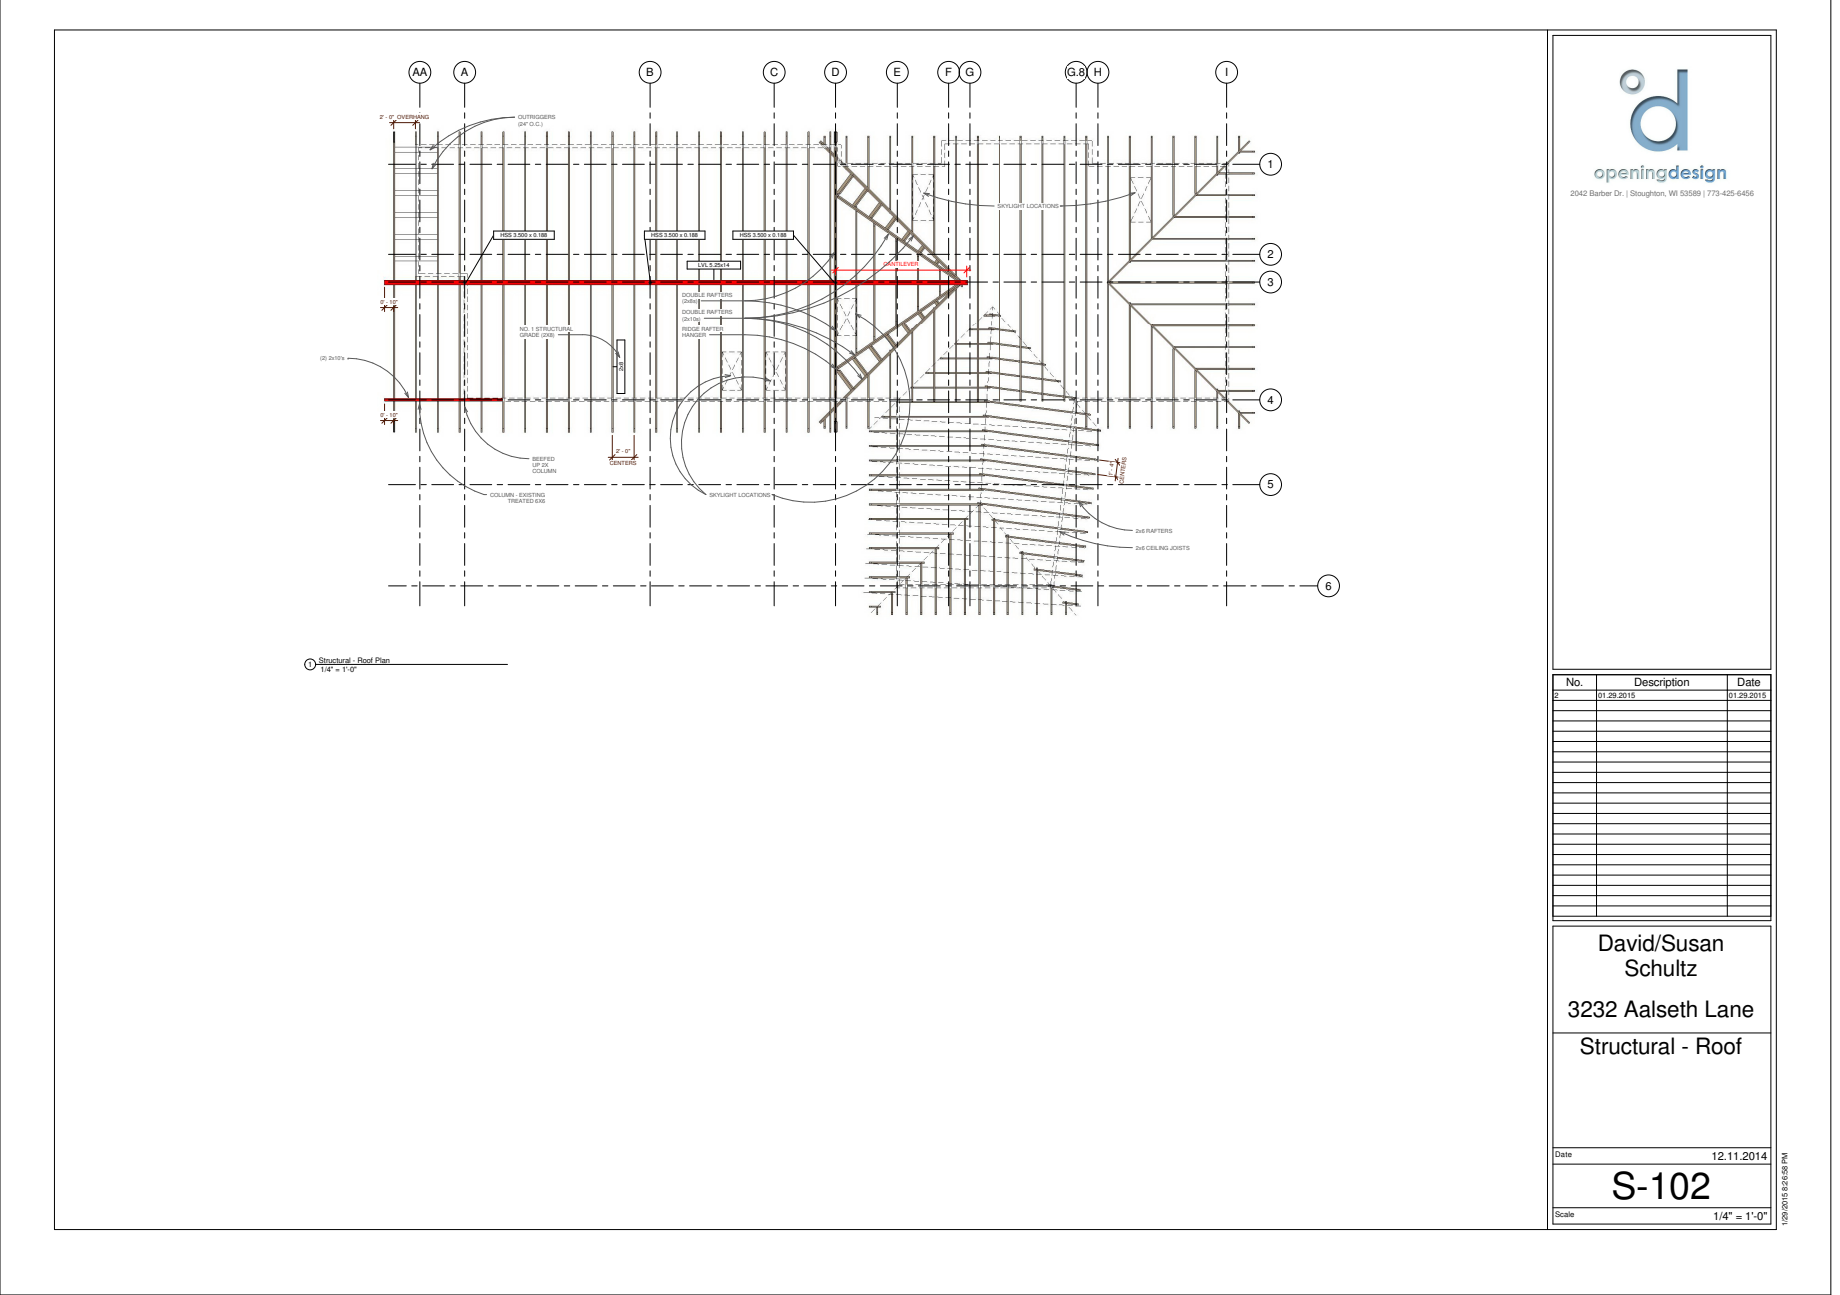
[picture p155: page 1]
CANTILEVER; HSS 3.500 x 0.188; LVL 5.25x14; BEEFED UP 2X COLUMN; OUTRIGGERS (24" O.C.); 2' - 0" OVERHANG; NO. 1 STRUCTURAL GRADE (2X8); CENTERS; SKYLIGHT LOCATIONS; 2x6 CEILING JOISTS; RIDGE RAFTER HANGER; DOUBLE RAFTERS (2x10s); 2x6 RAFTERS; COLUMN - EXISTING TREATED 6X6; DOUBLE RAFTERS (2x8s); Scale; Date; Structural - Roof; David/Susan Schultz; 3232 Aalseth Lane

2042 Barber Dr. | Stoughton, WI 53589 | 773-425-6456

1/4" = 1'-0" 1 Structural - Roof Plan

No. | Description | Date
