OpeningDesign/Lake_Kegonsa_Home/Transfer/20150116 - structure basement/20150116 - ASK-004 - Structural - Basement.pdf

D | H

B

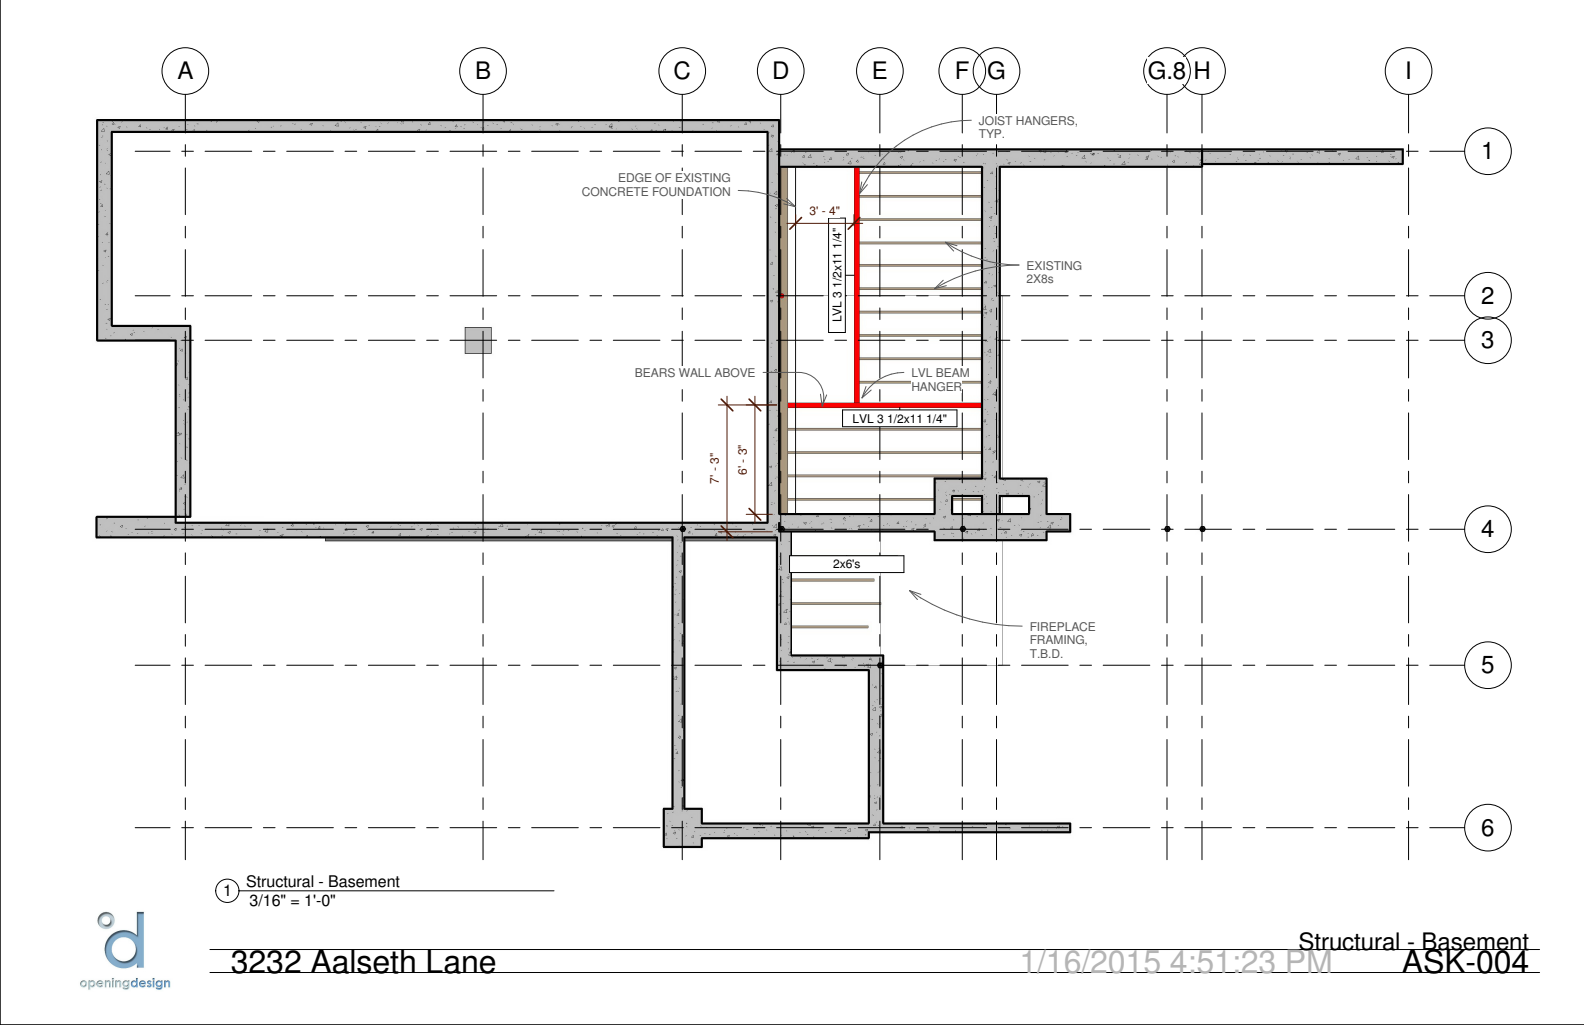
[picture p156: page 1]
LVL BEAM HANGER; EXISTING 2X8s; LVL 3 1/2x11 1/4"; CONCRETE FOUNDATION; FIREPLACE FRAMING, T.B.D.; JOIST HANGERS, TYP.; ASK-004 Structural - Basement 3232 Aalseth Lane; 3/16" = 1'-0" 1 Structural - Basement

EDGE OF EXISTING

BEARS WALL ABOVE
