OpeningDesign/Lake_Kegonsa_Home/Transfer/20150122 - 2nd Floor Structure/20150122 - ASK-006 - 2nd Floor Structure.pdf

D H

B J

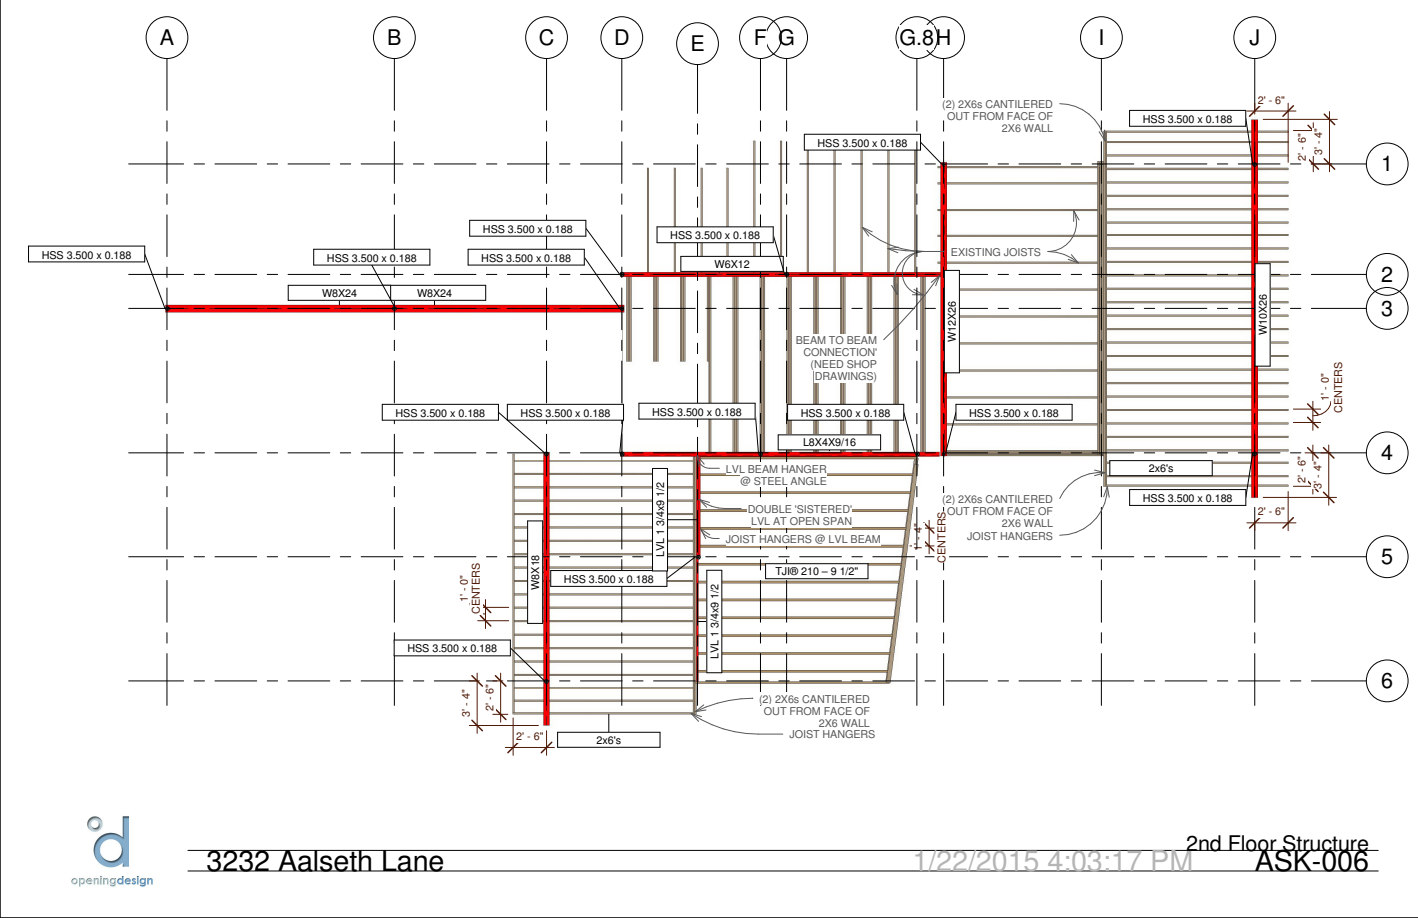
[picture p157: page 1]
HSS 3.500 x 0.188 HSS 3.500 x 0.188; HSS 3.500 x 0.188; 2' - 6" 2' - 6" CENTERS 1' - 0" 2x6's; TJI® 210 – 9 1/2"; 2X6 WALL; JOIST HANGERS; EXISTING JOISTS; 2X6 WALL JOIST HANGERS; ASK-006 ²nd Floor Structure 3232 Aalseth Lane

(2) 2X6s CANTILERED
OUT FROM FACE OF

BEAM TO BEAM
CONNECTION'
(NEED SHOP
DRAWINGS)

LVL BEAM HANGER
@ STEEL ANGLE

DOUBLE 'SISTERED'
LVL AT OPEN SPAN
JOIST HANGERS @ LVL BEAM
