OpeningDesign/Lake_Kegonsa_Home/Transfer/20150125 - Entry/ASK-007 - Entry.pdf

D
4

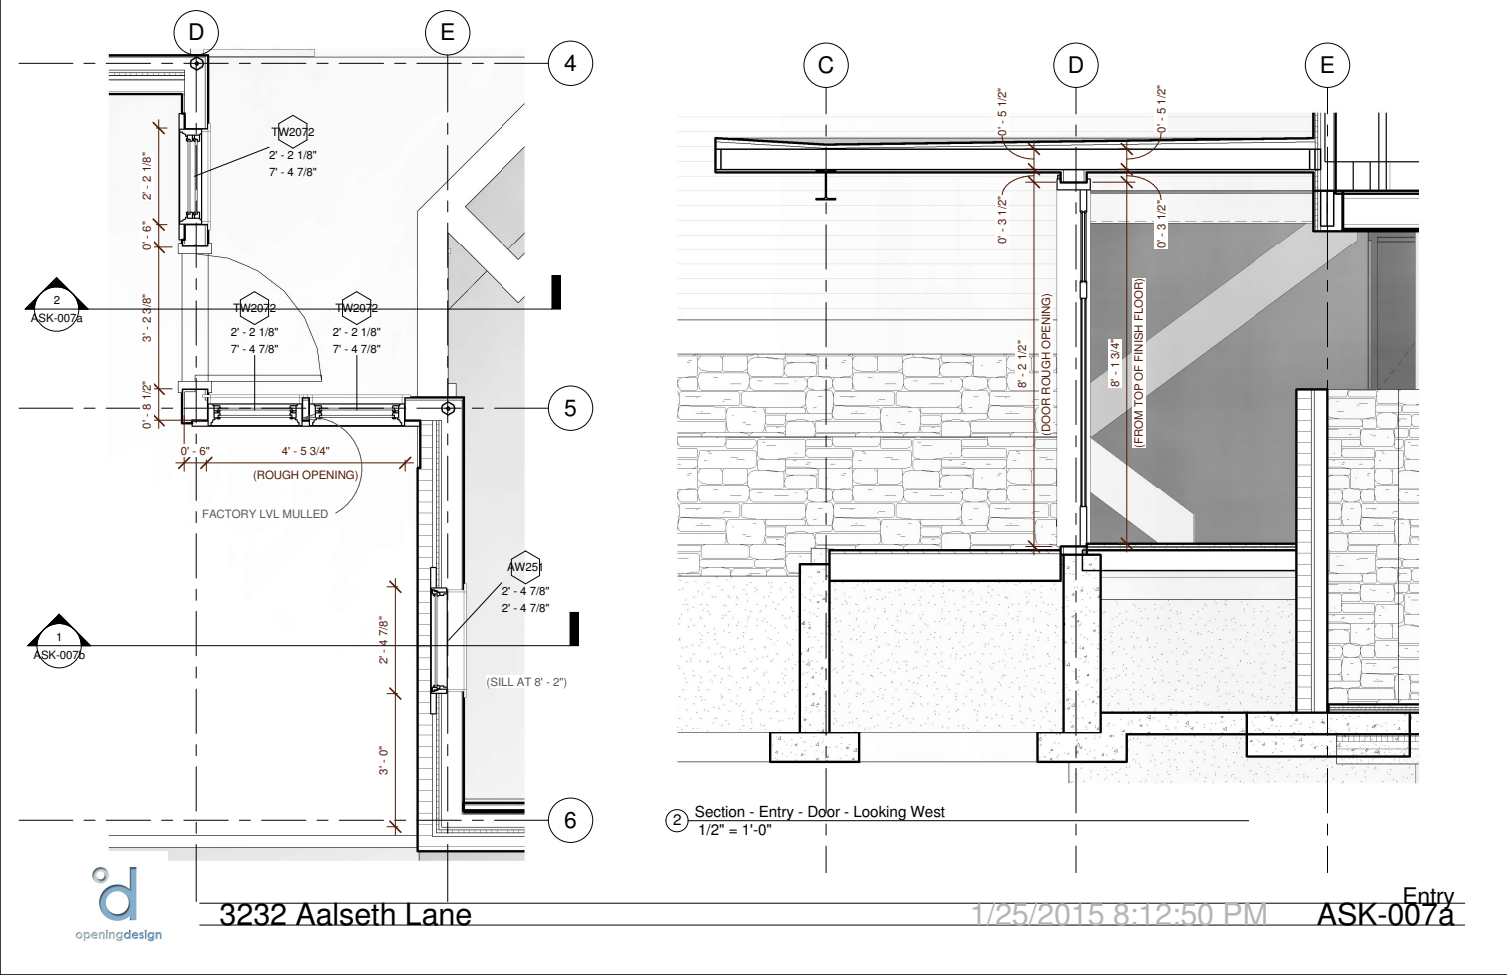
[picture p158: page 1]
(SILL AT 8' - 2"); (ROUGH OPENING); ASK-007a; ASK-007b; ASK-007a Entry 3232 Aalseth Lane

(FROM TOP OF FINISH FLOOR)

(DOOR ROUGH OPENING)

FACTORY LVL MULLED

1/2" = 1'-0" 2 Section - Entry - Door - Looking West


# 1/25/2015 8:12:51 PM ASK-007b Entry 3232 Aalseth Lane

## 1/2" = 1'-0" 1 Section - Entry - Looking West

4 | 5 | 6

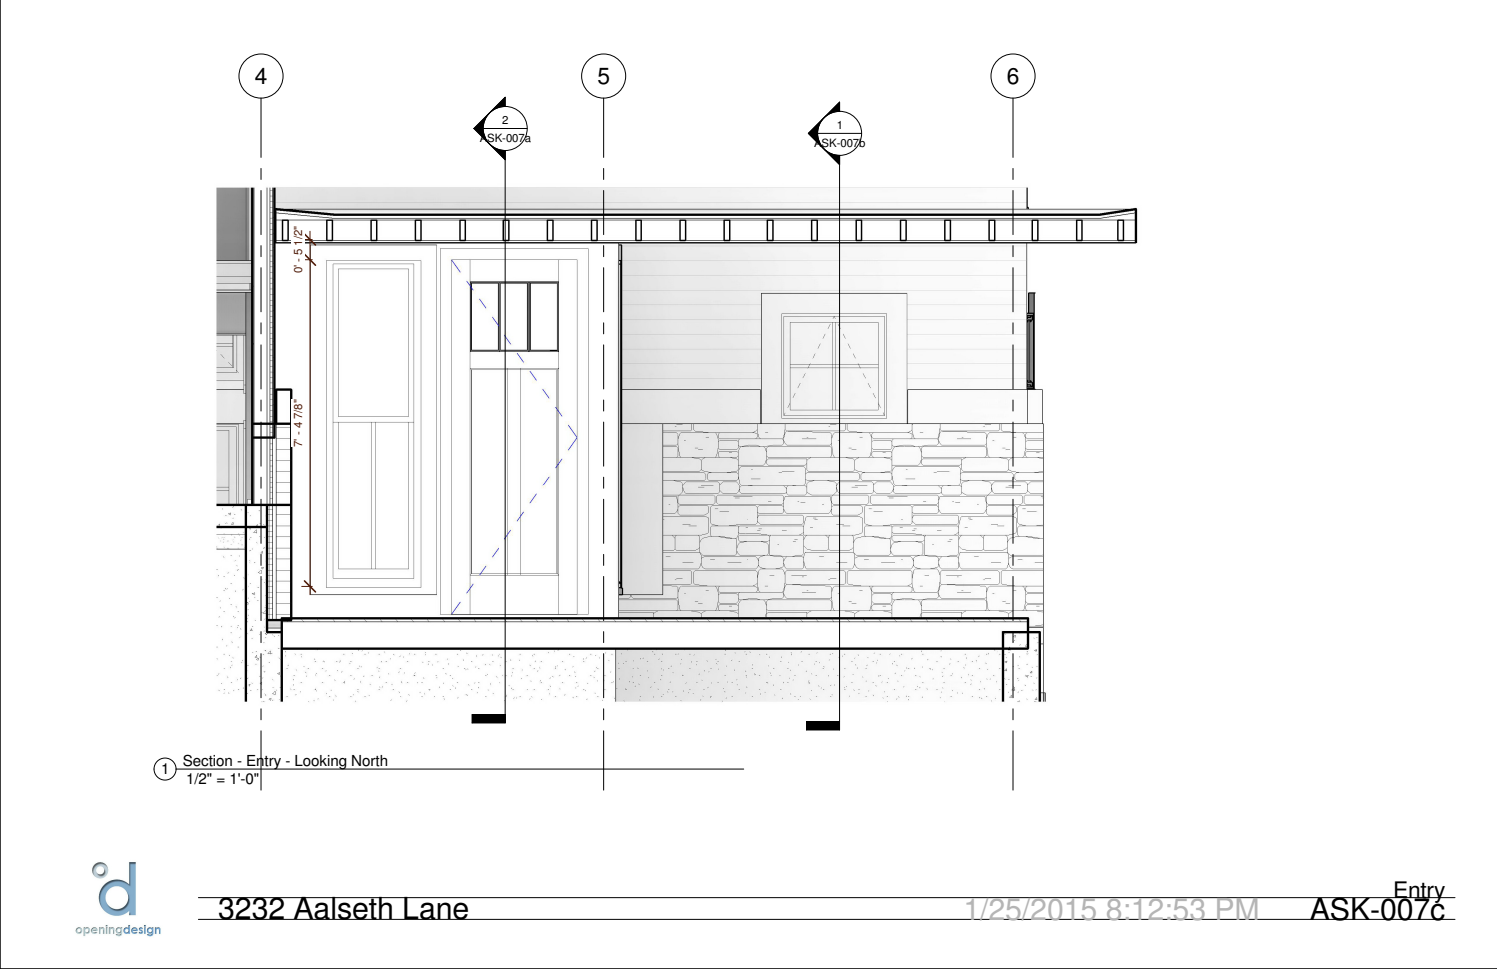
[picture p159: page 3]
ASK-007a; ASK-007b; ASK-007c Entry 3232 Aalseth Lane

1/2" = 1'-0" 1 Section - Entry - Looking North
