OpeningDesign/Lake_Kegonsa_Home/Out/20141201 - structural review/20141201 - S-102 - Kegonsa - 2nd Floor Structural _for review.pdf

D H

2

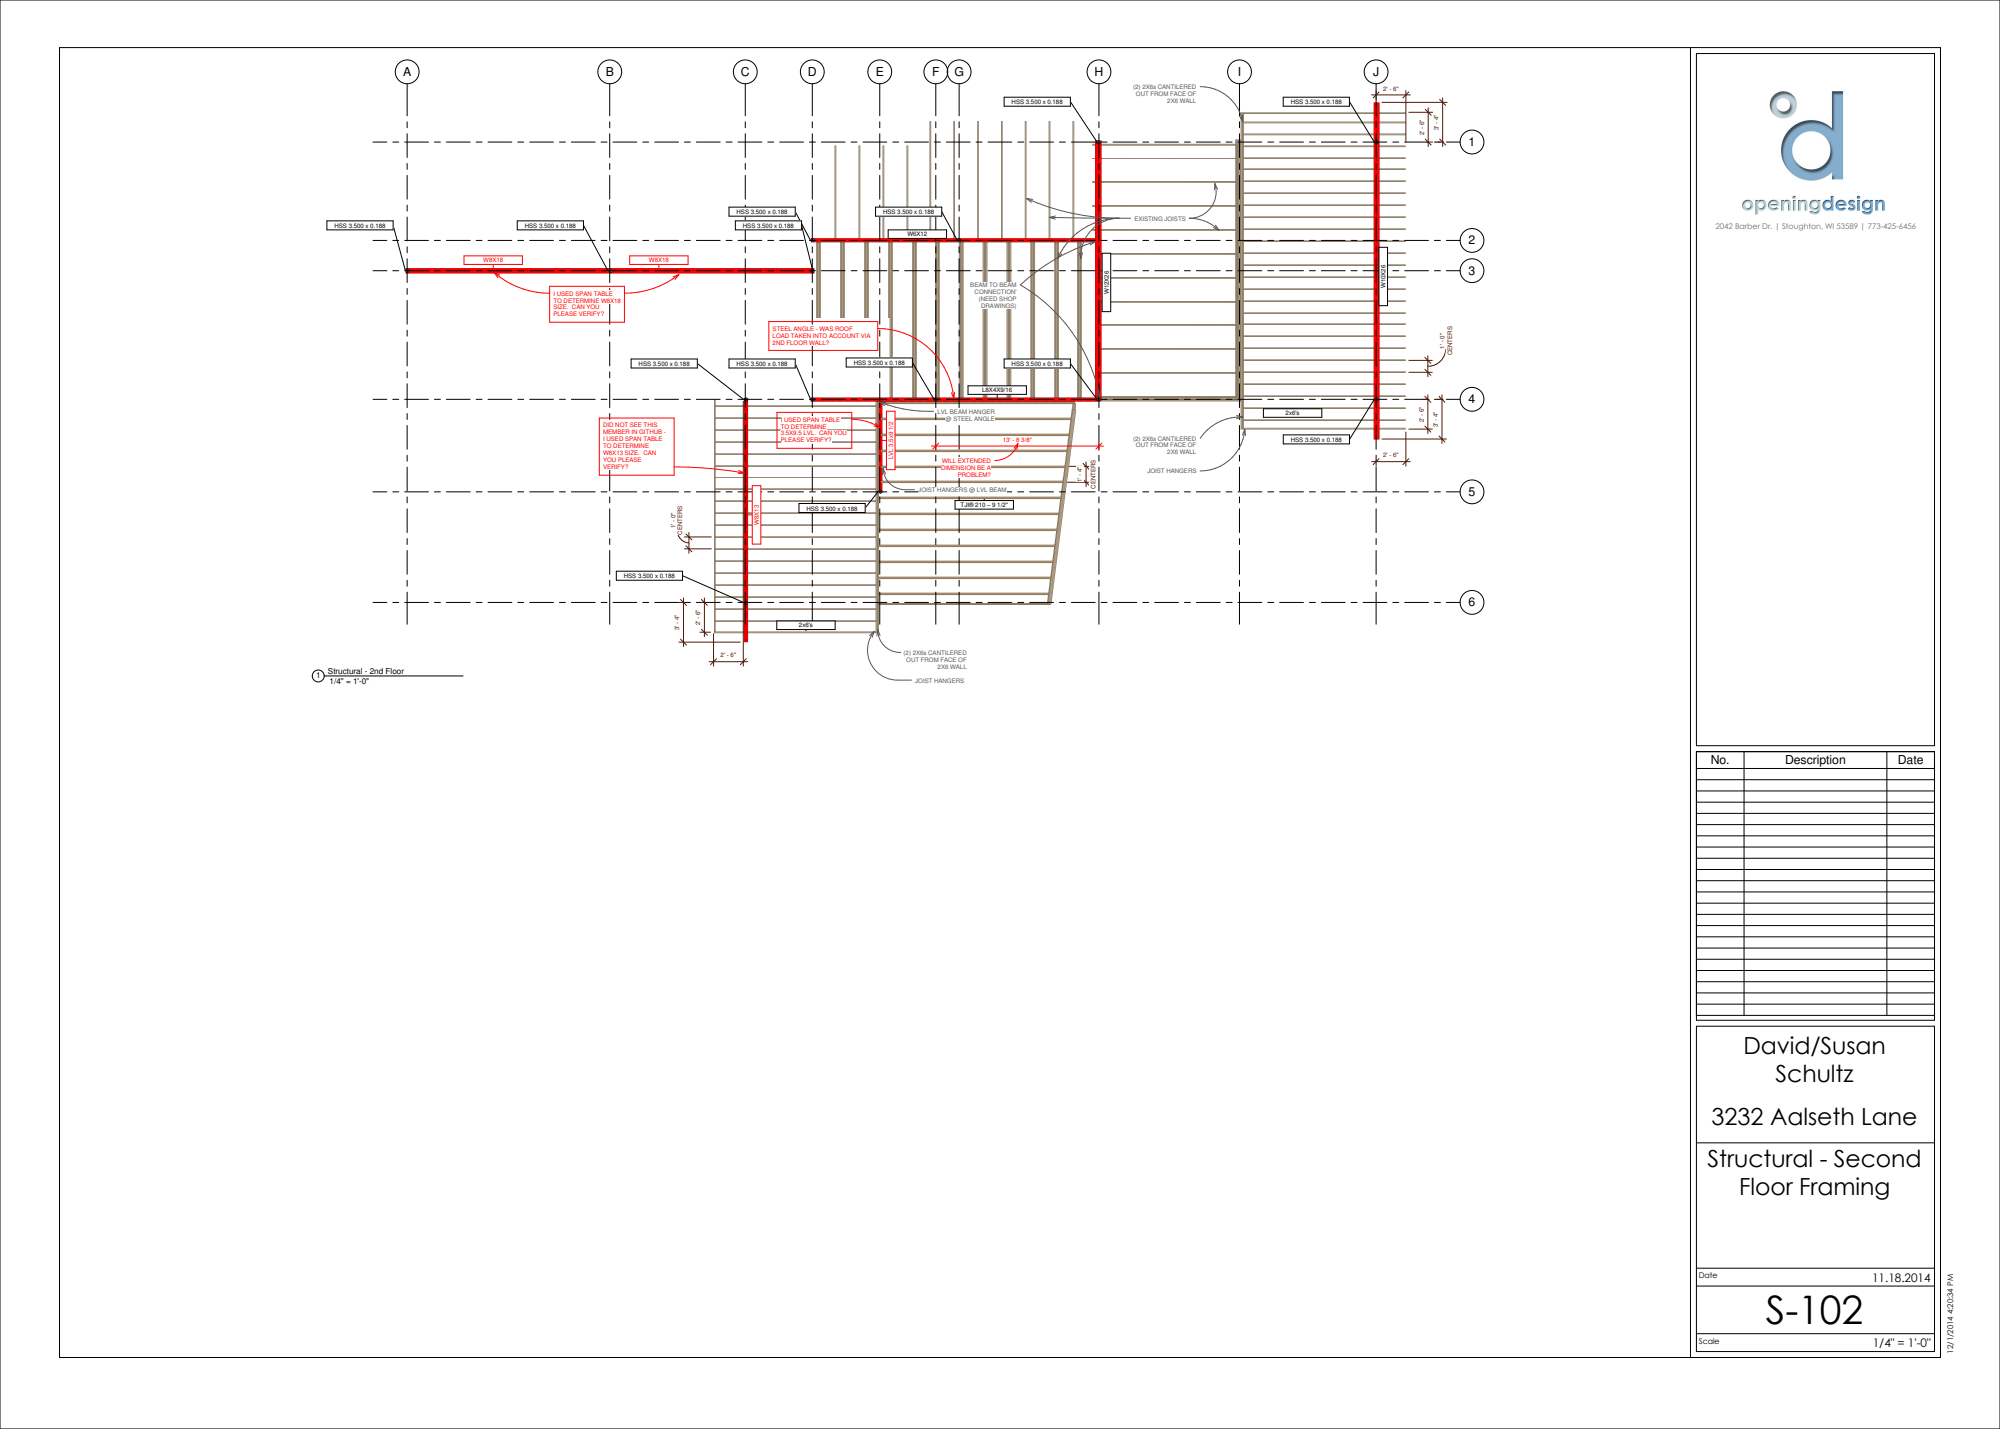
[picture p160: page 1]
HSS 3.500 x 0.188; 2' - 6" 2' - 6" CENTERS 1' - 0" 2x6's; TJI® 210 – 9 1/2"; 2X6 WALL; JOIST HANGERS; EXISTING JOISTS; WILL EXTENDED DIMENSION BE A PROBLEM?; Scale; Date; Structural - Second Floor Framing; David/Susan Schultz; 3232 Aalseth Lane; Description; 1/4" = 1'-0" 1 Structural - 2nd Floor

(2) 2X6s CANTILERED
OUT FROM FACE OF

2042 Barber Dr. | Stoughton, WI 53589 | 773-425-6456

BEAM TO BEAM
CONNECTION'
(NEED SHOP
DRAWINGS)

I USED SPAN TABLE TO DETERMINE W8X18

SIZE. CAN YOU
PLEASE VERIFY?

STEEL ANGLE - WAS ROOF LOAD TAKEN INTO ACCOUNT VIA 2ND FLOOR WALL?

LVL BEAM HANGER
@ STEEL ANGLE

2I USED SPAN TABLE TO DETERMINE

DID NOT SEE THIS
MEMBER IN GITHUB -
I USED SPAN TABLE
TO DETERMINE
W8X13 SIZE. CAN
YOU PLEASE
VERIFY?

3.5X9.5 LVL. CAN YOU

JOIST HANGERS @ LVL BEAM
