OpeningDesign/Lake_Kegonsa_Home/Out/20141021 - plans to surveyor/20141021 - 3232 Aalseth Lane - Site Plan.pdf

### 2042 Barber Dr. | Stoughton, WI 53589 | 773-425-645

6

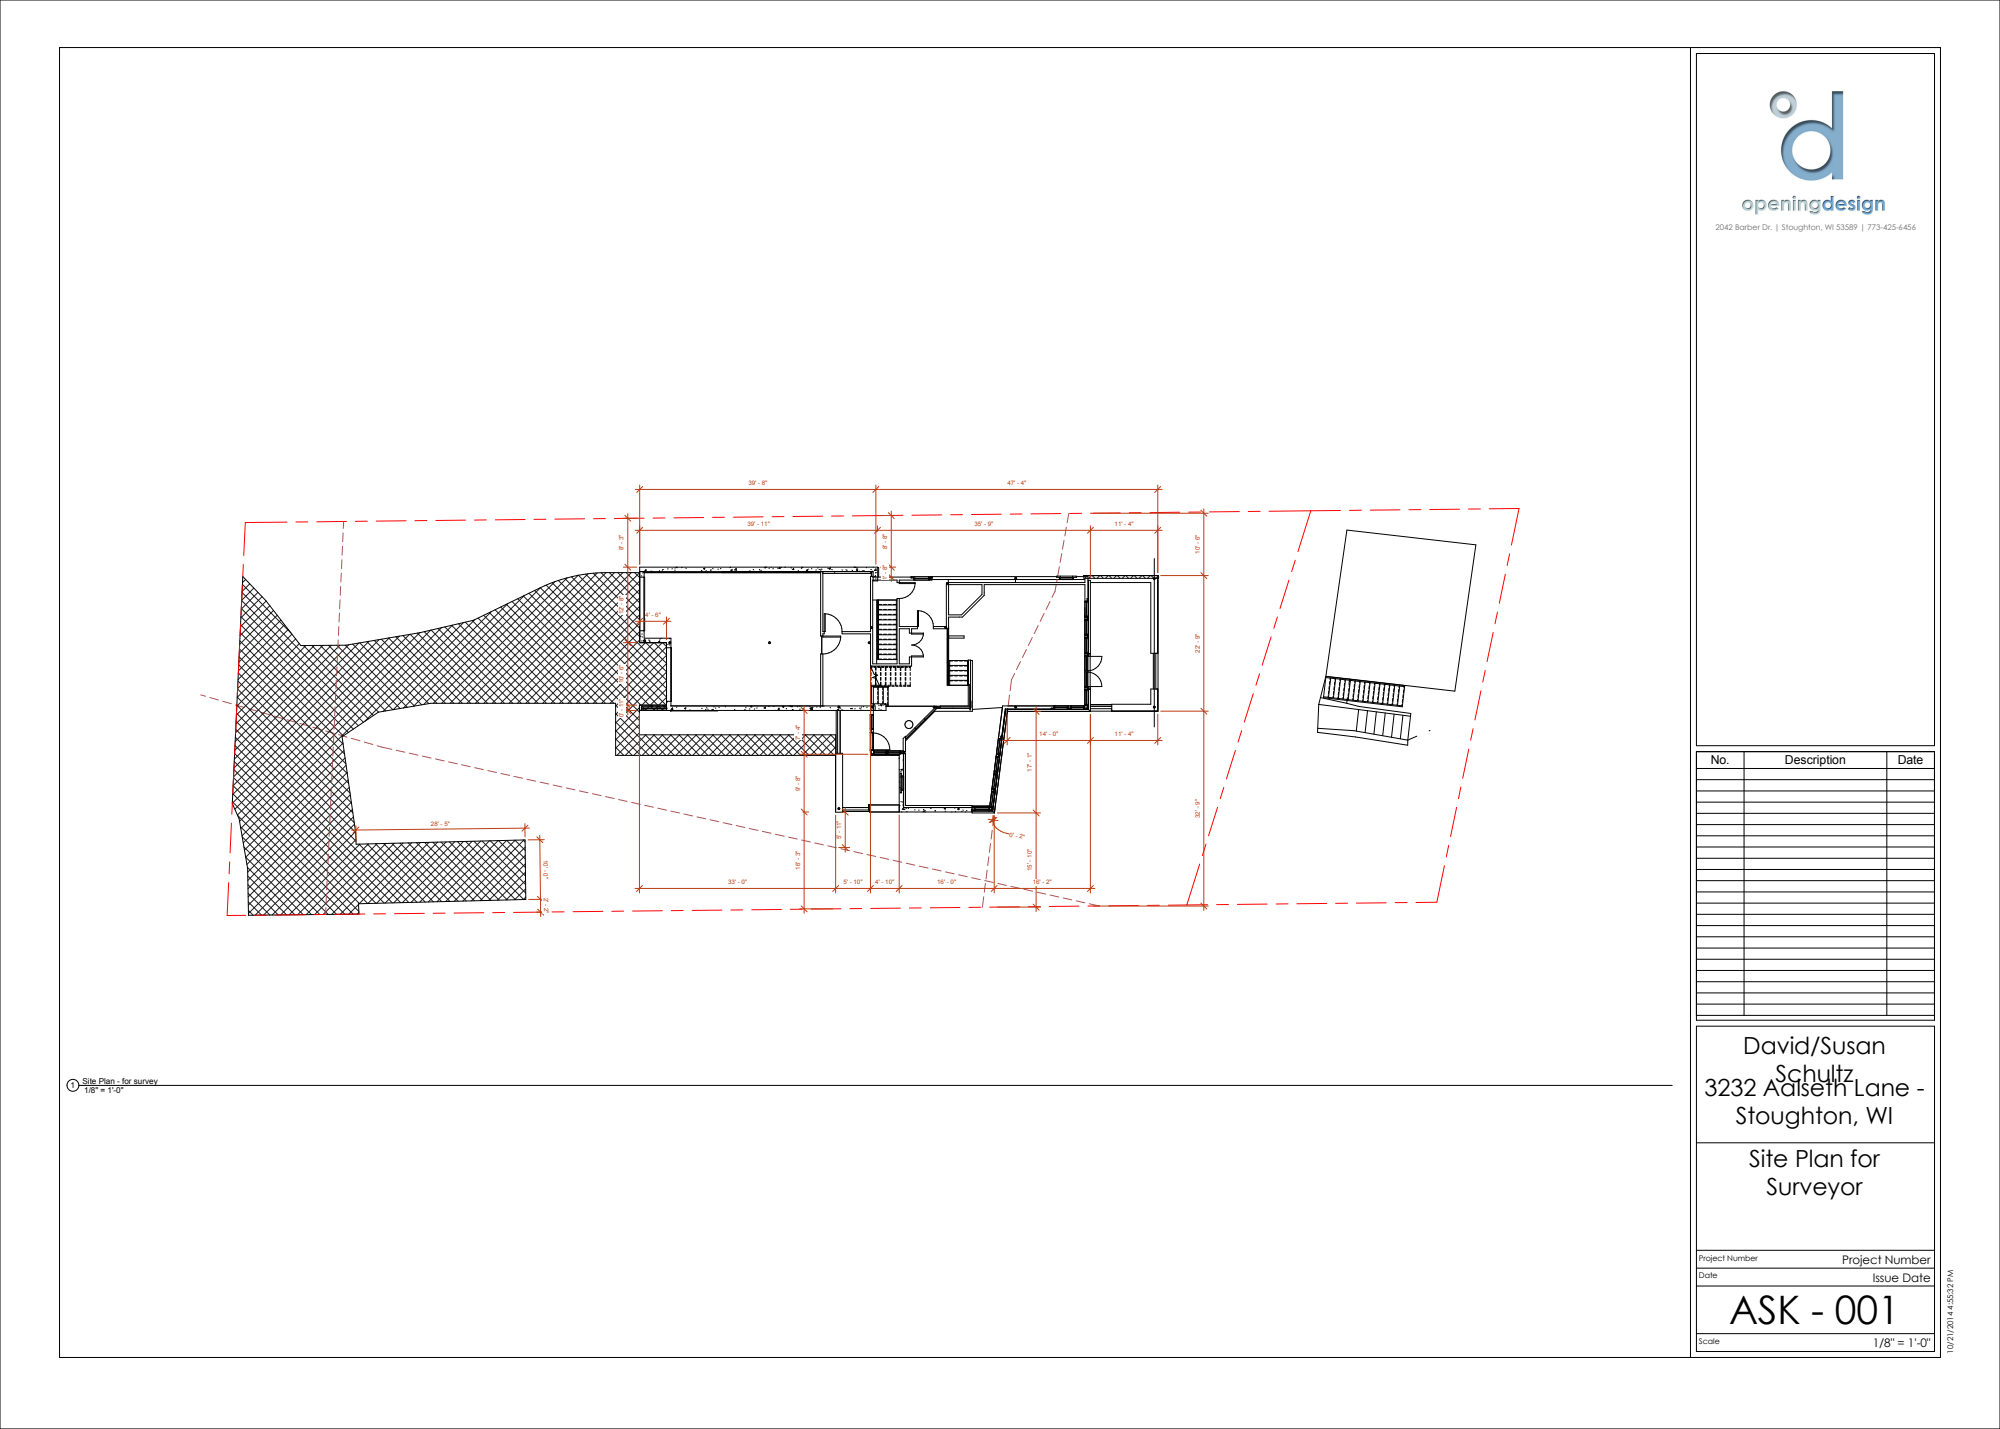
[picture p161: page 1]
Scale; Date; Project Number; 10/21/2014 4:55:32 PM ASK - 001 Issue Date; Description

David/Susan
Schultz 3232 Aalseth Lane -
Stoughton, WI
Site Plan for
Surveyor

1 Site Plan - for survey
