OpeningDesign/Lake_Kegonsa_Home/Out/20141022 - 3rd floor window locations/20141022 - ASK-002 - 3rd floor window locations.pdf

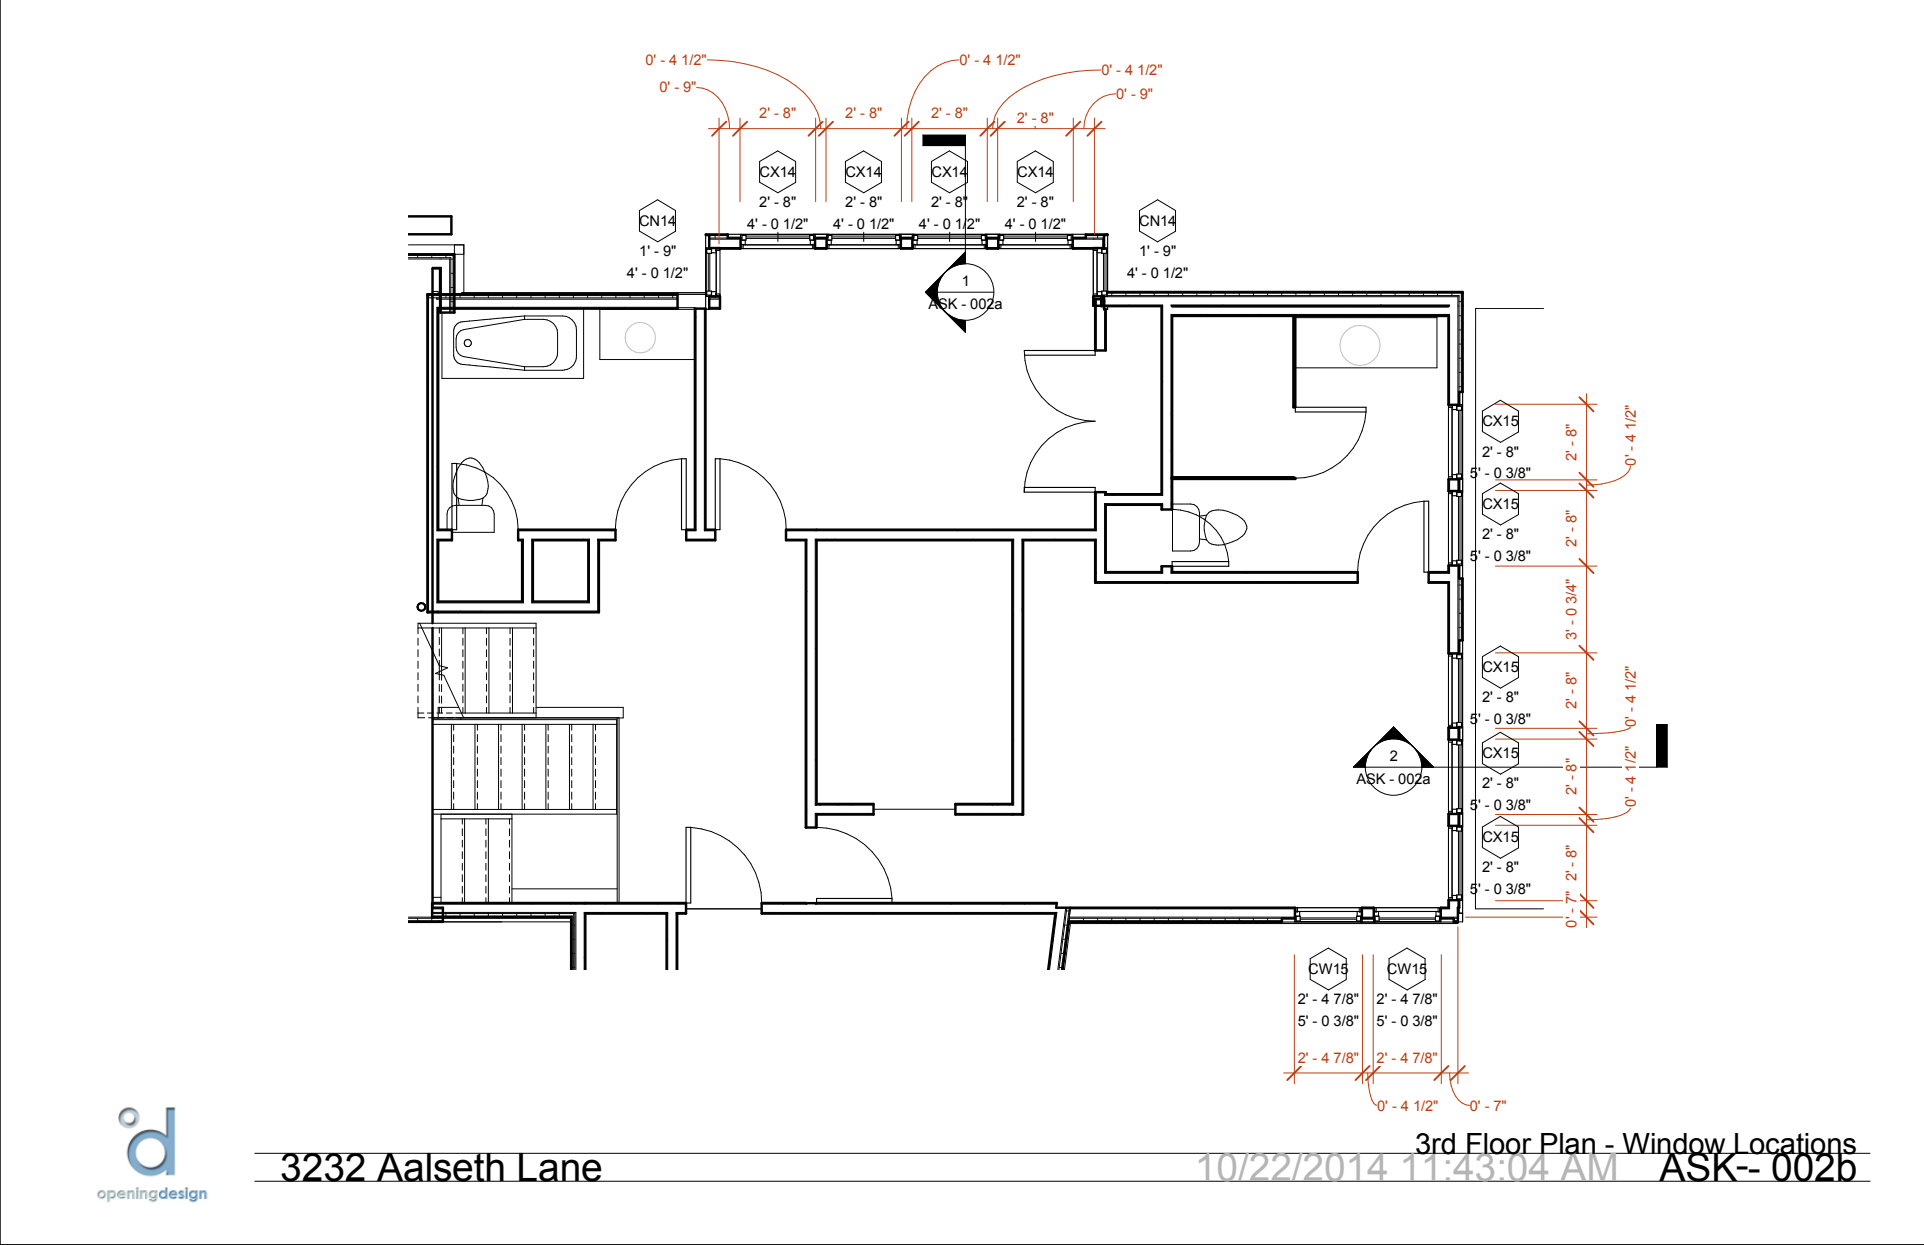
[picture p162: page 1]
ASK - 002a; ASK - 002b -

3rd Floor Plan - Window Locations 3232 Aalseth Lane

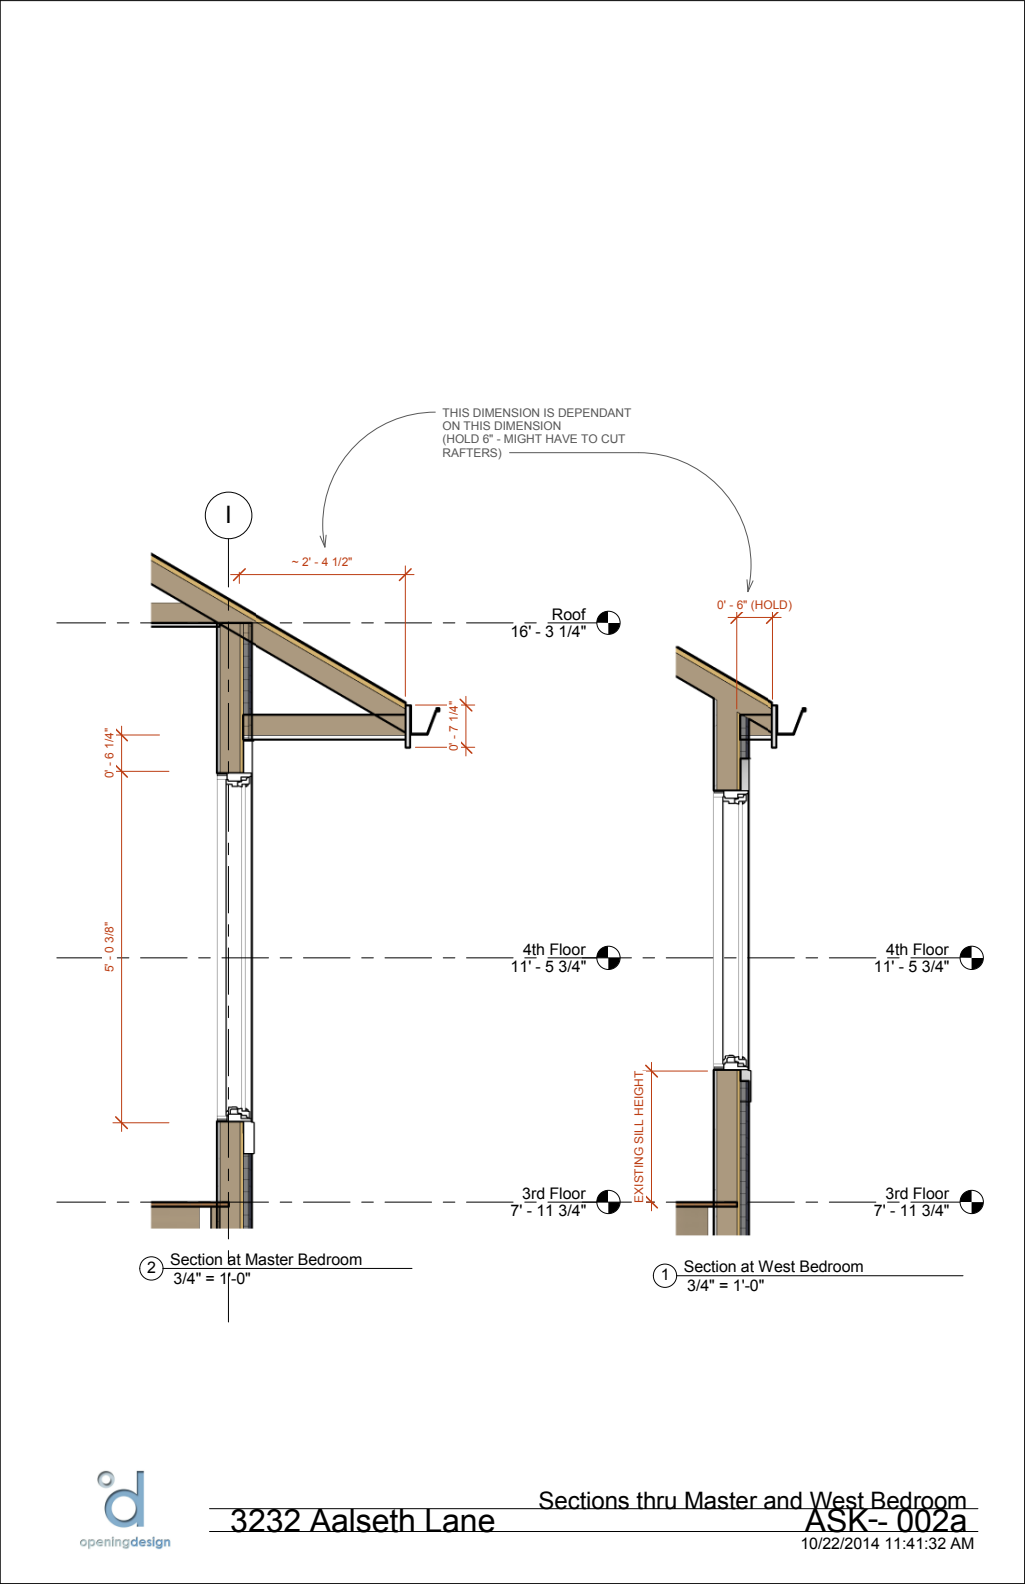
[picture p163: page 2]
3rd Floor 7' - 11 3/4"; Roof 16' - 3 1/4"; 4th Floor 11' - 5 3/4"; 0' - 6" (HOLD)

THIS DIMENSION IS DEPENDANT
ON THIS DIMENSION
(HOLD 6" - MIGHT HAVE TO CUT
RAFTERS)

EXISTING SILL HEIGHT - 10/22/2014 11:41:32 AM ASK - 002a Sections thru Master and West Bedroom 3232 Aalseth Lane 3/4" = 1'-0" 2 Section at Master Bedroom 3/4" = 1'-0" 1 Section at West Bedroom
