OpeningDesign/Lake_Kegonsa_Home/Out/20141023 - new header location/20141023 - ASK-002 - 3rd floor window locations.pdf

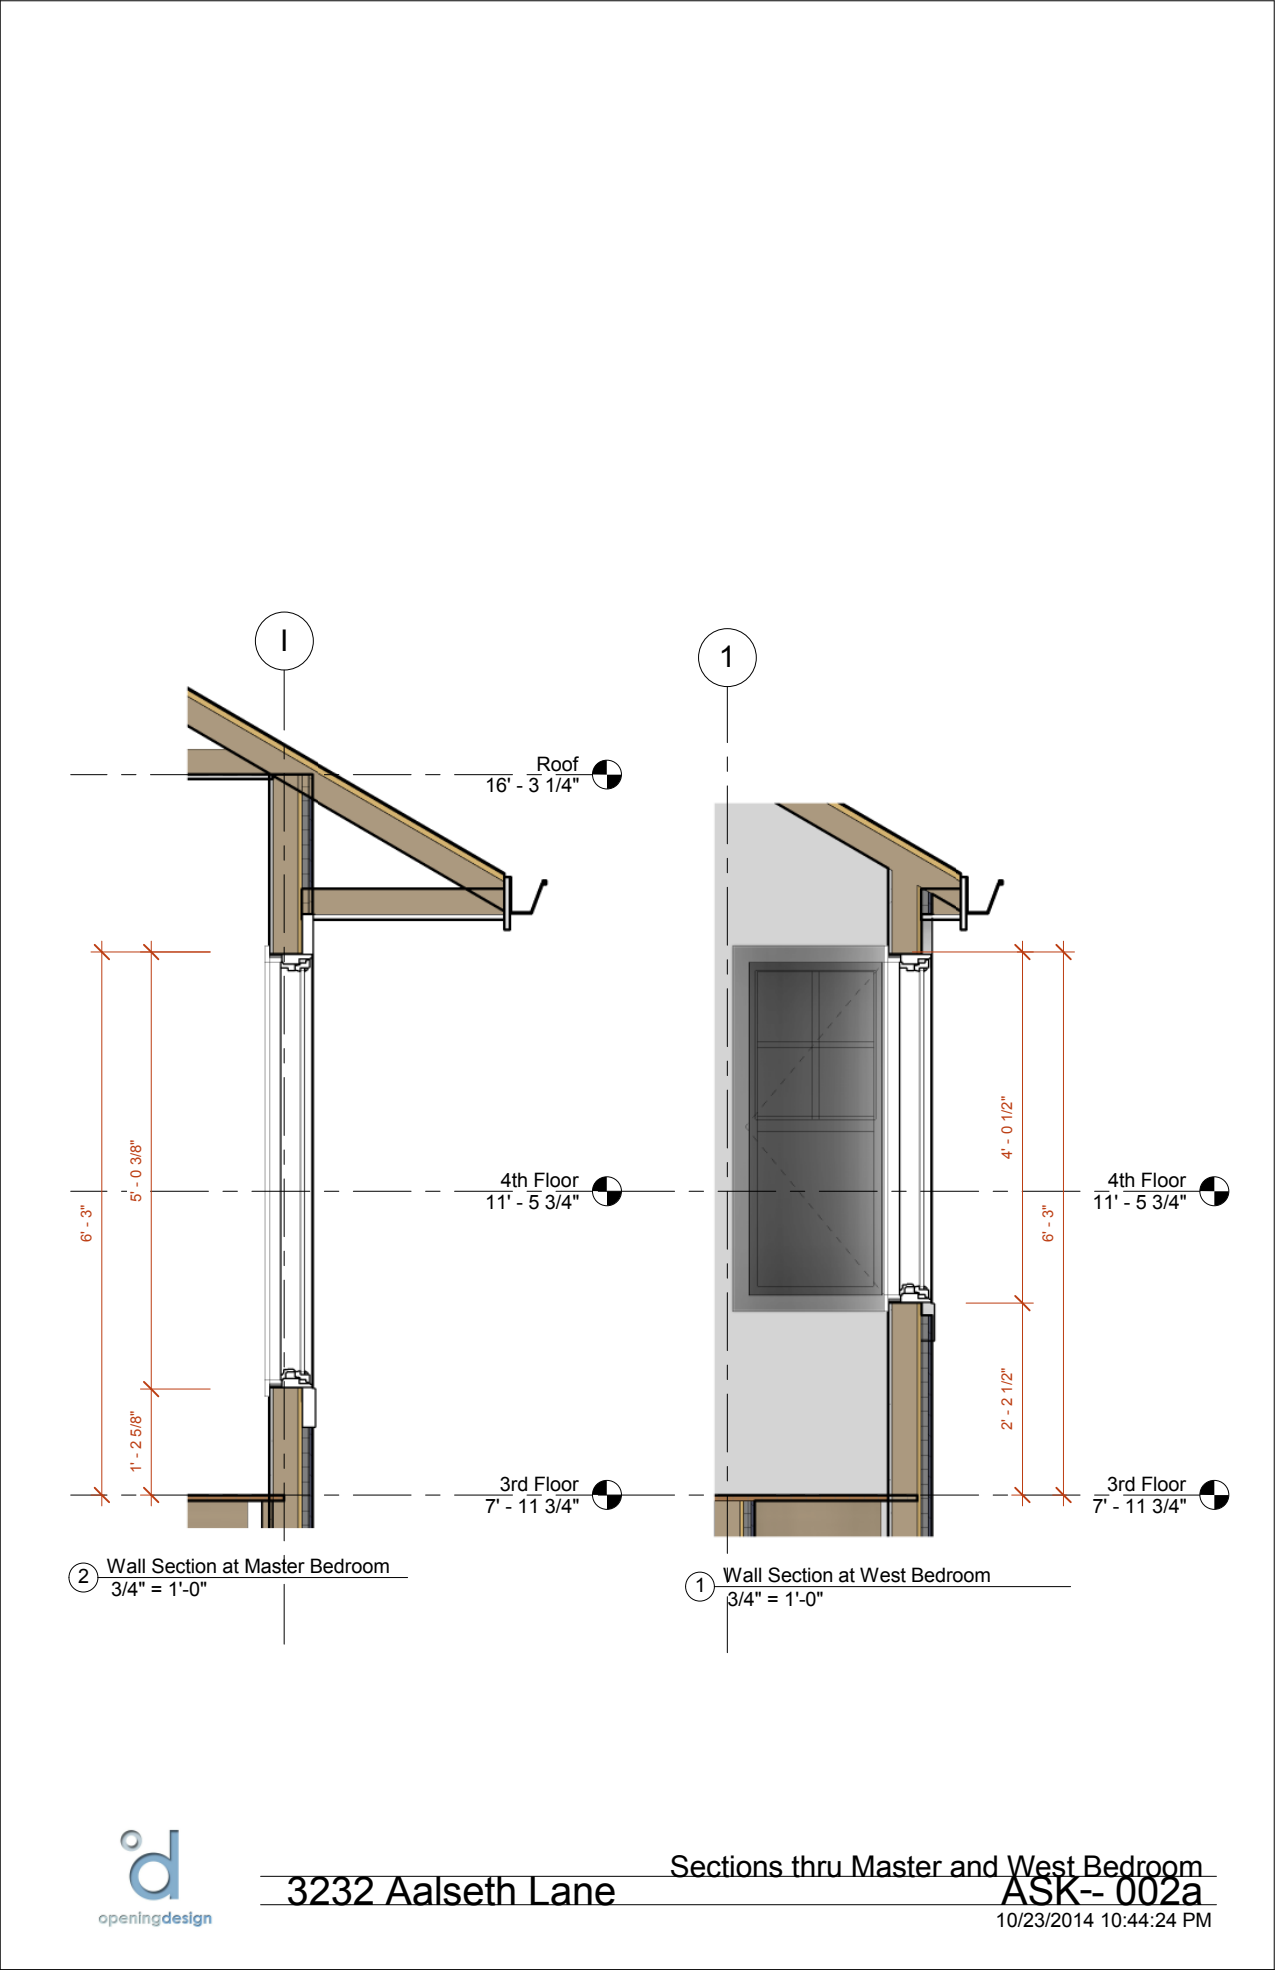
[picture p164: page 1]
3rd Floor 7' - 11 3/4"; Roof; 4th Floor 11' - 5 3/4"

6' - 3" - 10/23/2014 10:44:24 PM ASK - 002a Sections thru Master and West Bedroom 3232 Aalseth Lane 3/4" = 1'-0" 2 Wall Section at Master Bedroom 3/4" = 1'-0" 1 Wall Section at West Bedroom
