OpeningDesign/Lake_Kegonsa_Home/Out/20141014 - Stree Elevation/20141014 - 3232 Aalseth Lane - Street Elevation.pdf

2 | 4
1 | 3 | 5 | 6

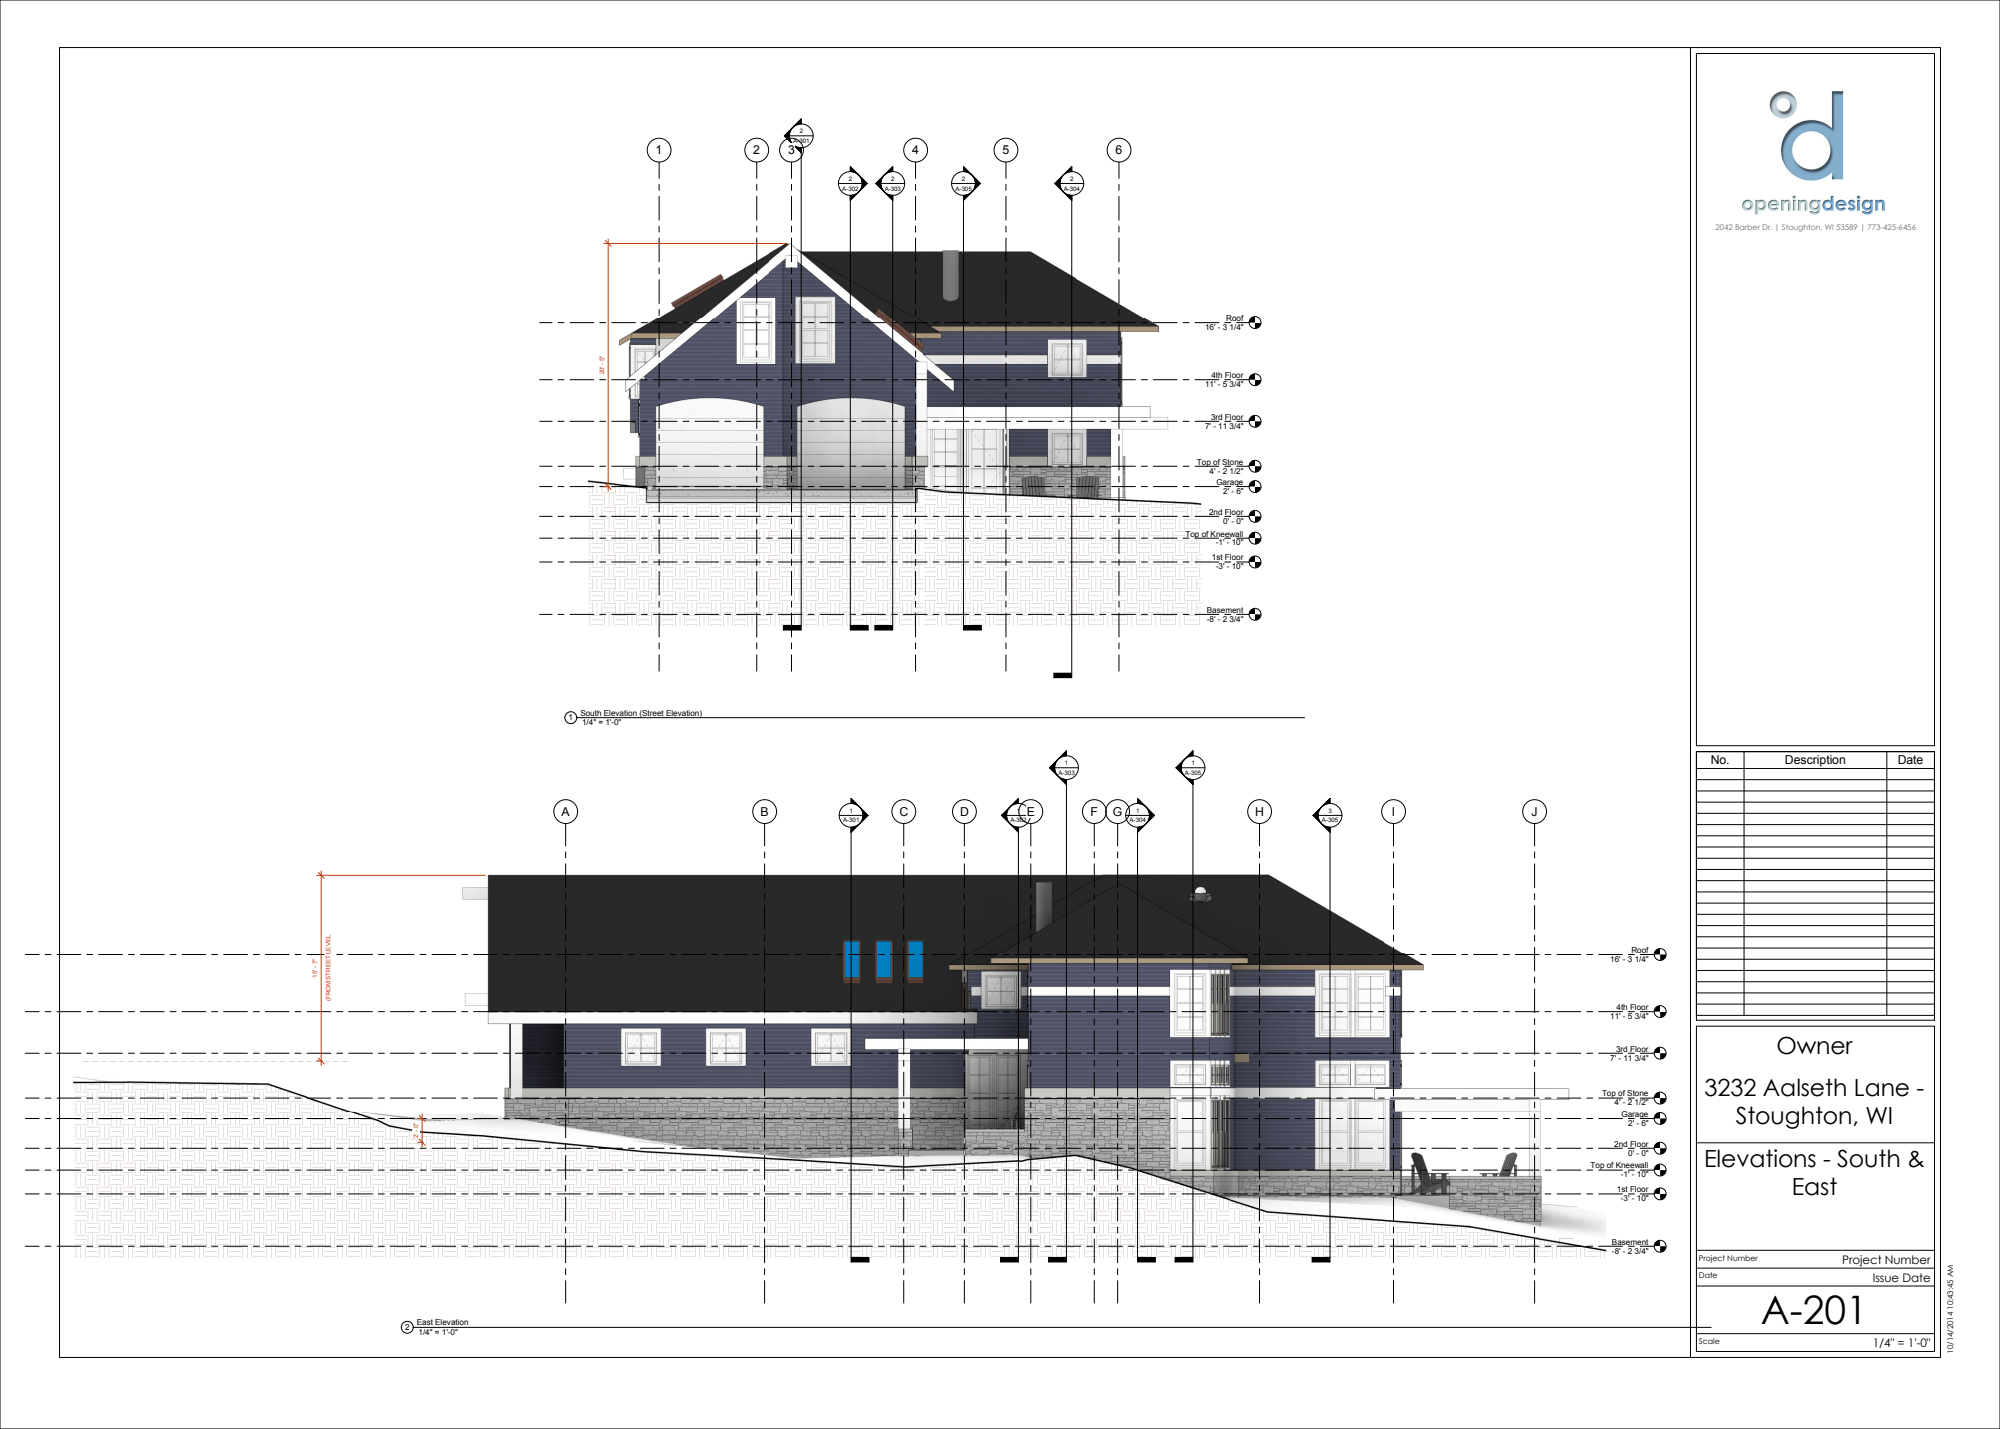
[picture p165: page 1]
2nd Floor 0' - 0"; 3rd Floor 7' - 11 3/4"; Basement -8' - 2 3/4"; Roof 16' - 3 1/4"; 1st Floor -3' - 10"; Garage 2' - 6"; 4th Floor 11' - 5 3/4"; Top of Stone 4' - 2 1/2"; Scale; Date; Project Number; Elevations - South & East; Owner; 3232 Aalseth Lane - Stoughton, WI; Issue Date; 1/4" = 1'-0" 2 East Elevation; Description

2042 Barber Dr. | Stoughton, WI 53589 | 773-425-6456

Top of Kneewall

1/4" = 1'-0" 1 South Elevation (Street Elevation)
