OpeningDesign/Lake_Kegonsa_Home/Out/20140909 - Site Plan to Surveyor/3232 Aalseth Lane - Site Plan.pdf

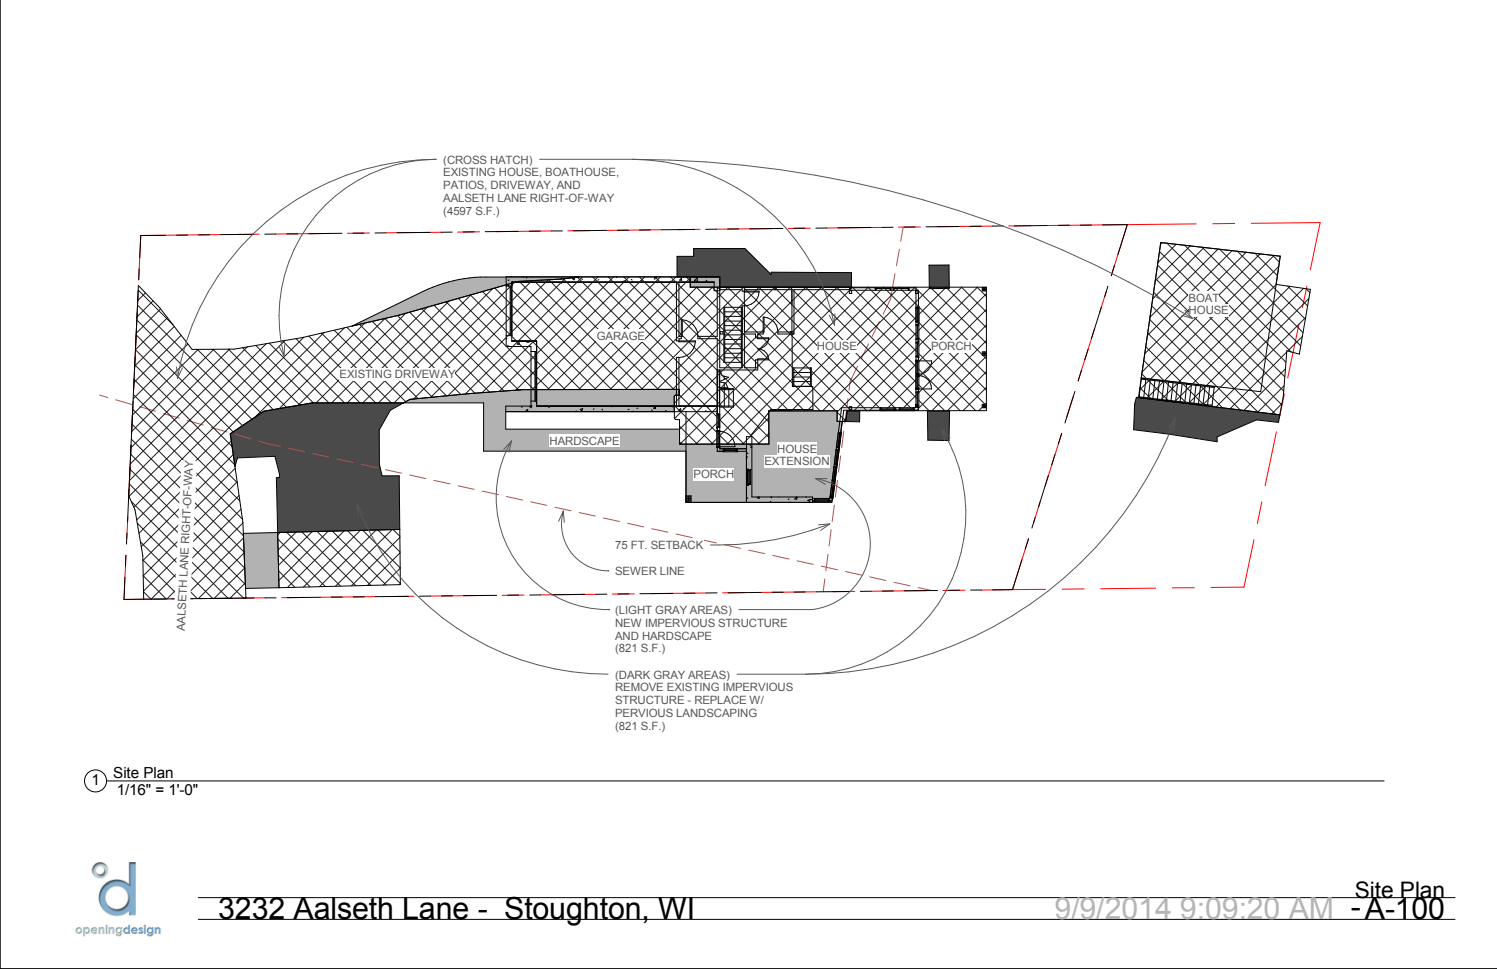
[picture p166: page 1]
BOAT HOUSE; SEWER LINE; PORCH; EXISTING DRIVEWAY; HOUSE; WAY; 75 FT. SETBACK; GARAGE; HARDSCAPE; EXTENSION; 1/16" = 1'-0" 1 Site Plan

(CROSS HATCH)
EXISTING HOUSE, BOATHOUSE,
PATIOS, DRIVEWAY, AND
AALSETH LANE RIGHT-OF-WAY

(LIGHT GRAY AREAS)
NEW IMPERVIOUS STRUCTURE
AND HARDSCAPE

(DARK GRAY AREAS)
REMOVE EXISTING IMPERVIOUS
STRUCTURE - REPLACE W/
PERVIOUS LANDSCAPING

9/9/2014 9:09:20 AM -A-100 Site Plan 3232 Aalseth Lane - Stoughton, WI
